waterbury/e-ink-driver/prior-art/e-ink/Datasheet/FH26-39S-0.3SHW(05).jpg

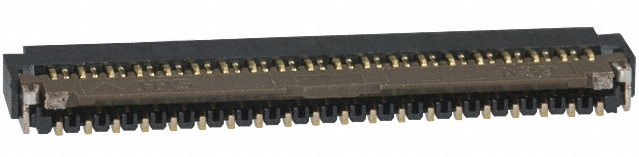
prior-art/e-ink/Datasheet/FH26-39S-0.3SHW(05).jpg
