waterbury/e-ink-driver/prior-art/e-ink/Datasheet/stm32f1xx-TQFP64.png

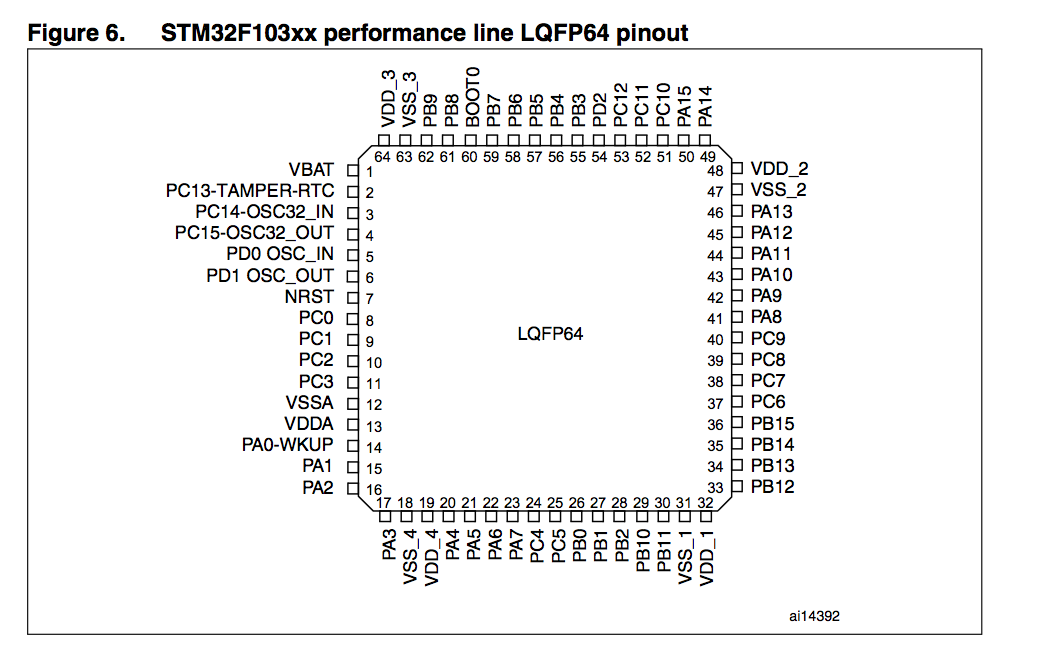
prior-art/e-ink/Datasheet/stm32f1xx-TQFP64.png
