waterbury/e-ink-driver/prior-art/e-ink/Firmware/e-ink-tests-v002/Resources/ED060SC4_driver-master/example_schematics.png

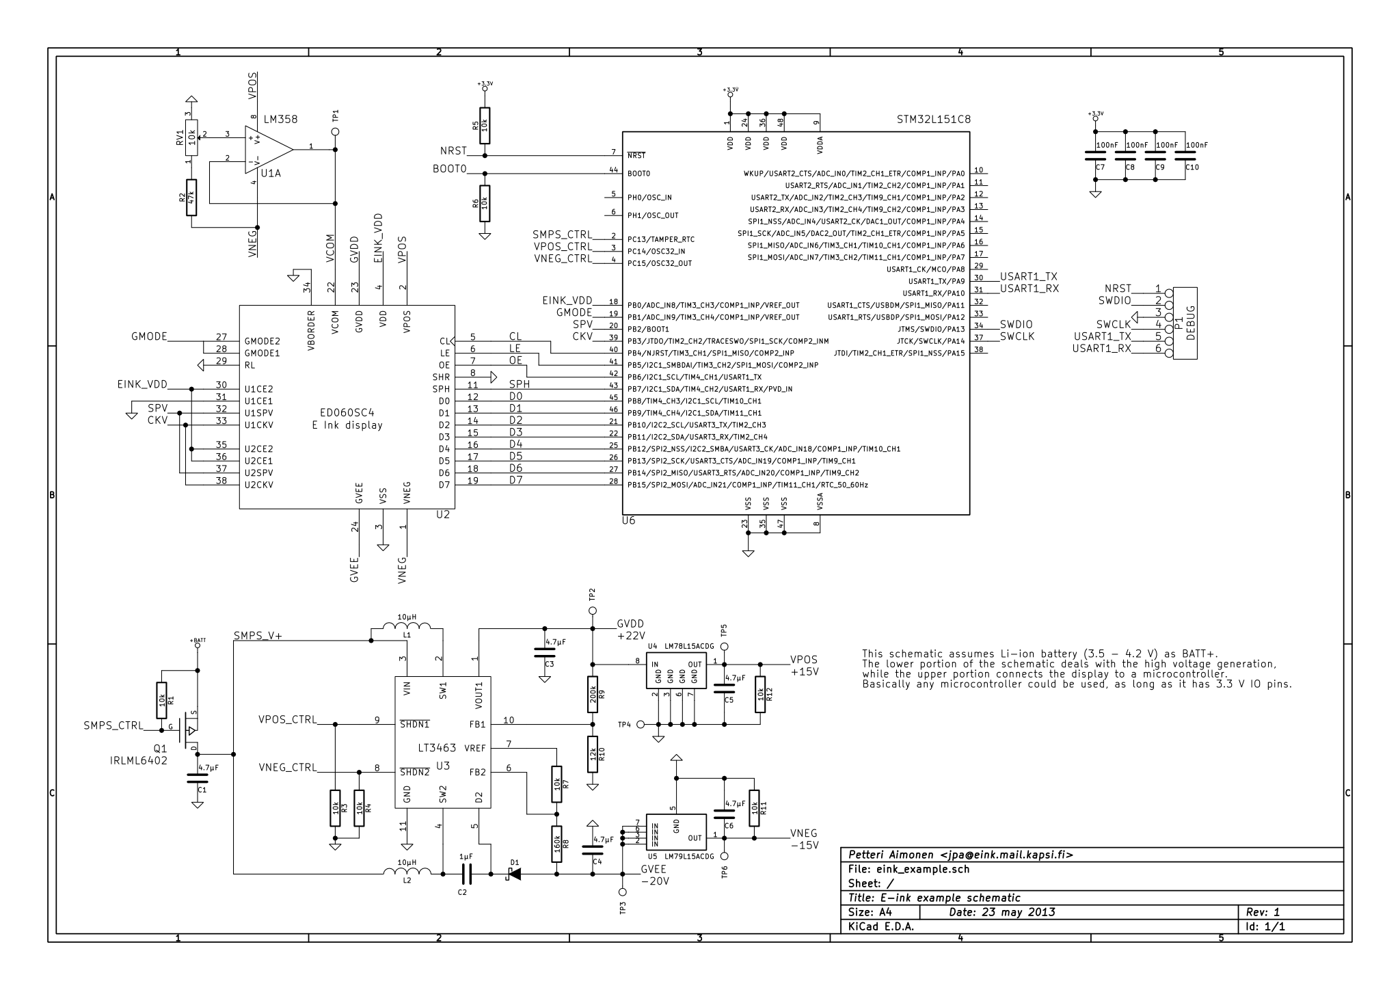
prior-art/e-ink/Firmware/e-ink-tests-v002/Resources/ED060SC4_driver-master/example_schematics.png
