waterbury/e-ink-driver/prior-art/e-ink/Images/v002/2-boards.JPG

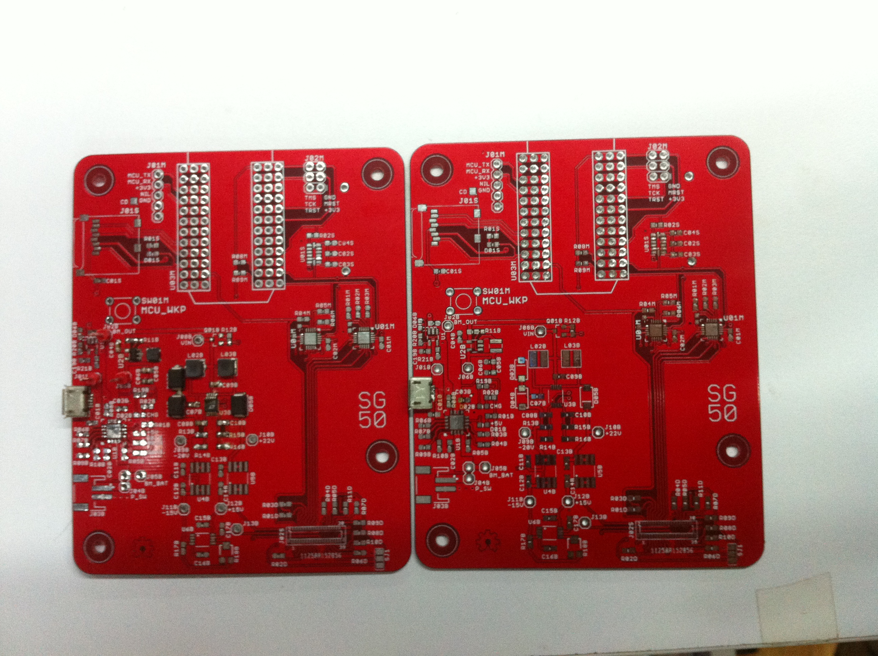
prior-art/e-ink/Images/v002/2-boards.JPG
