waterbury/e-ink-driver/prior-art/e-ink/Images/v002/display-closeup.JPG

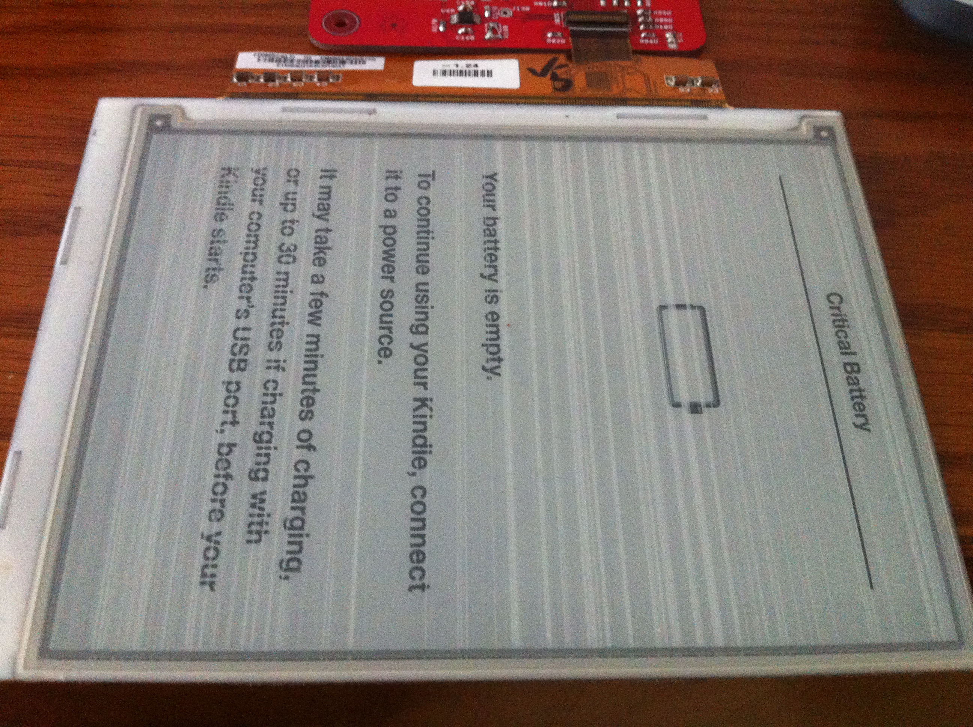
prior-art/e-ink/Images/v002/display-closeup.JPG
