waterbury/e-ink-driver/prior-art/e-ink/Research/example_schematics/schema_esp.png

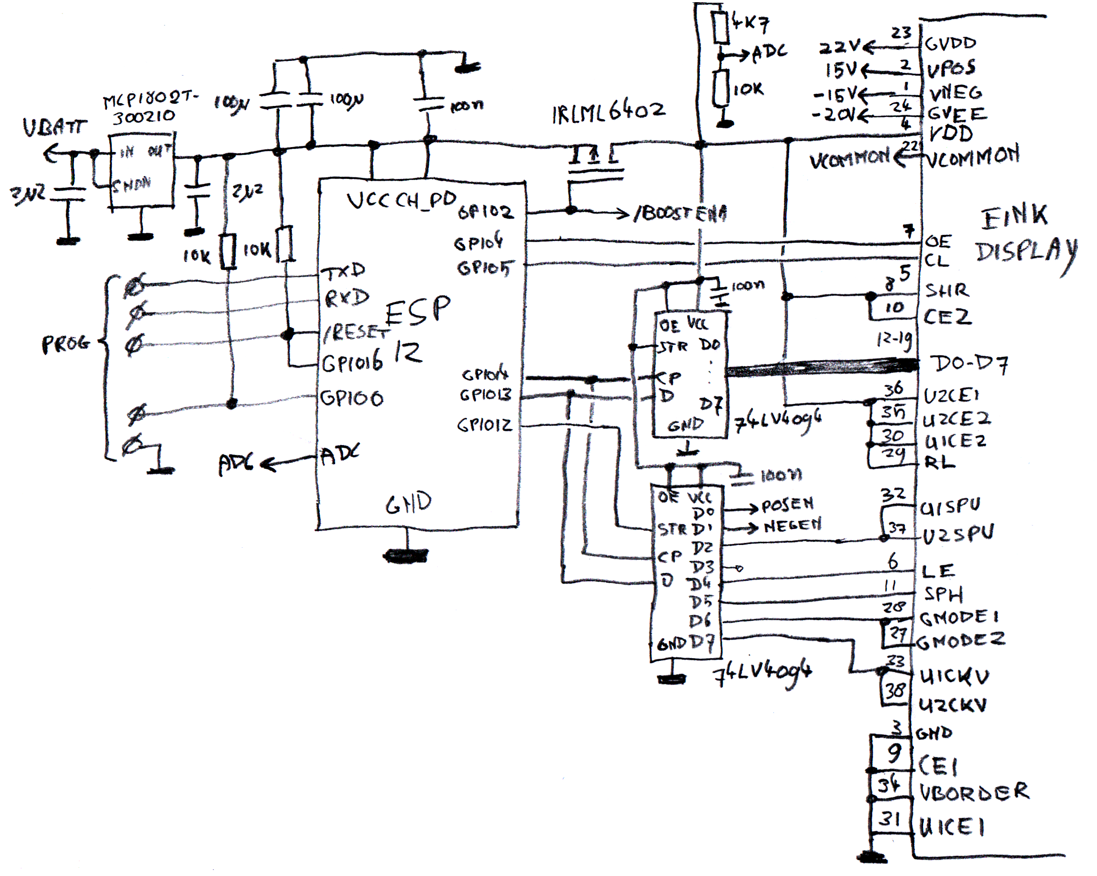
prior-art/e-ink/Research/example_schematics/schema_esp.png
