waterbury/e-ink-driver/prior-art/e-ink/Research/example_schematics/schema_power.png

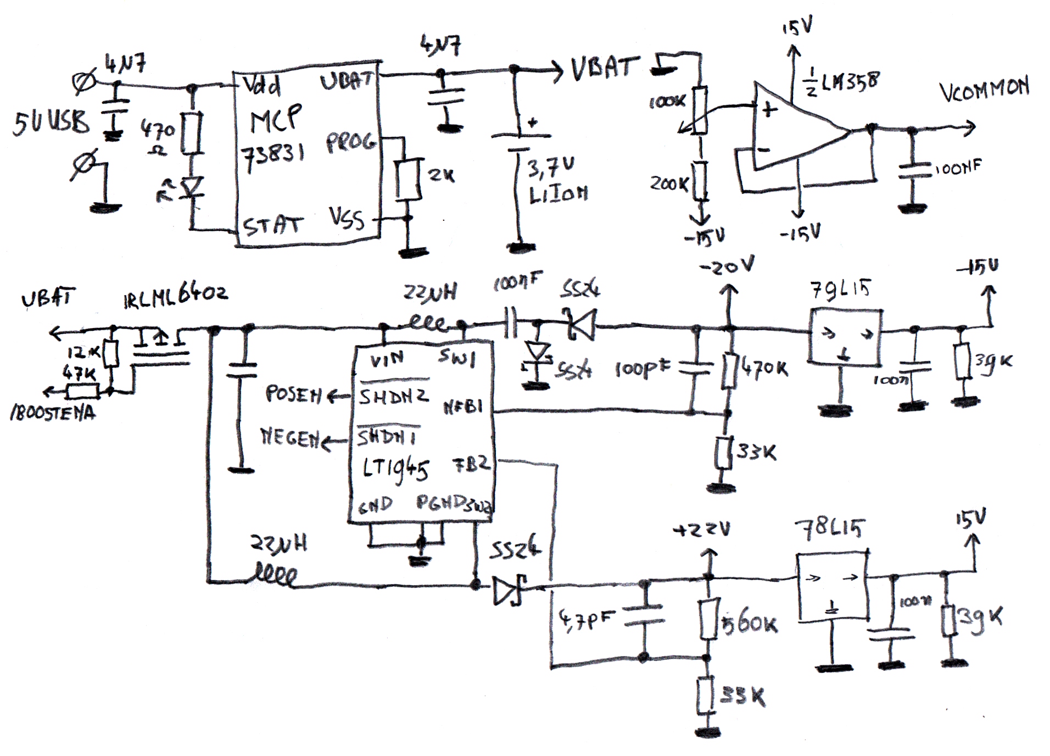
prior-art/e-ink/Research/example_schematics/schema_power.png
