waterbury/e-ink-driver/prior-art/e-ink/Research/example_schematics/Screen Shot 2015-03-17 at 8.35.07.png

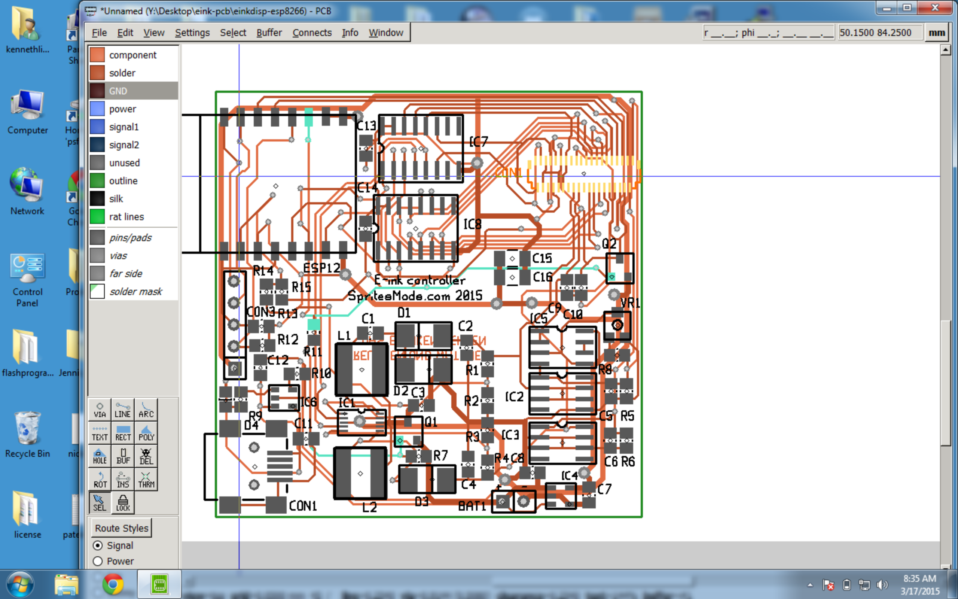
prior-art/e-ink/Research/example_schematics/Screen Shot 2015-03-17 at 8.35.07.png
