waterbury/e-ink-driver/prior-art/e-ink/Research/G6_eink_schematic.png

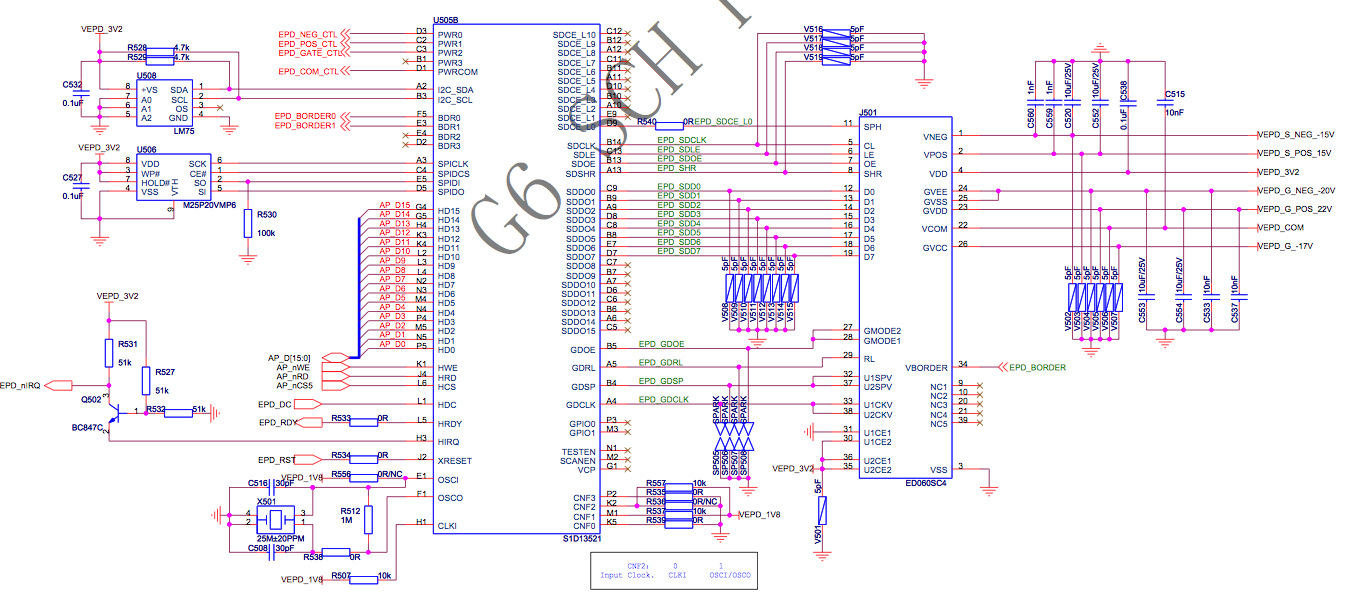
prior-art/e-ink/Research/G6_eink_schematic.png
