waterbury/e-ink-driver/prior-art/e-ink/Research/USB_DISC.png

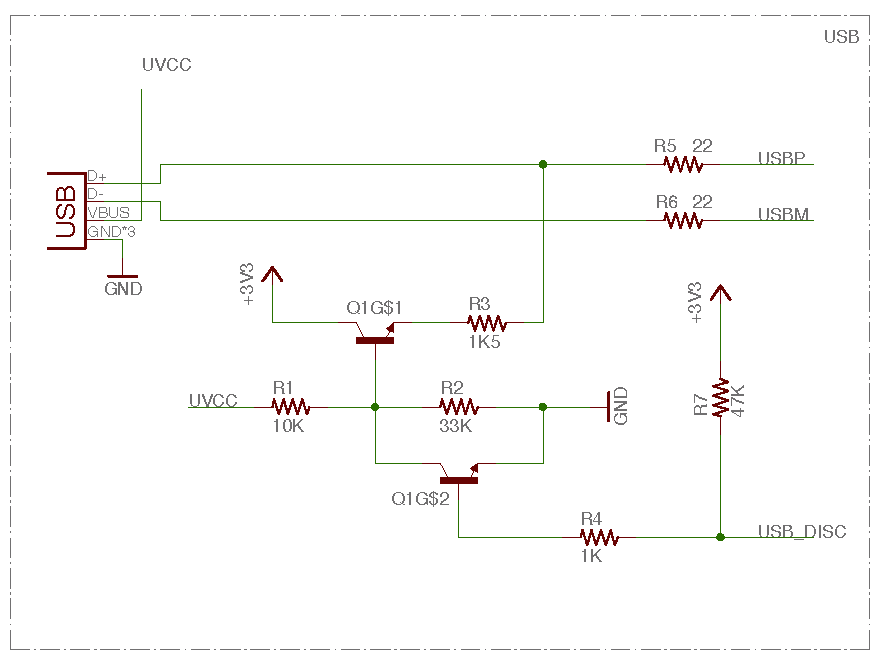
prior-art/e-ink/Research/USB_DISC.png
