waterbury/e-ink-driver/prior-art/e-ink/Bring-up/V020/V020-notes-print.pages/preview-web.jpg

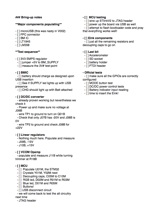
prior-art/e-ink/Bring-up/V020/V020-notes-print.pages/preview-web.jpg
