waterbury/e-ink-driver/prior-art/e-ink/Bring-up/V020/Screenshots/ground-plane.png

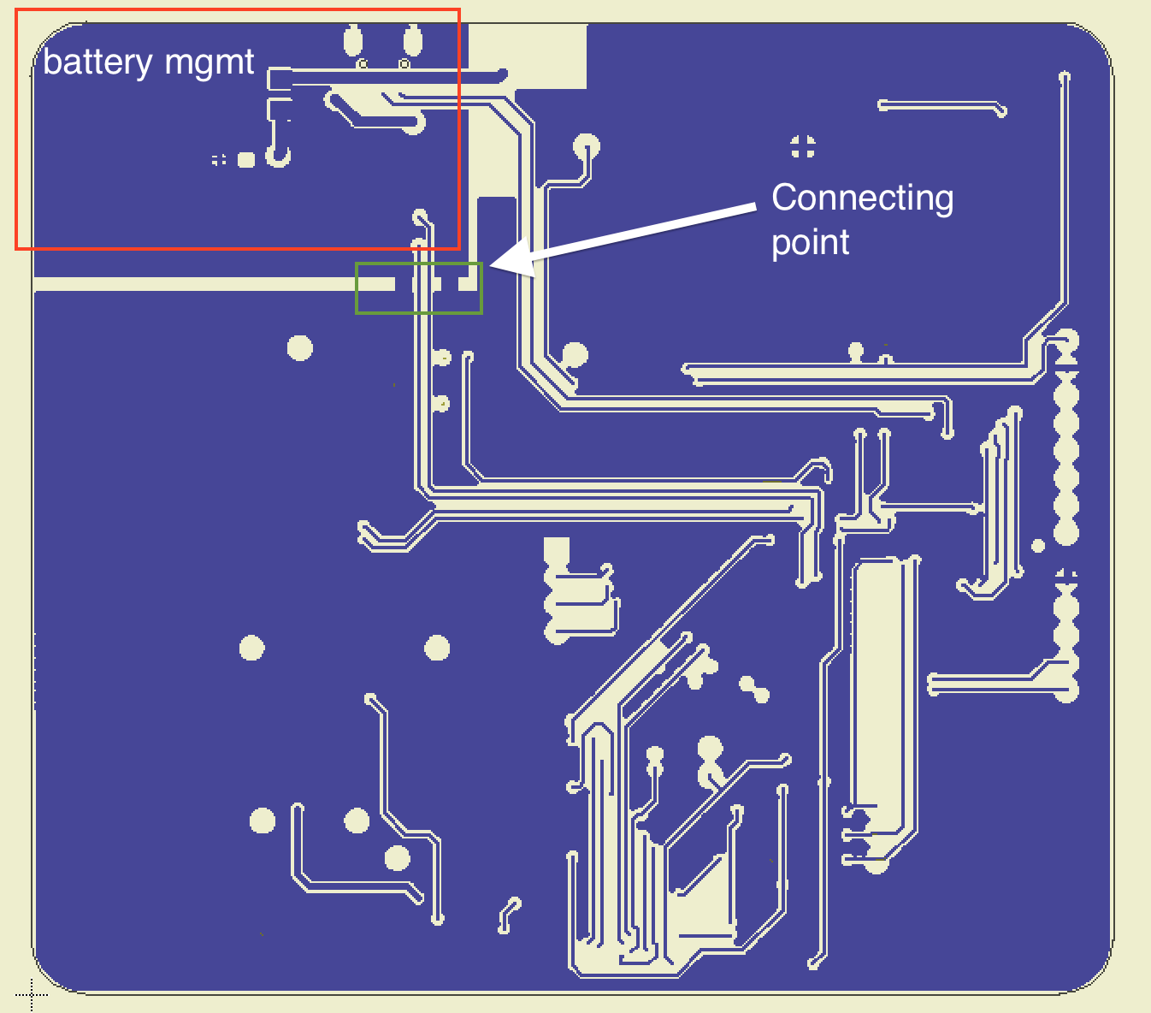
prior-art/e-ink/Bring-up/V020/Screenshots/ground-plane.png
