waterbury/e-ink-driver/prior-art/e-ink/EAGLE/e-ink-display-v120/e-ink-display-v120/e-ink-display-v120/e-ink-display-v120.pdf

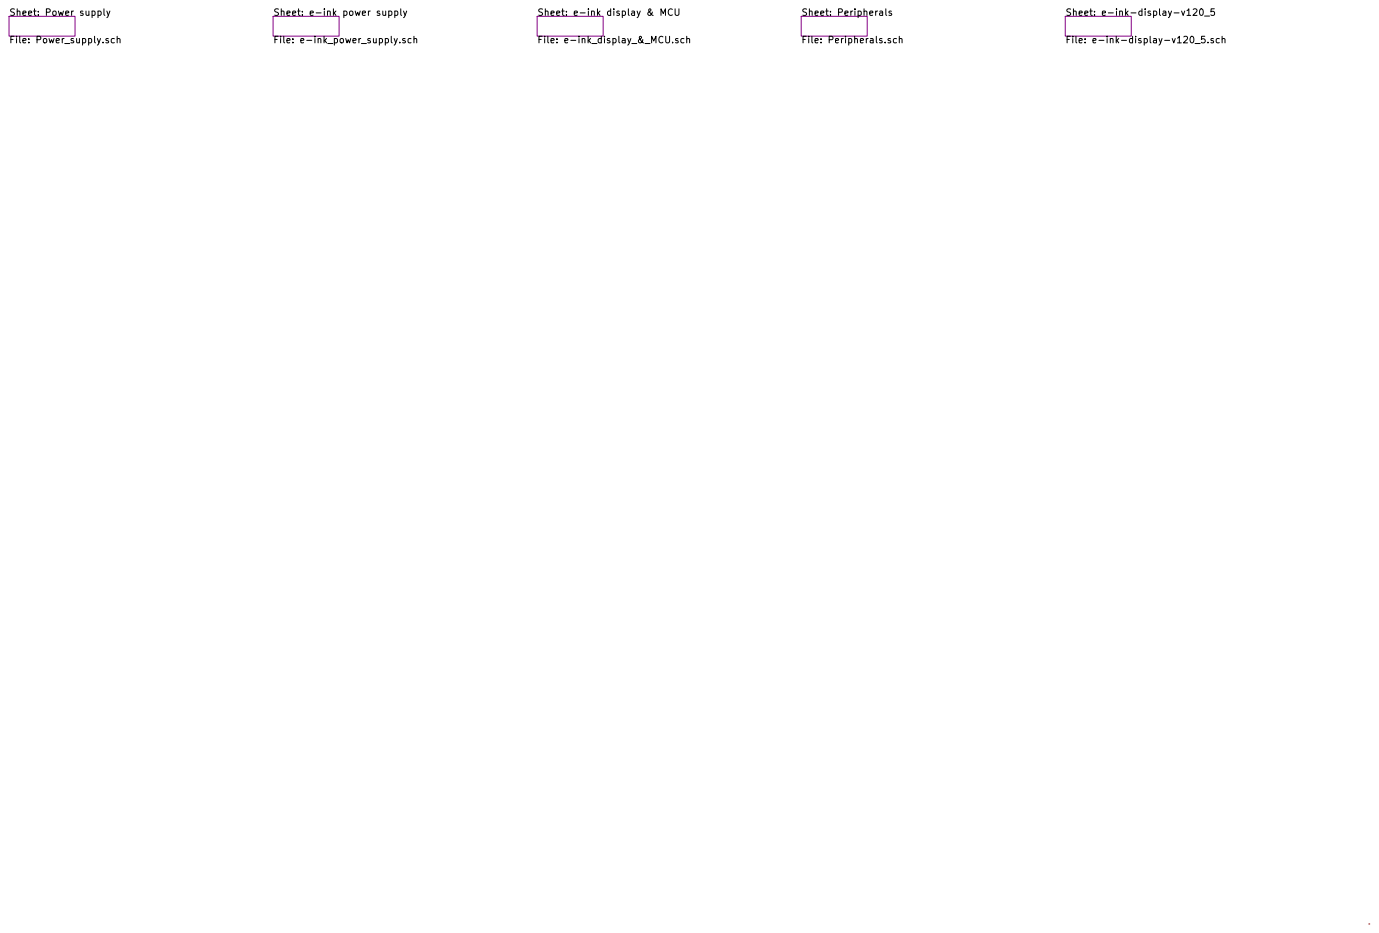
[picture p19: page 1]

Sheet: e-ink power supply

Sheet: e-ink display & MCU

File: e-ink-display-v120_5.sch

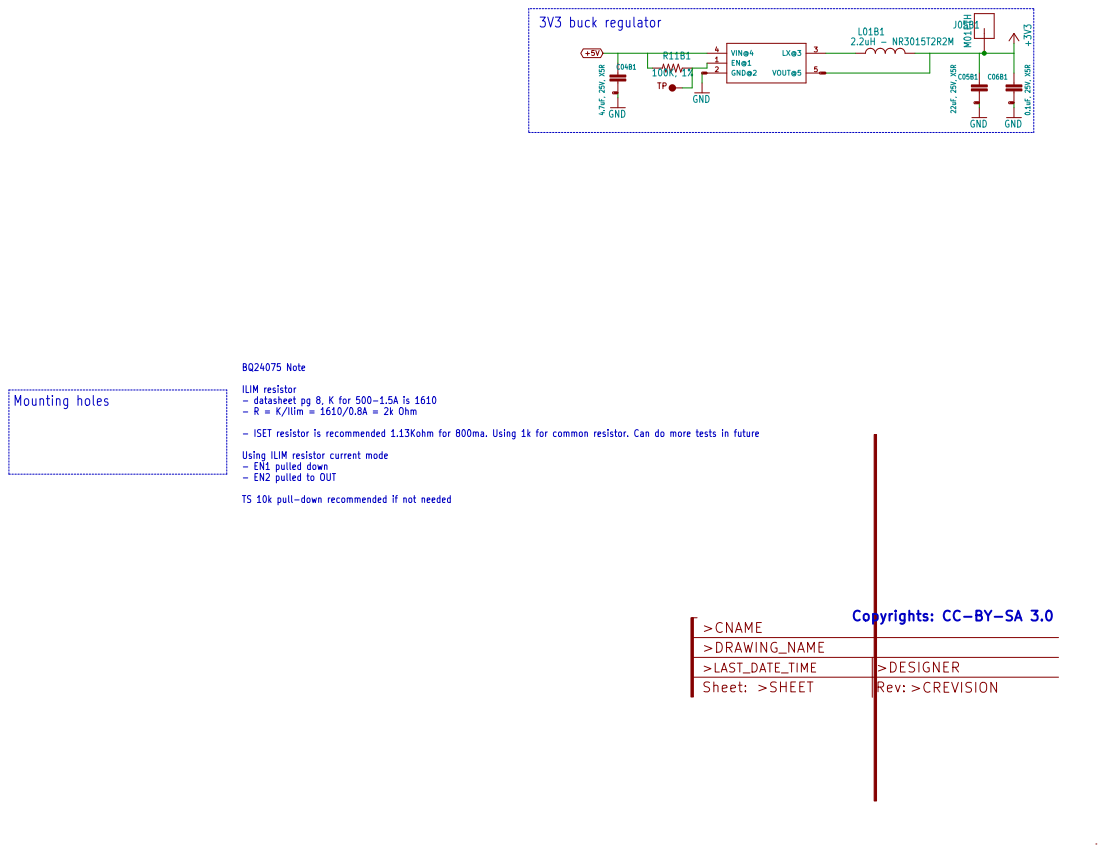
[picture p20: page 2]

ILIM resistor
- datasheet pg 8, K for 500-1.5A is 1610
- R = K/Ilim = 1610/0.8A = 2k Ohm

- ISET resistor is recommended 1.13Kohm for 800ma. Using 1k for common resistor. Can do more tests in future

Using ILIM resistor current mode
- EN1 pulled down
- EN2 pulled to OUT

TS 10k pull-down recommended if not needed

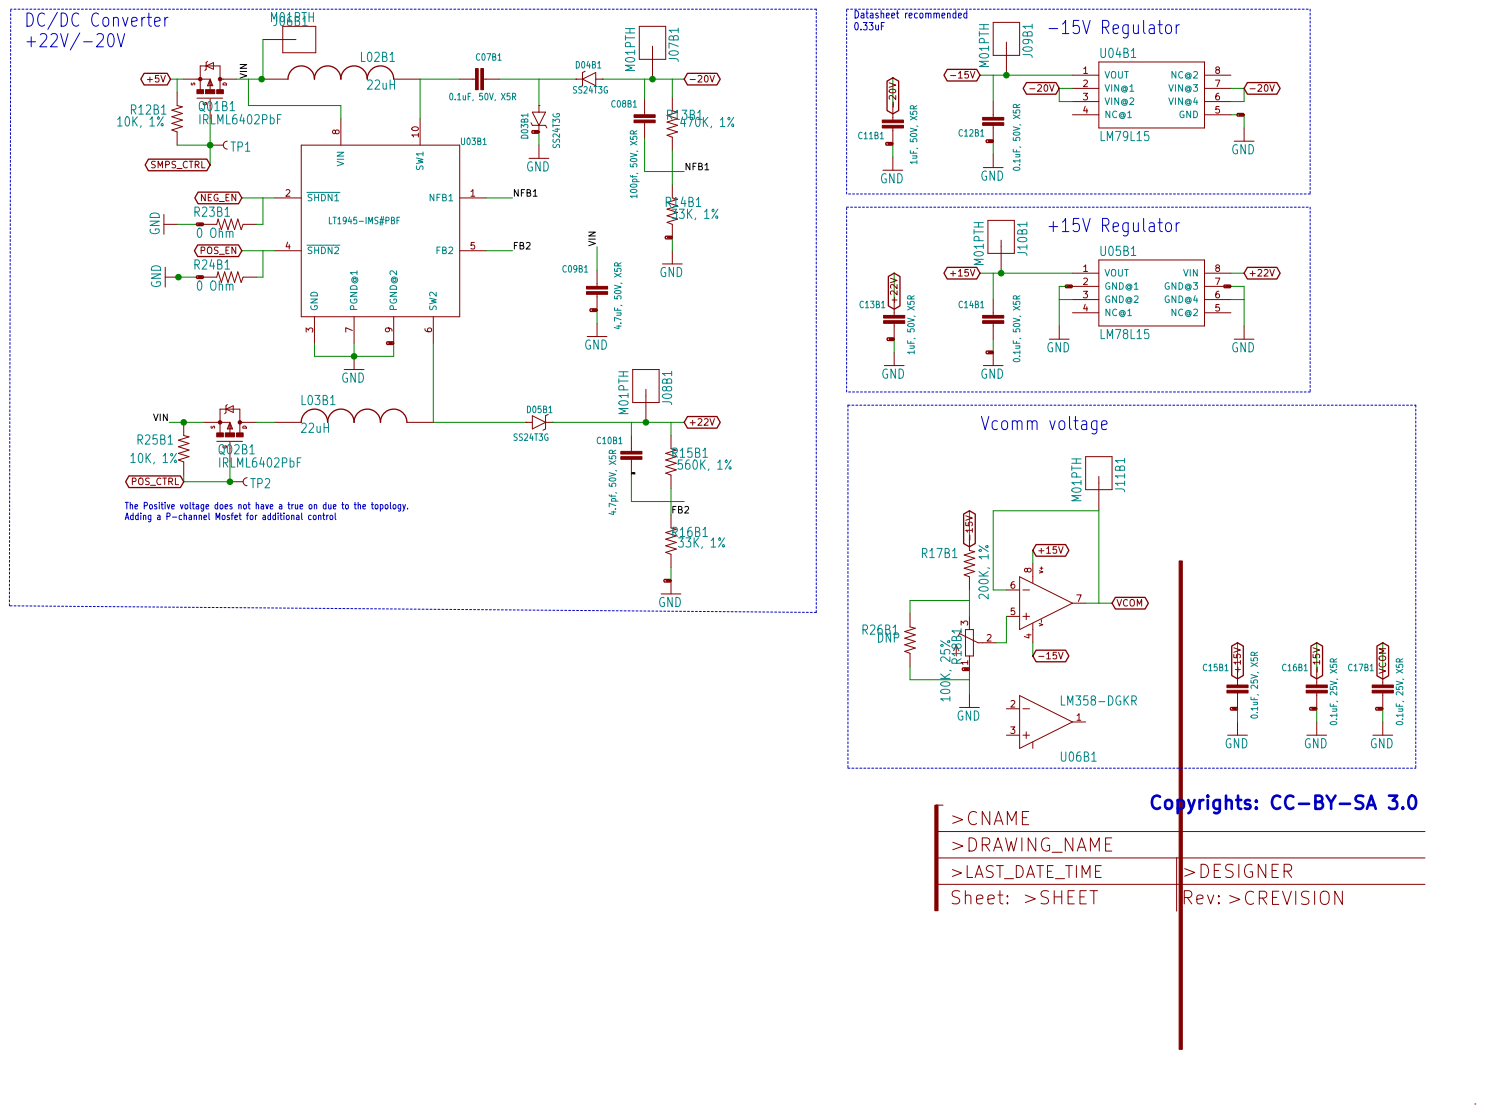
[picture p21: page 3]

FB2 FB2 The Positive voltage does not have a true on due to the topology.

Adding a P-channel Mosfet for additional control

Copyrights: CC-BY-SA 3.0

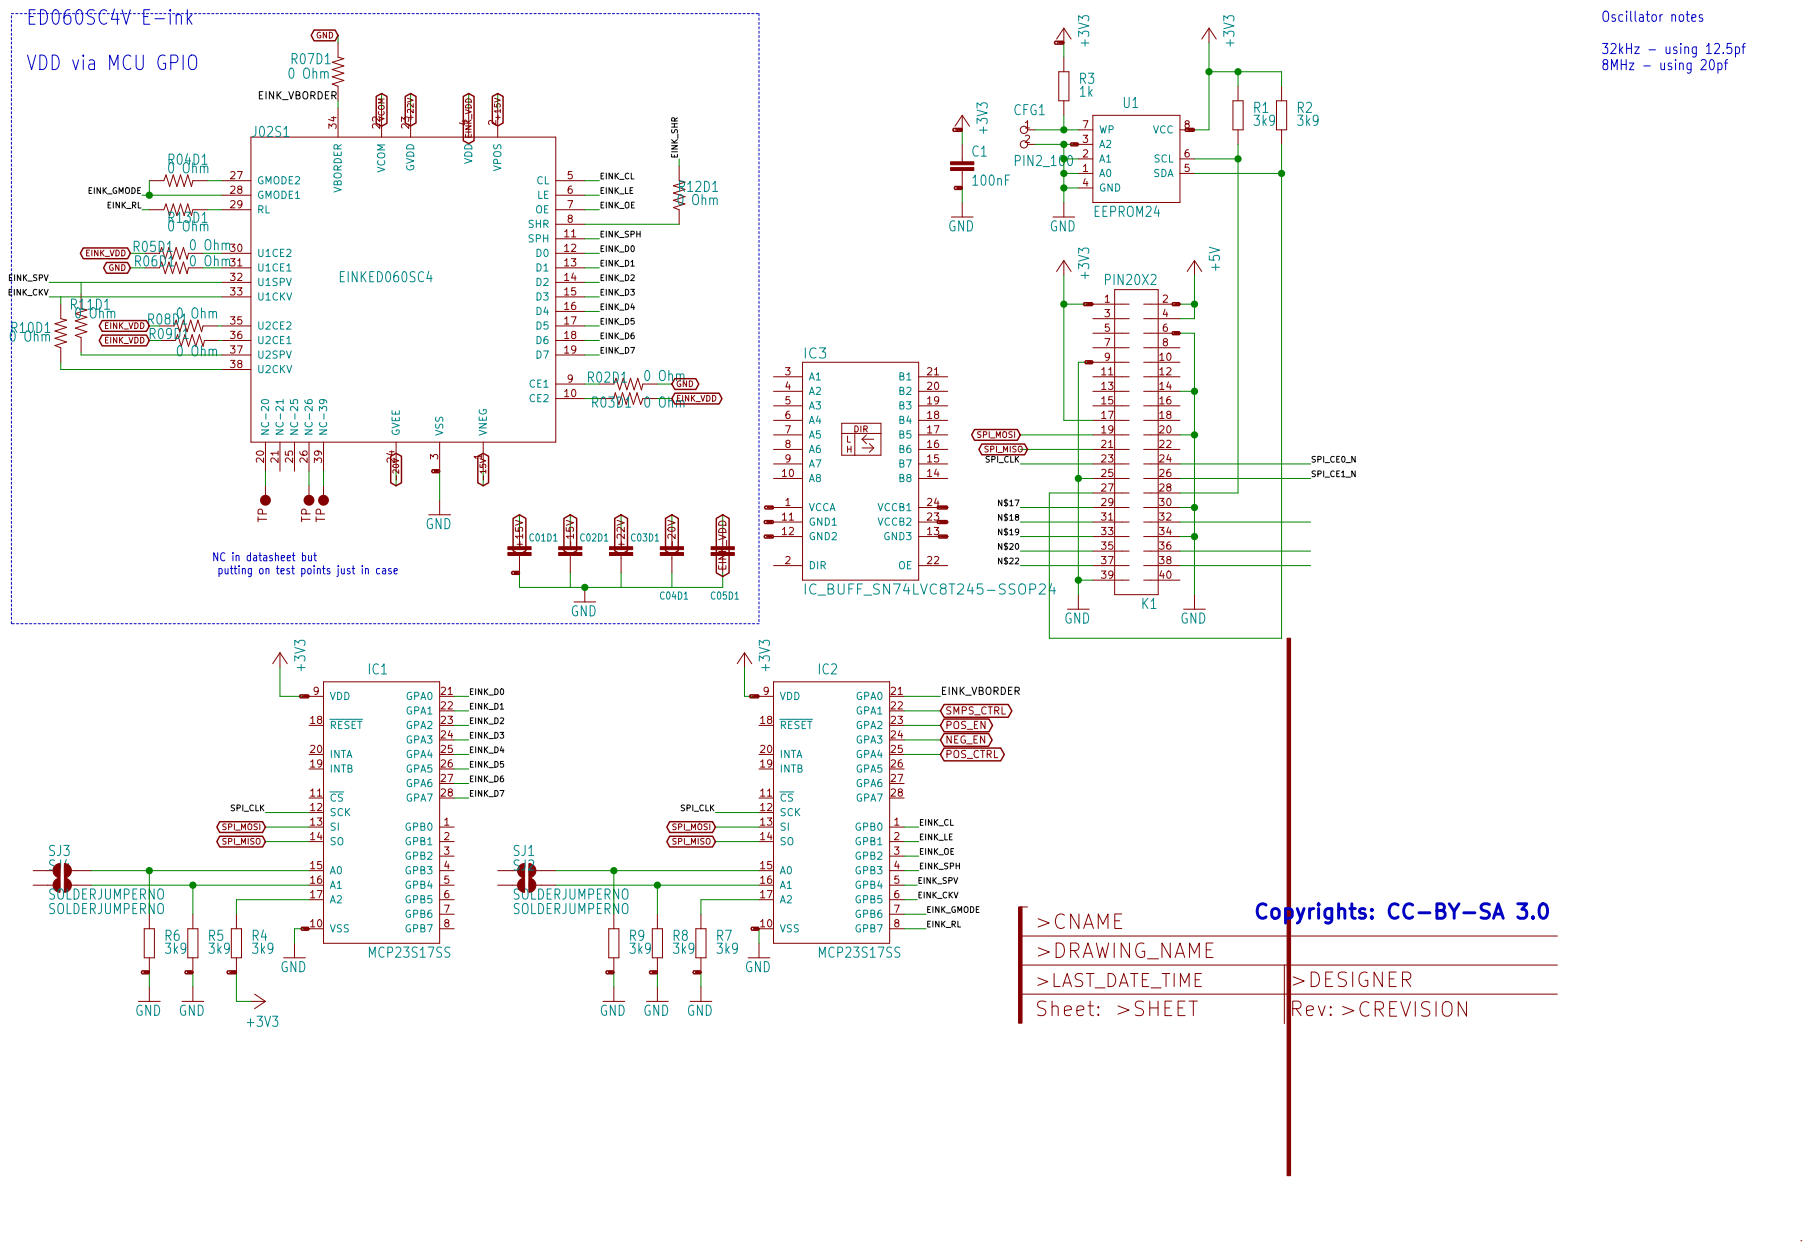
[picture p22: page 4]

VDD via MCU GPIO

2 NC-20 20 NC-21 21 VCOM 22 GVDD 23 GVEE 24 NC-25 25 NC-26 26 GMODE2 27 GMODE1 28 RL 29 VSS
3k9 VNEG

23 | | 24
25 | | 26
27 | | 28
29 | | 30
31 | | 32
33 | | 34
35 | | 36
37 | | 38
39 | | 40

NC in datasheet but
putting on test points just in case

Copyrights: CC-BY-SA 3.0

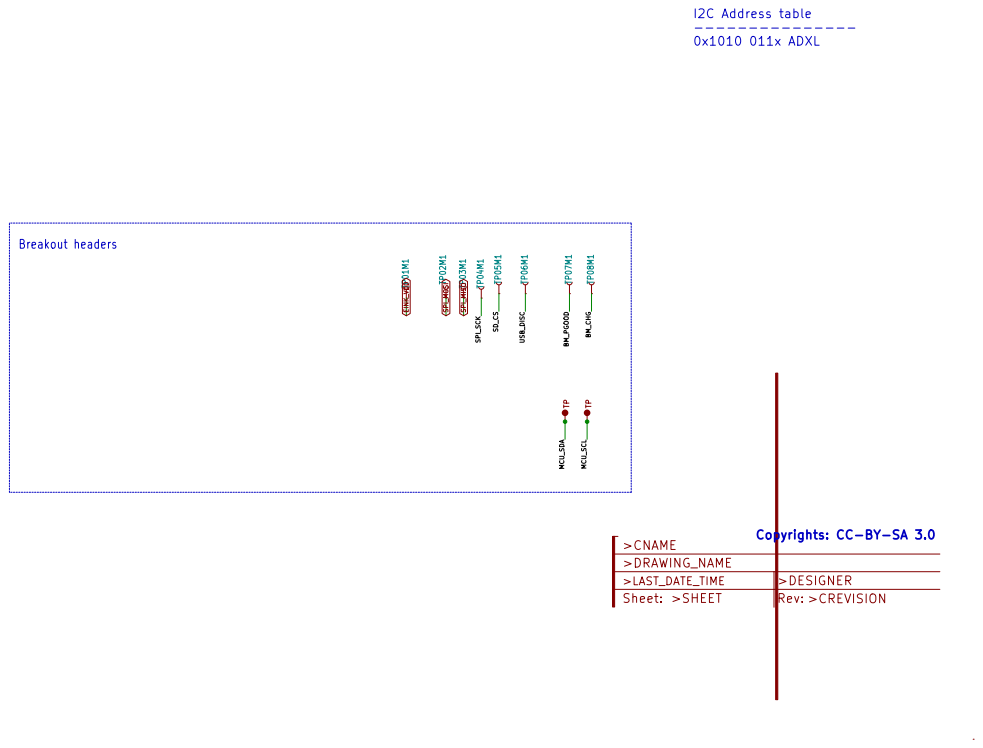
[picture p23: page 5]

Copyrights: CC-BY-SA 3.0

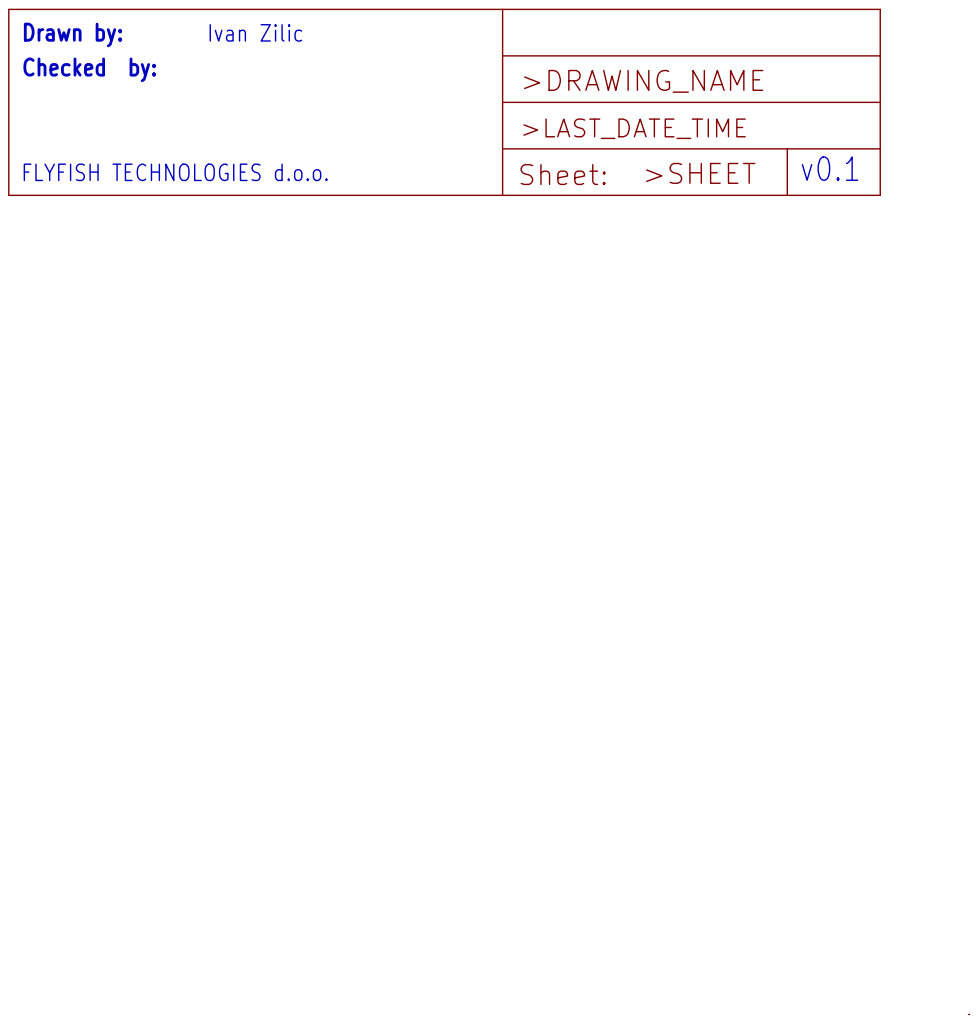
[picture p24: page 6]
