waterbury/e-ink-driver/prior-art/e-ink/Research/example_schematics/eink-pcb/einkdisp-esp8266.pdf

# einkdisp-esp8266

# 1. Table of Contents (This Page) Created on Sun Feb 15 16:48:41 2015

# 2. component 3. solder 4. outline 5. plated-drill 6. componentmask 7. soldermask 8. topsilk 9. bottomsilk 10. toppaste 11. topassembly 12. bottomassembly 13. fab

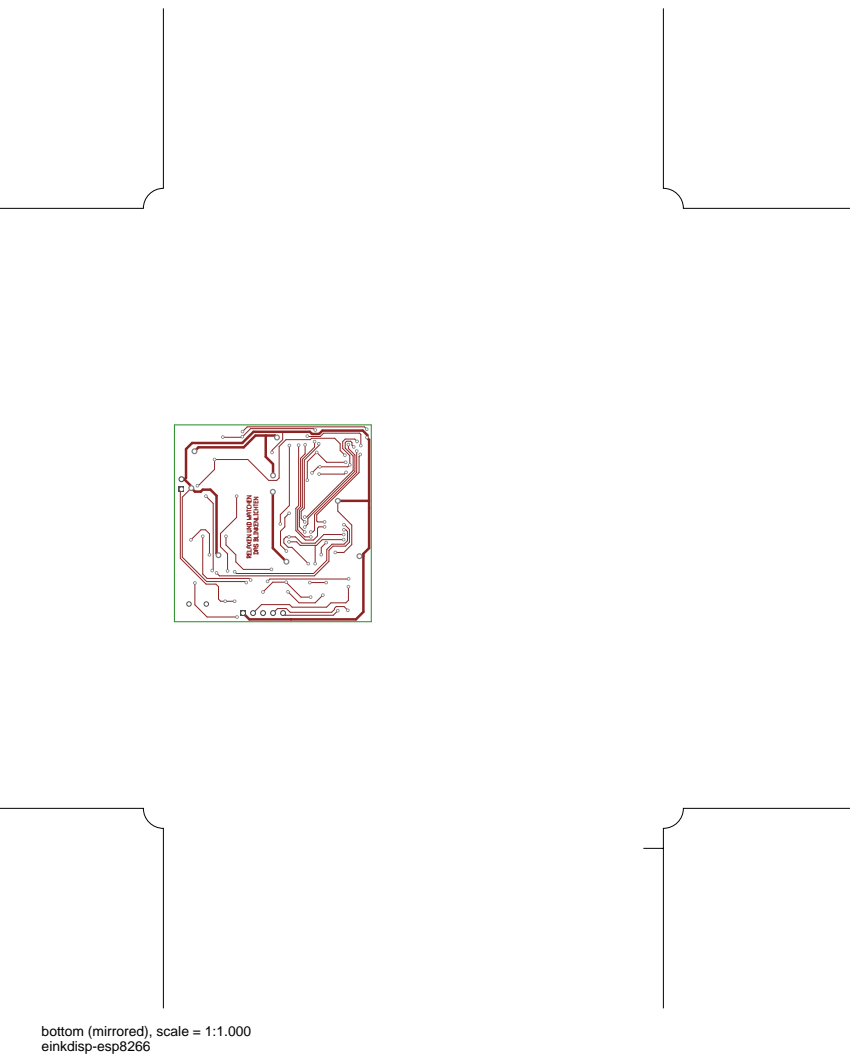
[picture p25: page 2]

bottom (mirrored), scale = 1:1.000

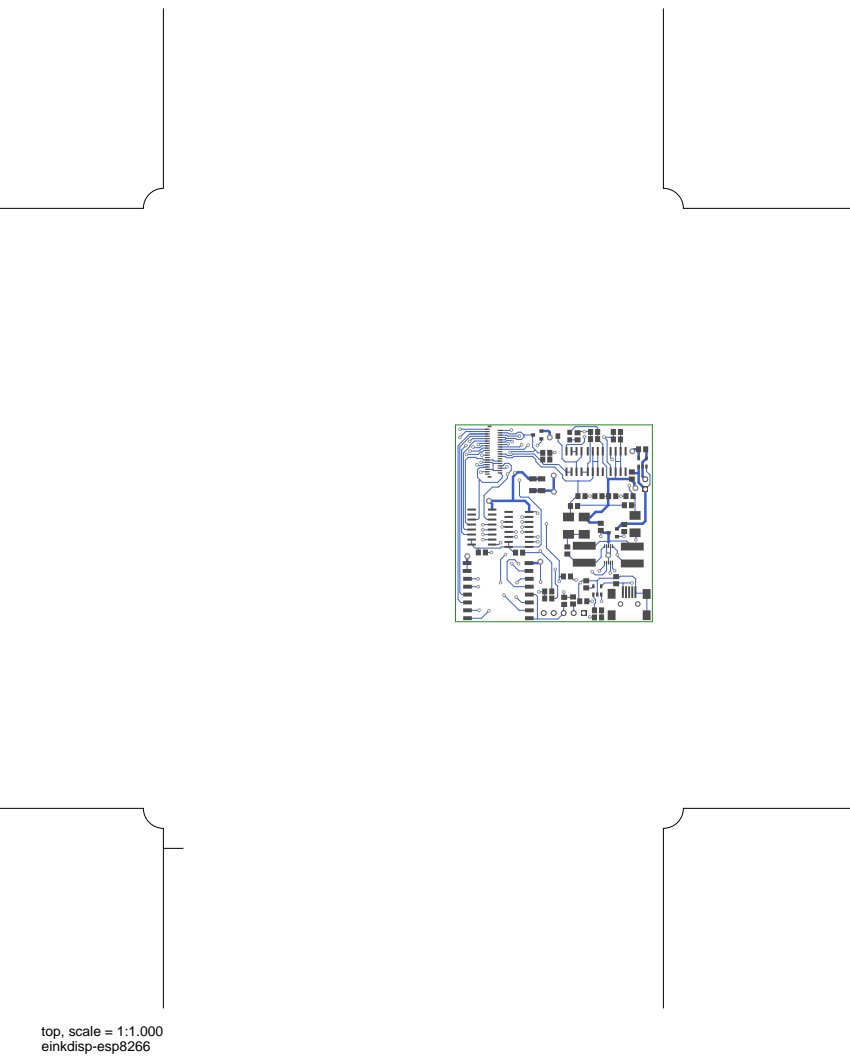
[picture p26: page 3]
top, scale = 1:1.000

outline, scale = 1:1.000

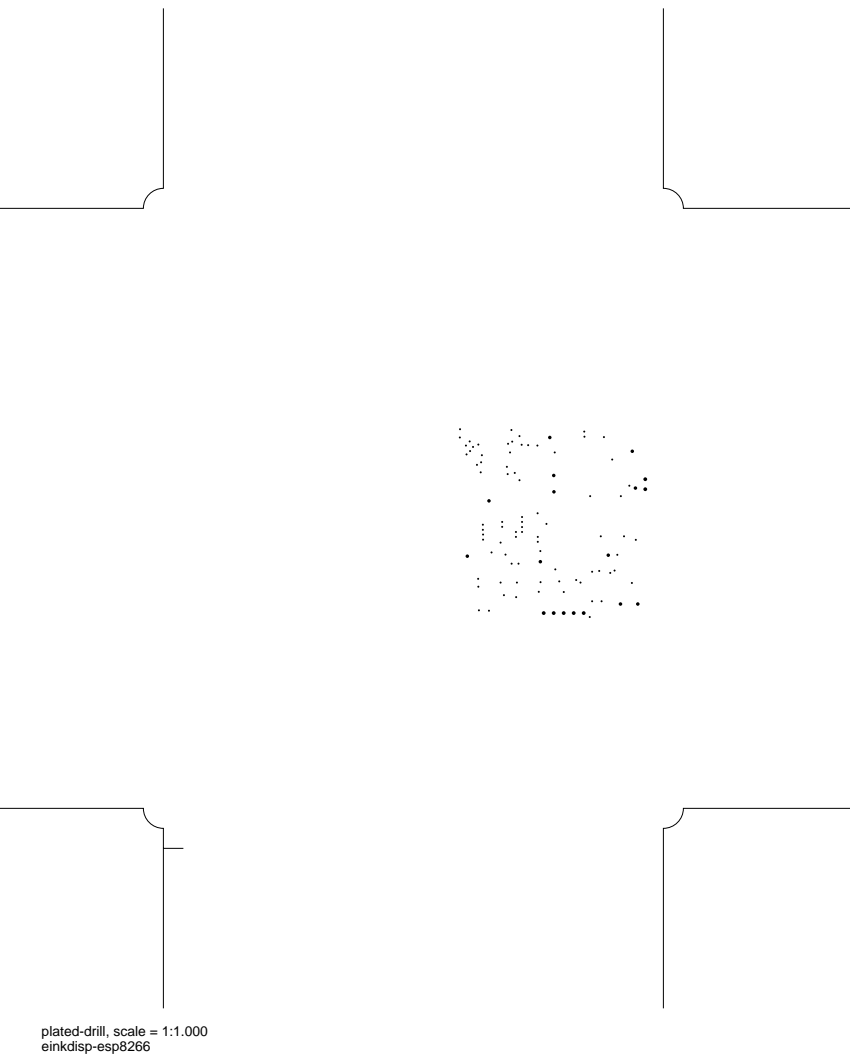
[picture p27: page 5]

plated-drill, scale = 1:1.000

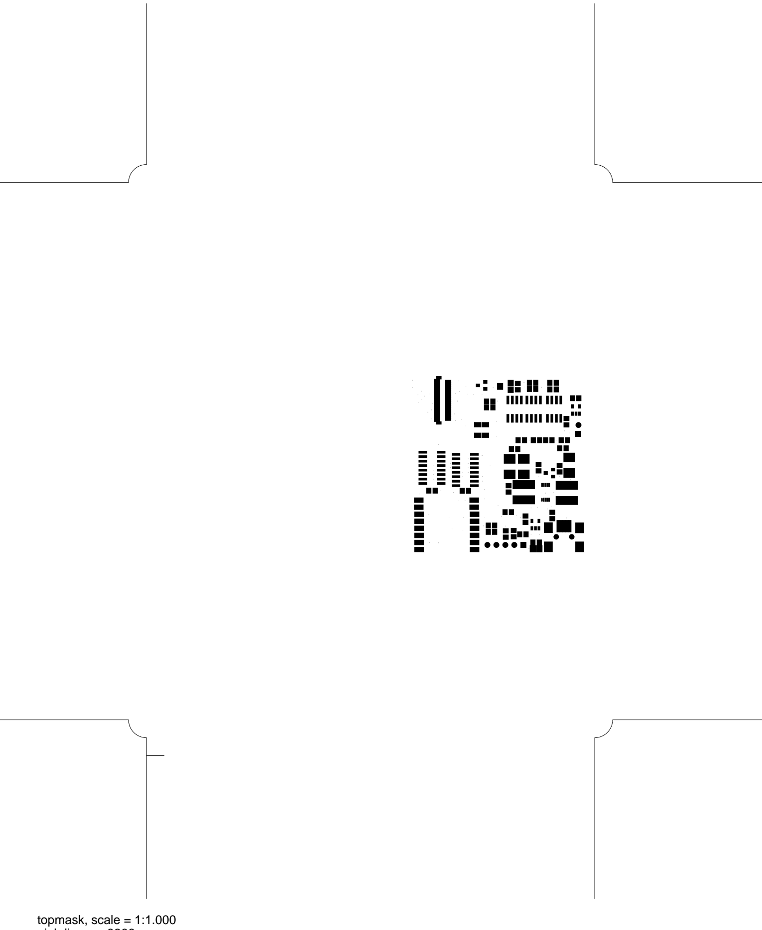
[picture p28: figure]
topmask, scale = 1:1.000

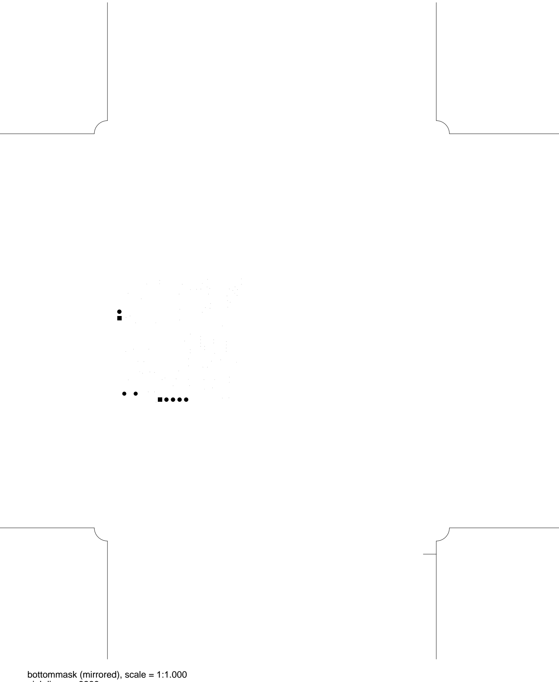
[picture p29: figure]
bottommask (mirrored), scale = 1:1.000
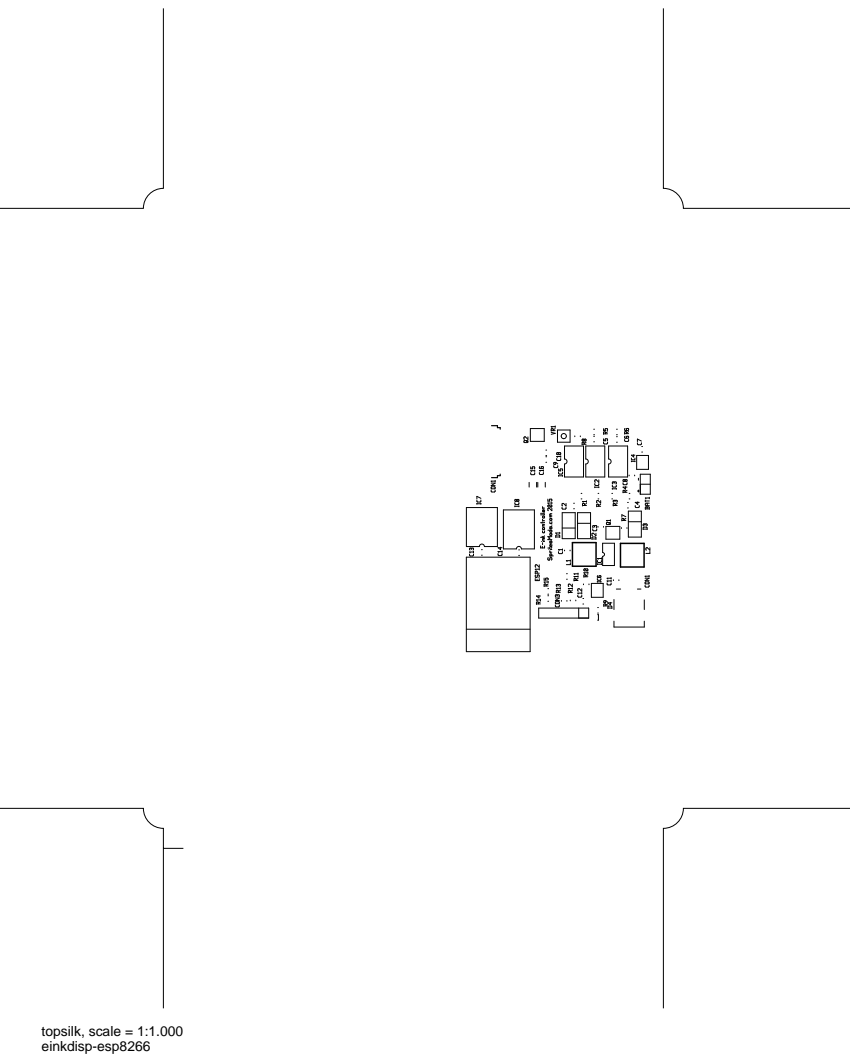
[picture p30: page 8]
topsilk, scale = 1:1.000

bottomsilk (mirrored), scale = 1:1.000

toppaste, scale = 1:1.000

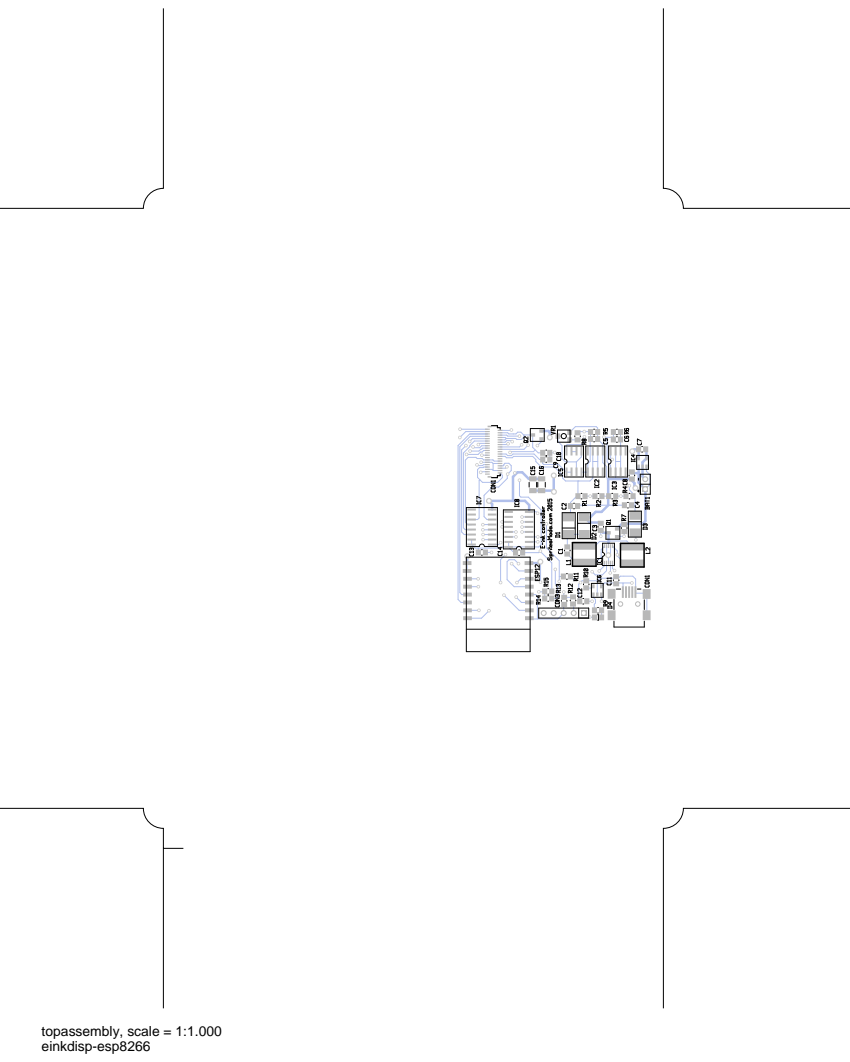
[picture p31: page 11]
topassembly, scale = 1:1.000

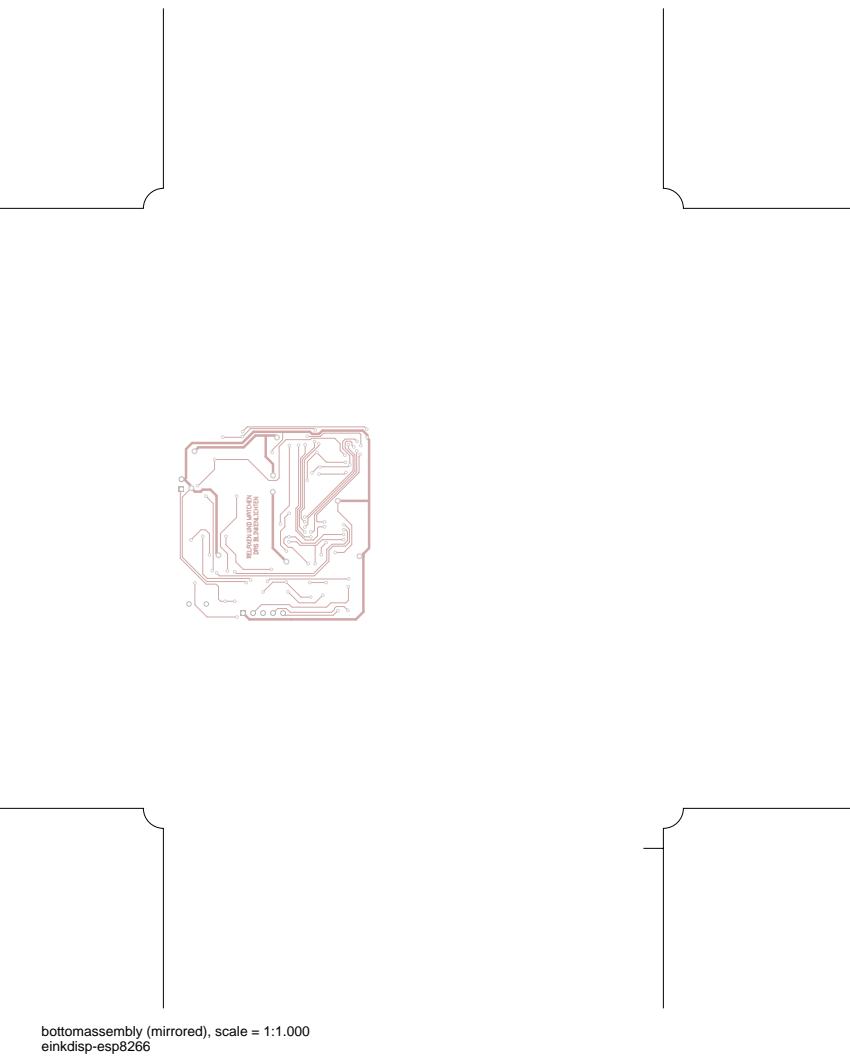
[picture p32: page 12]

bottomassembly (mirrored), scale = 1:1.000

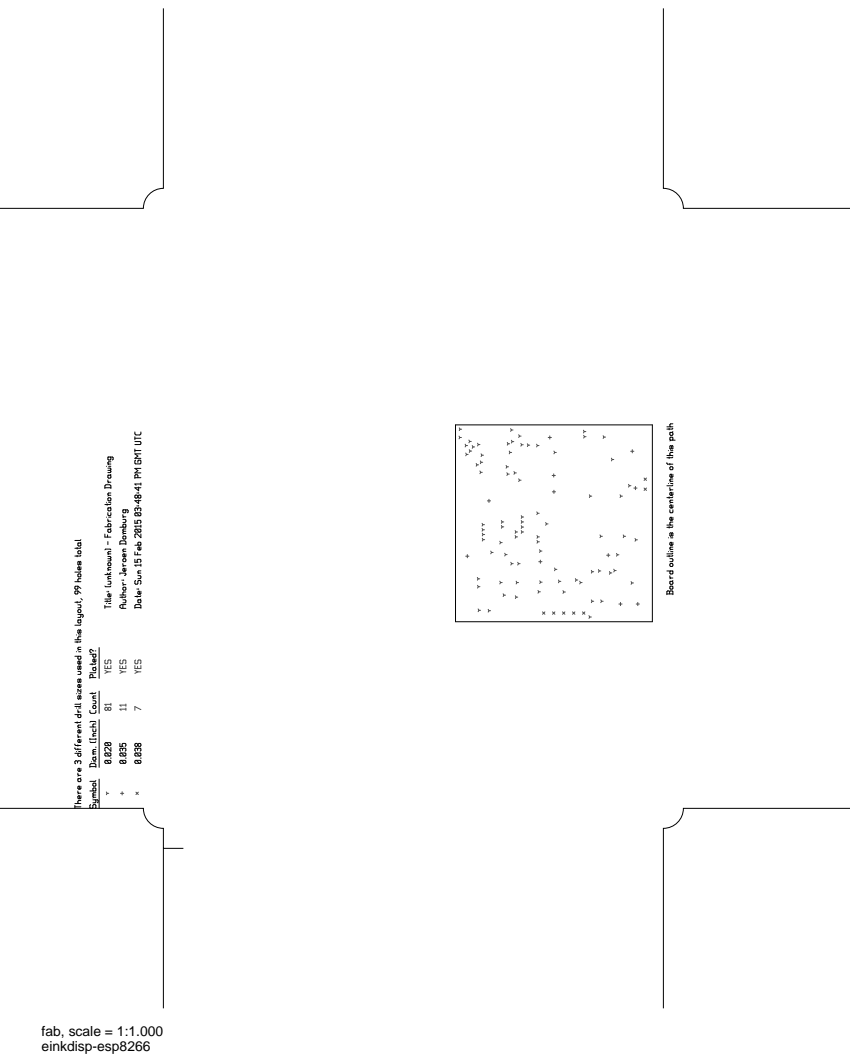
[picture p33: page 13]
fab, scale = 1:1.000
