waterbury/e-ink-driver/prior-art/e-ink/Research/G6_ebook_reader_schematics.pdf

D

D

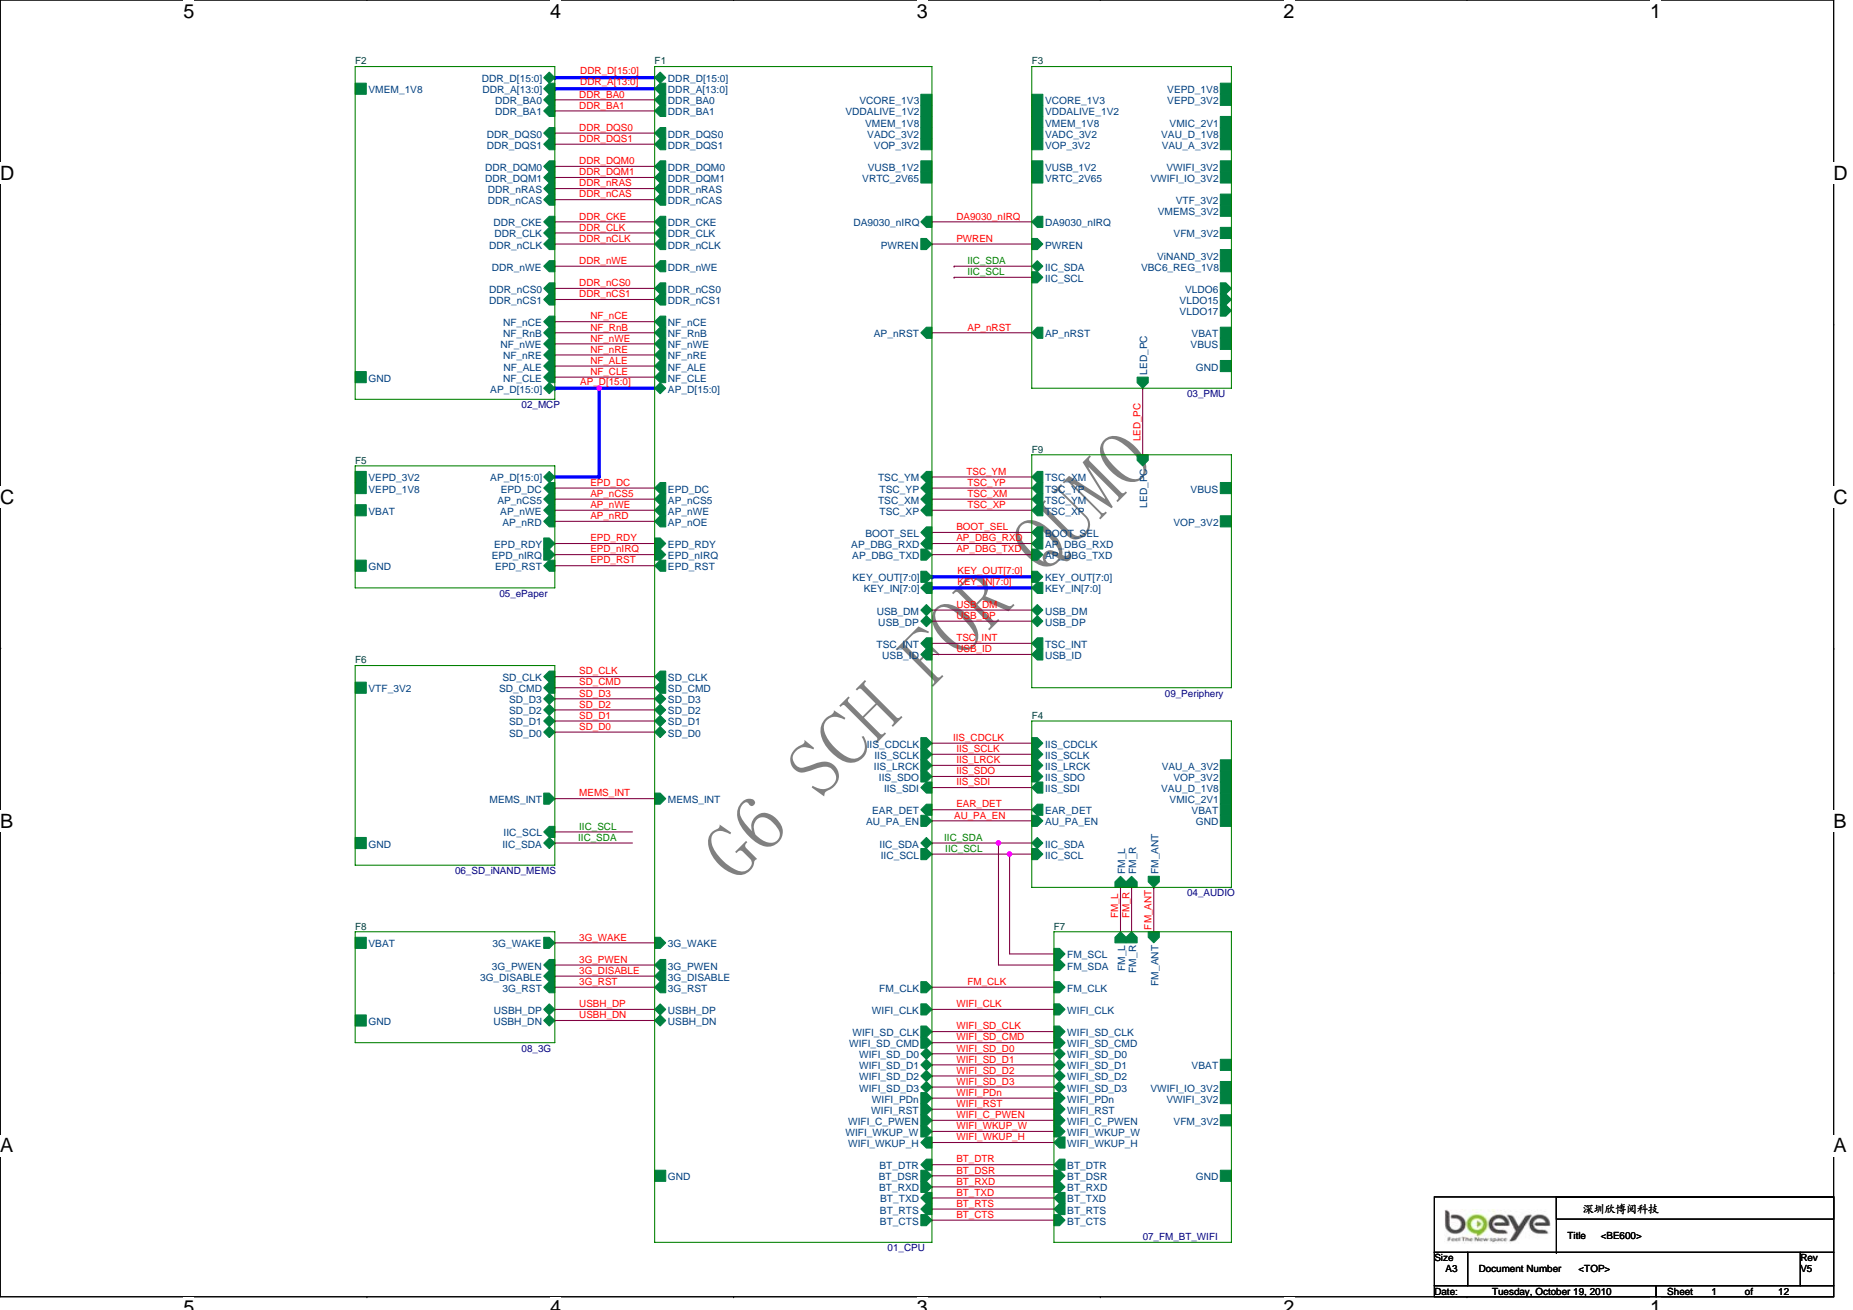
[picture p34: page 1]
DDR_BA0; DDR_D[15:0] DDR_A[13:0]; DDR_BA1; DDR_DQS0 DDR_DQS1; DDR_DQM0 DDR_DQM1 DDR_nRAS DDR_nCAS; DDR_CKE DDR_CLK DDR_nCLK; DDR_nWE; DDR_nCS0 DDR_nCS1; NF_nCE NF_RnB NF_nWE NF_nRE NF_ALE NF_CLE; AP_nRST; DA9030_nIRQ; PWREN; EPD_DC; EPD_RDY; IIS_CDCLK IIS_SCLK IIS_LRCK IIS_SDO IIS_SDI; IIC_SDA IIC_SCL; SD_CLK SD_CMD SD_D3 SD_D2 SD_D1 SD_D0; IIC_SCL; IIC_SDA; IIC_SCL IIC_SDA; EAR_DET; TSC_YM TSC_YP; KEY_IN[7:0]; USB_DM USB_DP; USB_ID; FM_ANT; AP_DBG_RXD; TSC_INT; LED_PC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

G6 SCH FOR QUMO

AP_nCS5 | TSC_XM
AP_nWE | TSC_XP
AP_nRD | BOOT_SEL

EPD_nIRQ | AP_DBG_TXD
EPD_RST | KEY_OUT[7:0]

USBH_DP | WIFI_CLK
USBH_DN | WIFI_SD_CLK

Size A3 | Document Number <TOP> <TOP> <TOP> | Rev V5 V5 V5

Date: Tuesday, October 19, 2010 Tuesday, October 19, 2010 Tuesday, October 19, 2010 | Sheet 1 1 1 of 12 12 12

5 | 4 | 3 | 2 | 1

D

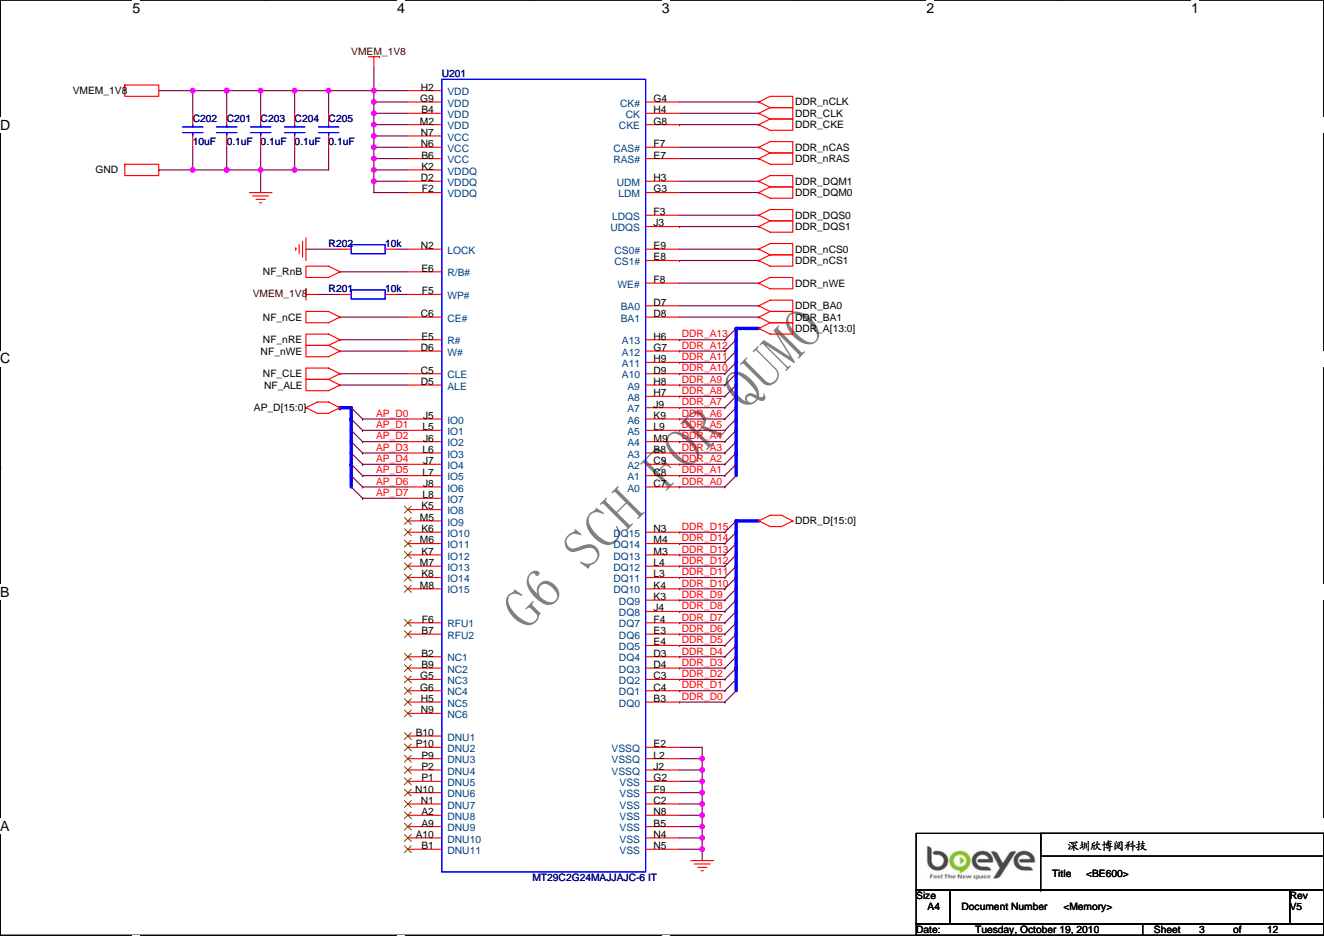
[picture p35: page 2]

<Memory> <Memory> <Memory> | V5 V5 V5

Tuesday, October 19, 2010 Tuesday, October 19, 2010 Tuesday, October 19, 2010 | 3 3 3 12 12 12

D | D

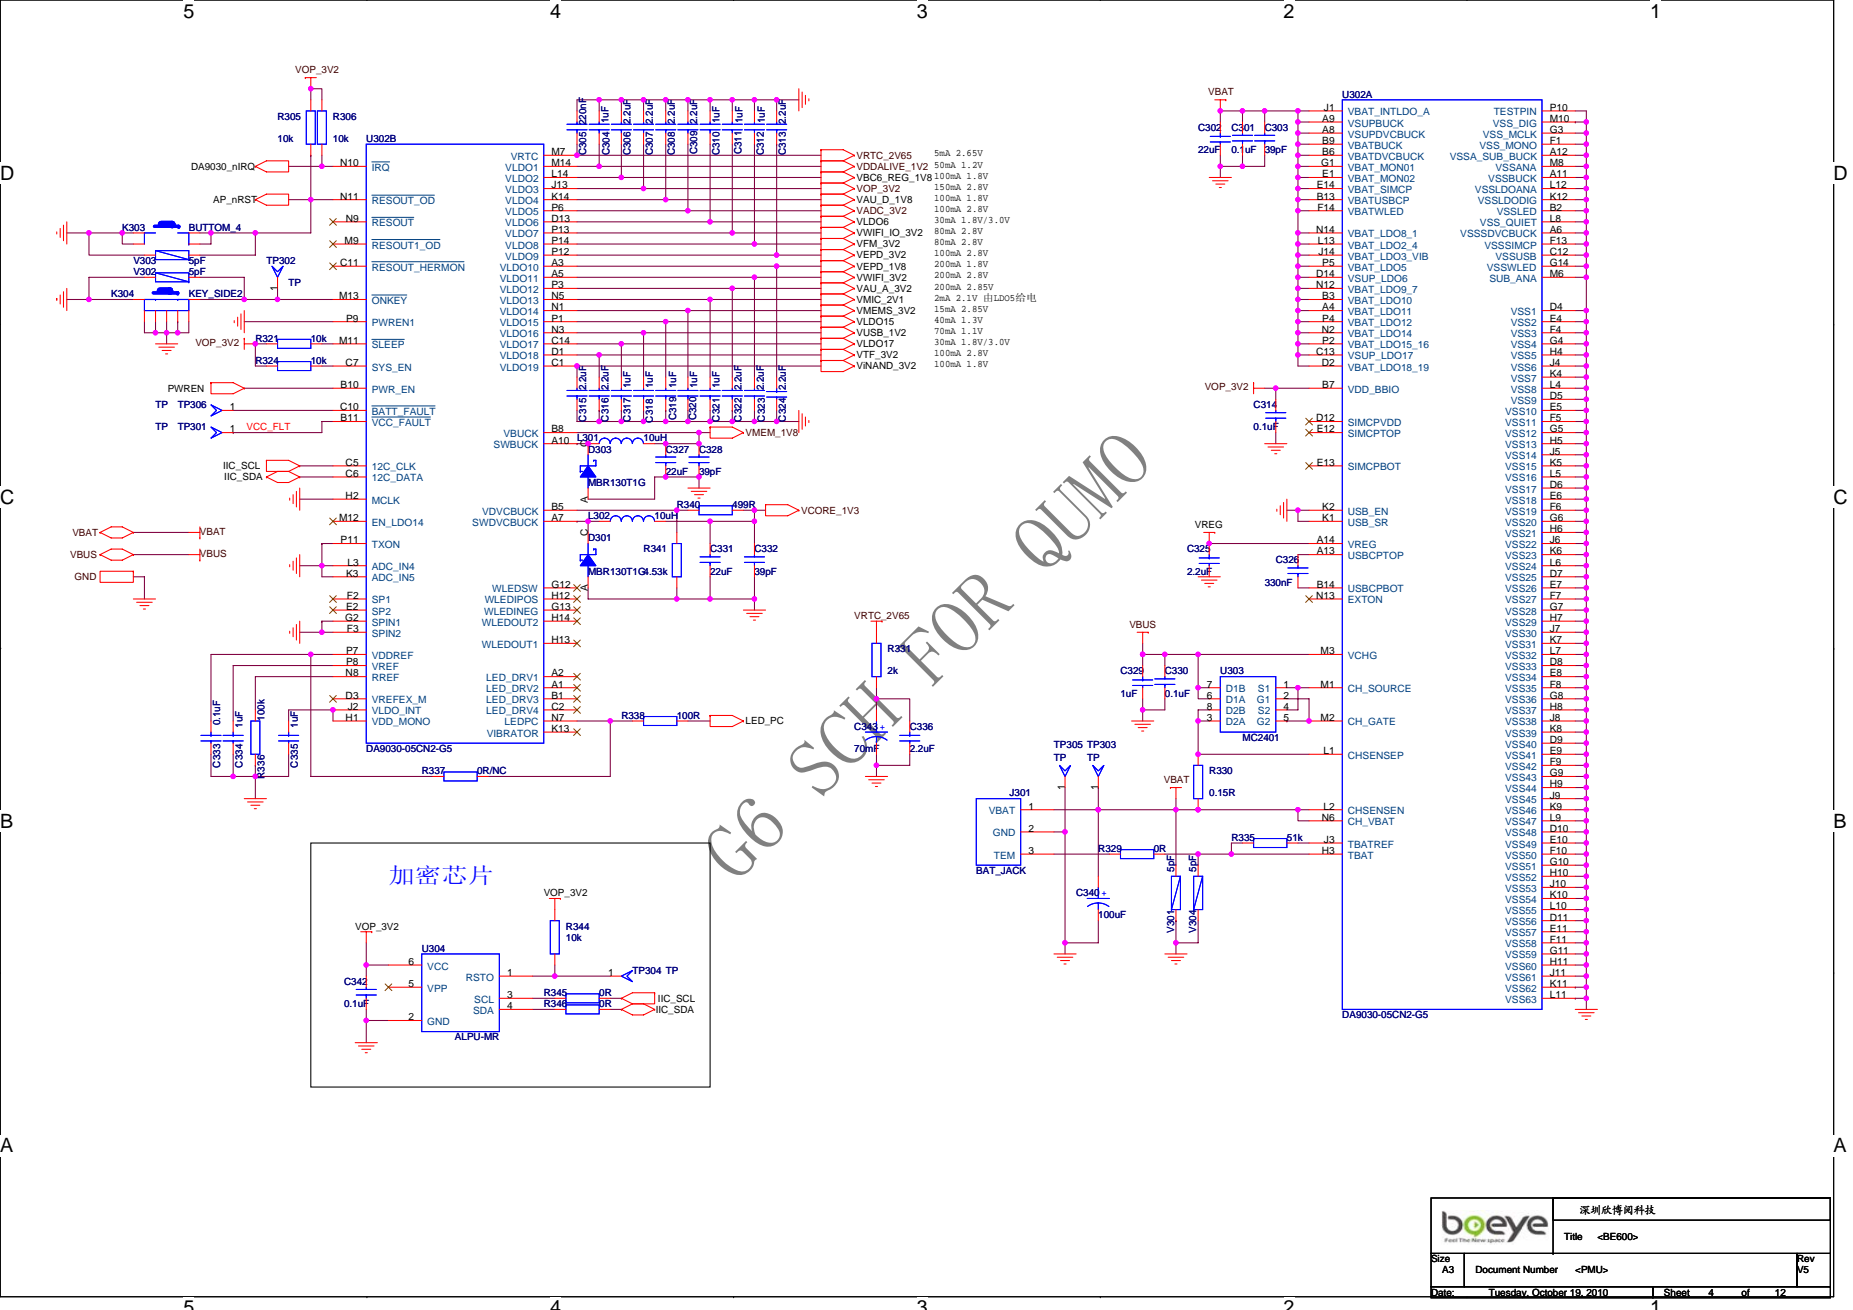
[picture p36: page 3]

<PMU> <PMU> <PMU> | V5 V5 V5

Tuesday, October 19, 2010 Tuesday, October 19, 2010 Tuesday, October 19, 2010 | 4 4 4 12 12 12

D | D

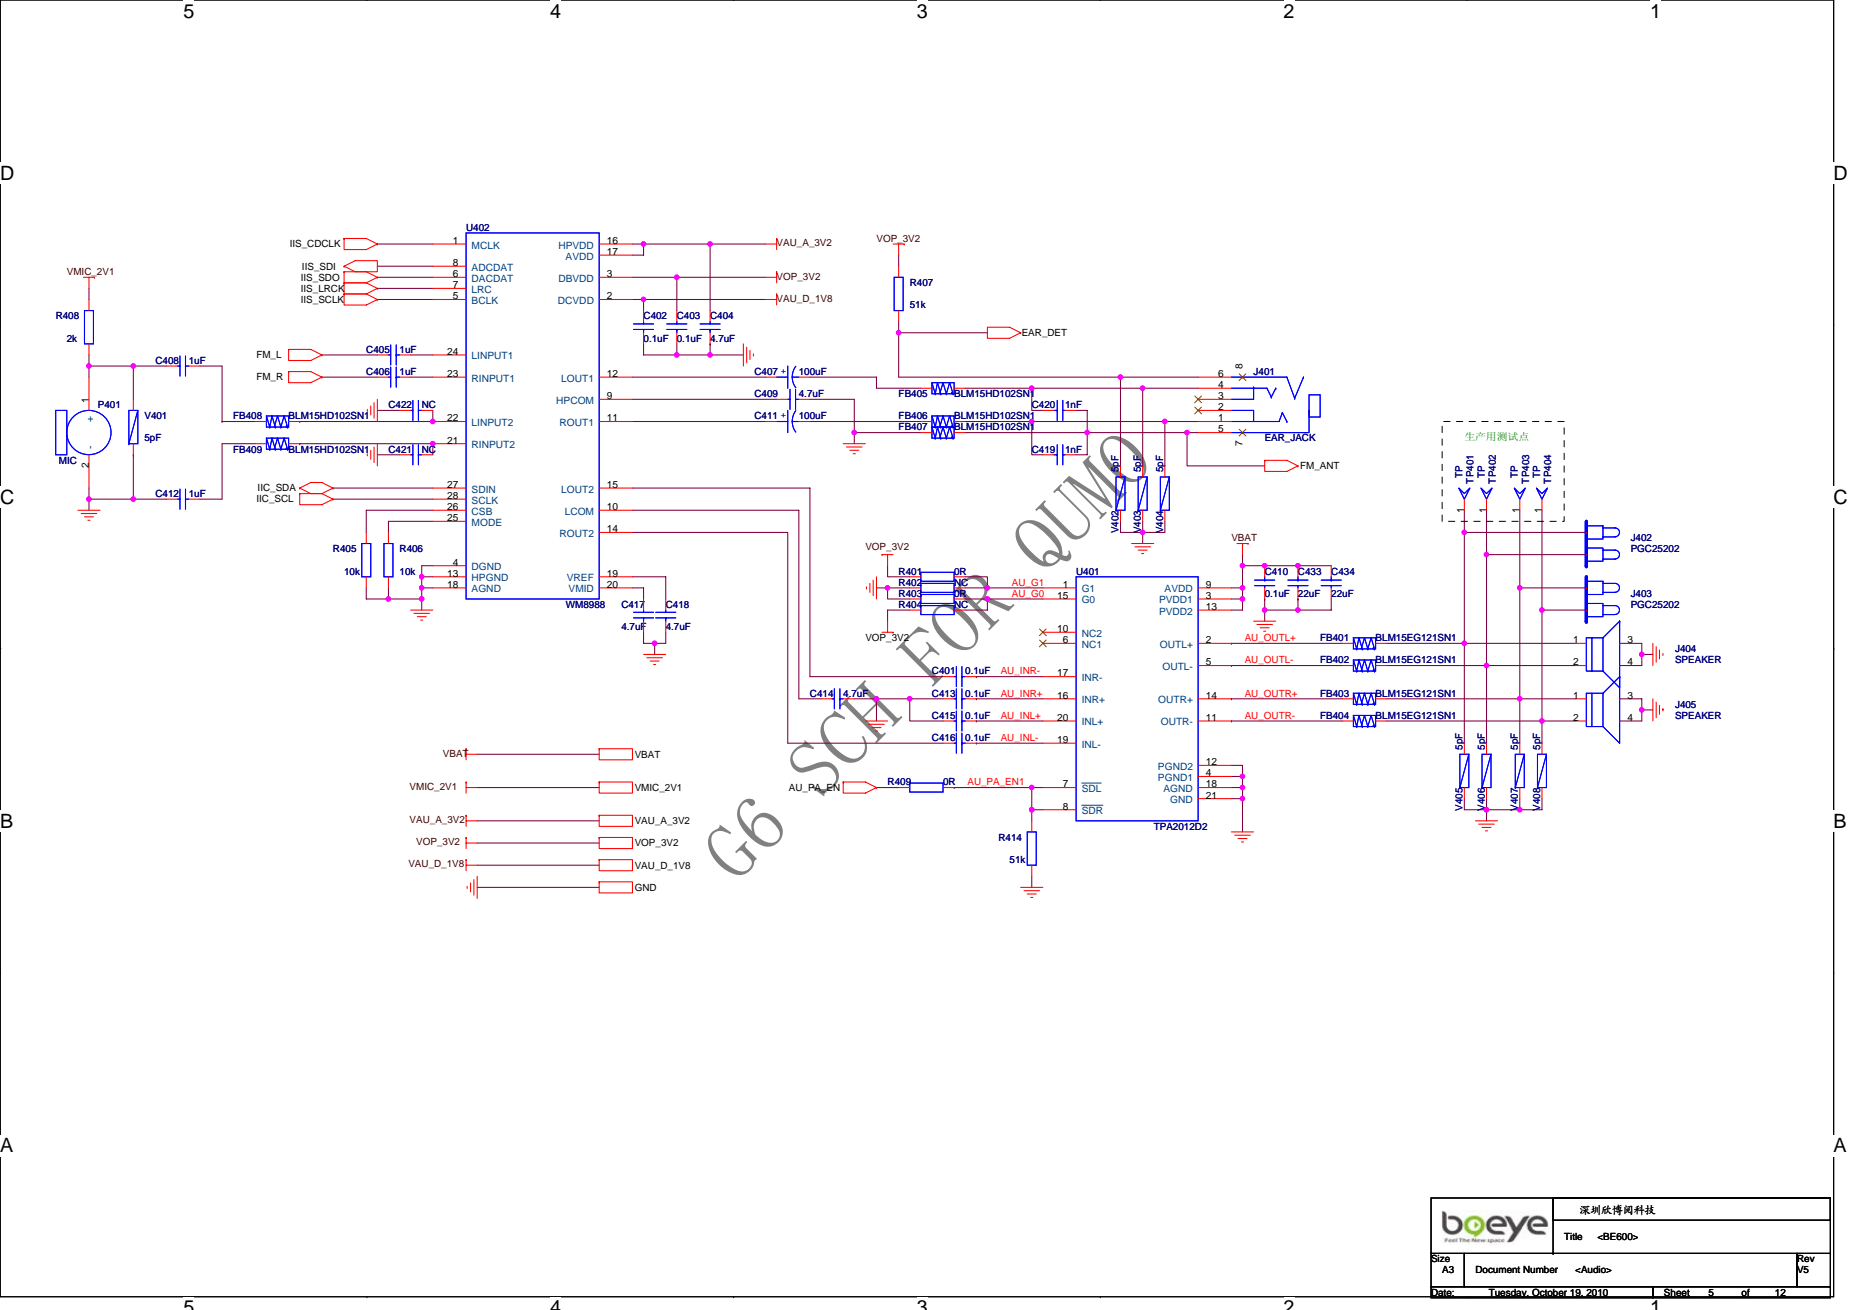
[picture p37: page 4]

INR- 17 | | | | 2

C415 | AU_INL- AU_INR+ AU_INL+ 0.1uF | INL+ 20 | | 2

INR+ 16

<Audio> <Audio> <Audio> | V5 V5 V5

Tuesday, October 19, 2010 Tuesday, October 19, 2010 Tuesday, October 19, 2010 | 5 5 5 12 12 12

D | D

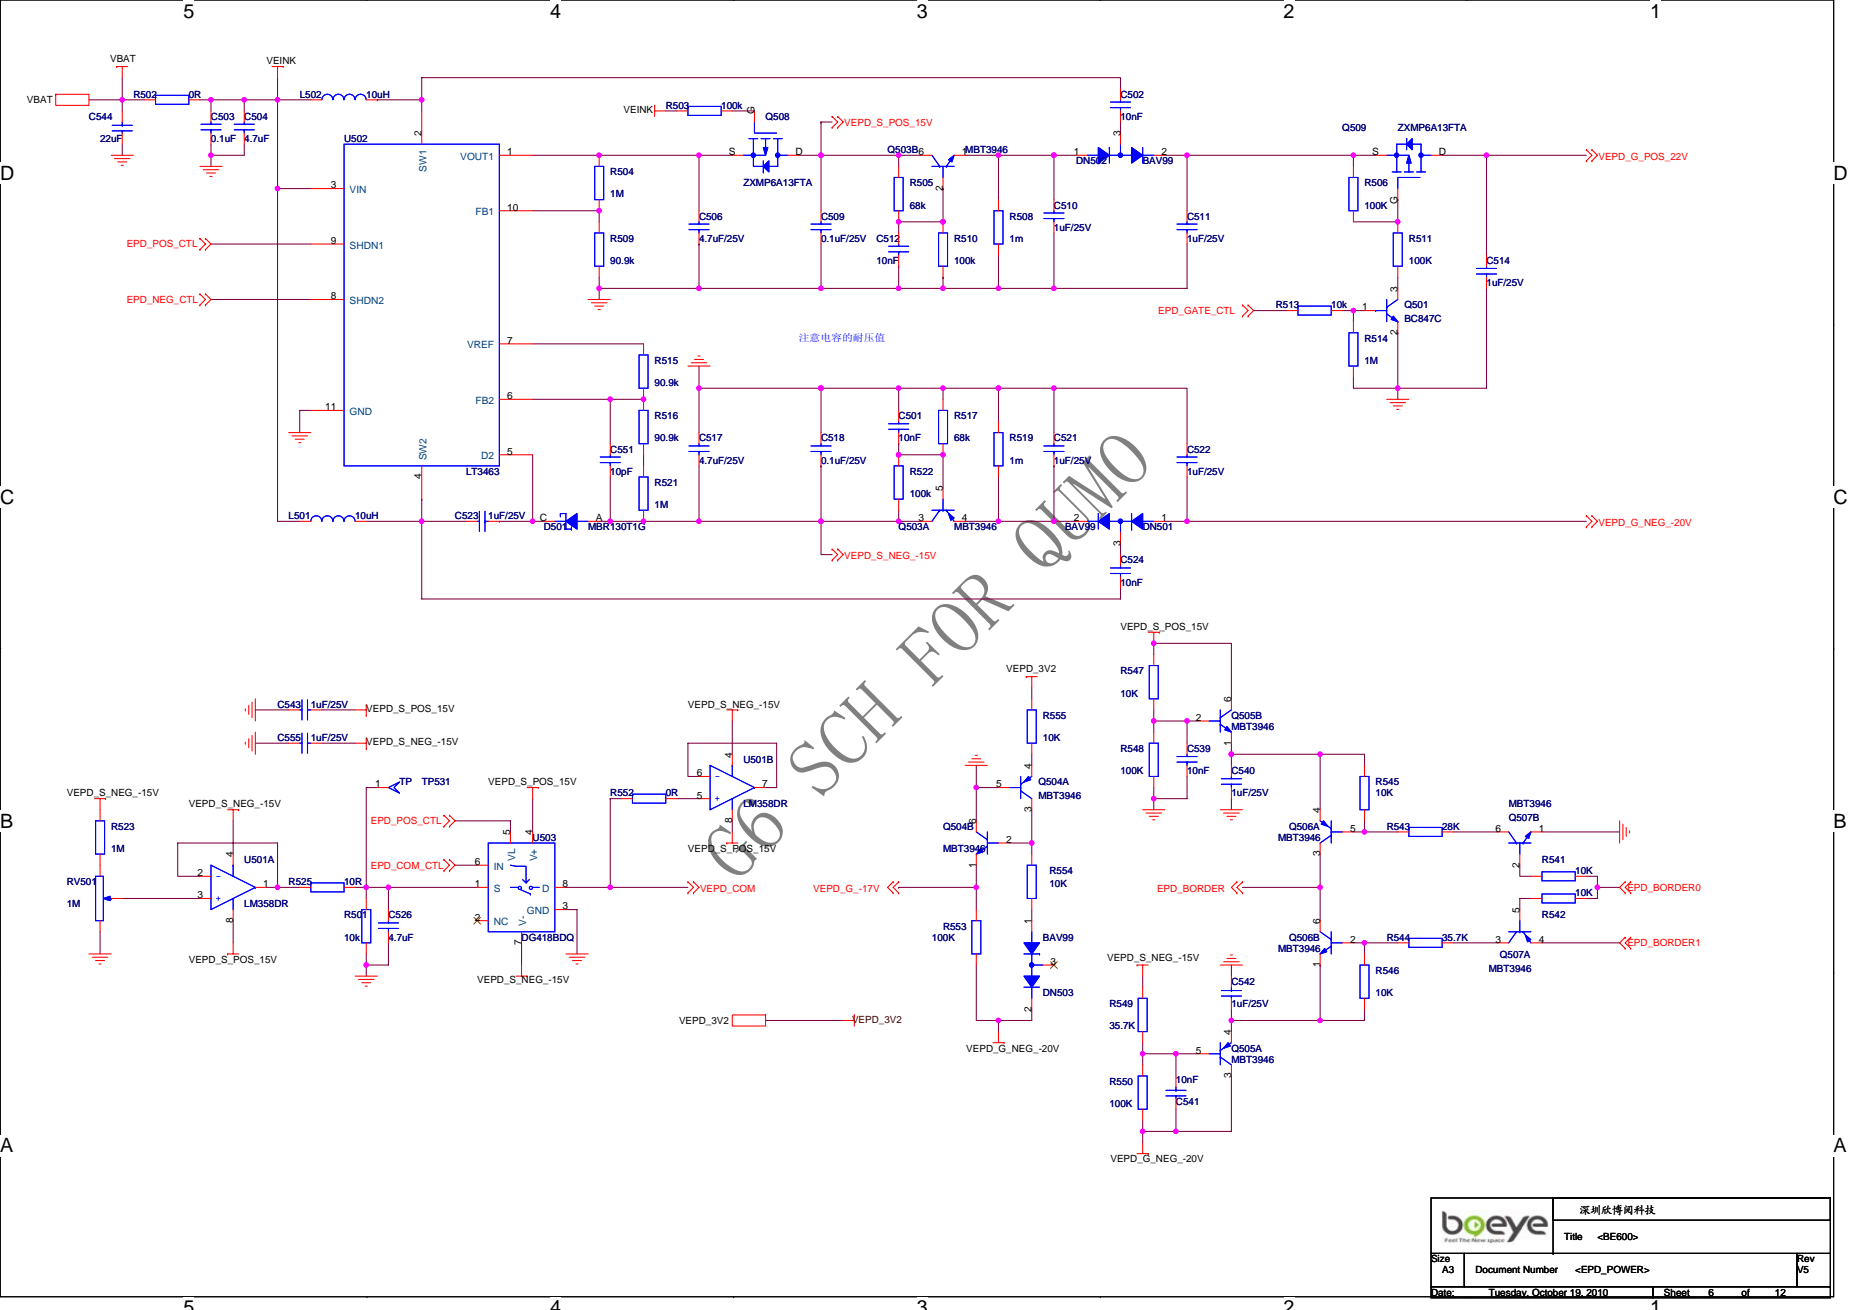
[picture p38: page 5]

<EPD_POWER> <EPD_POWER> <EPD_POWER> | V5 V5 V5

Tuesday, October 19, 2010 Tuesday, October 19, 2010 Tuesday, October 19, 2010 | 6 6 6 12 12 12

D

D

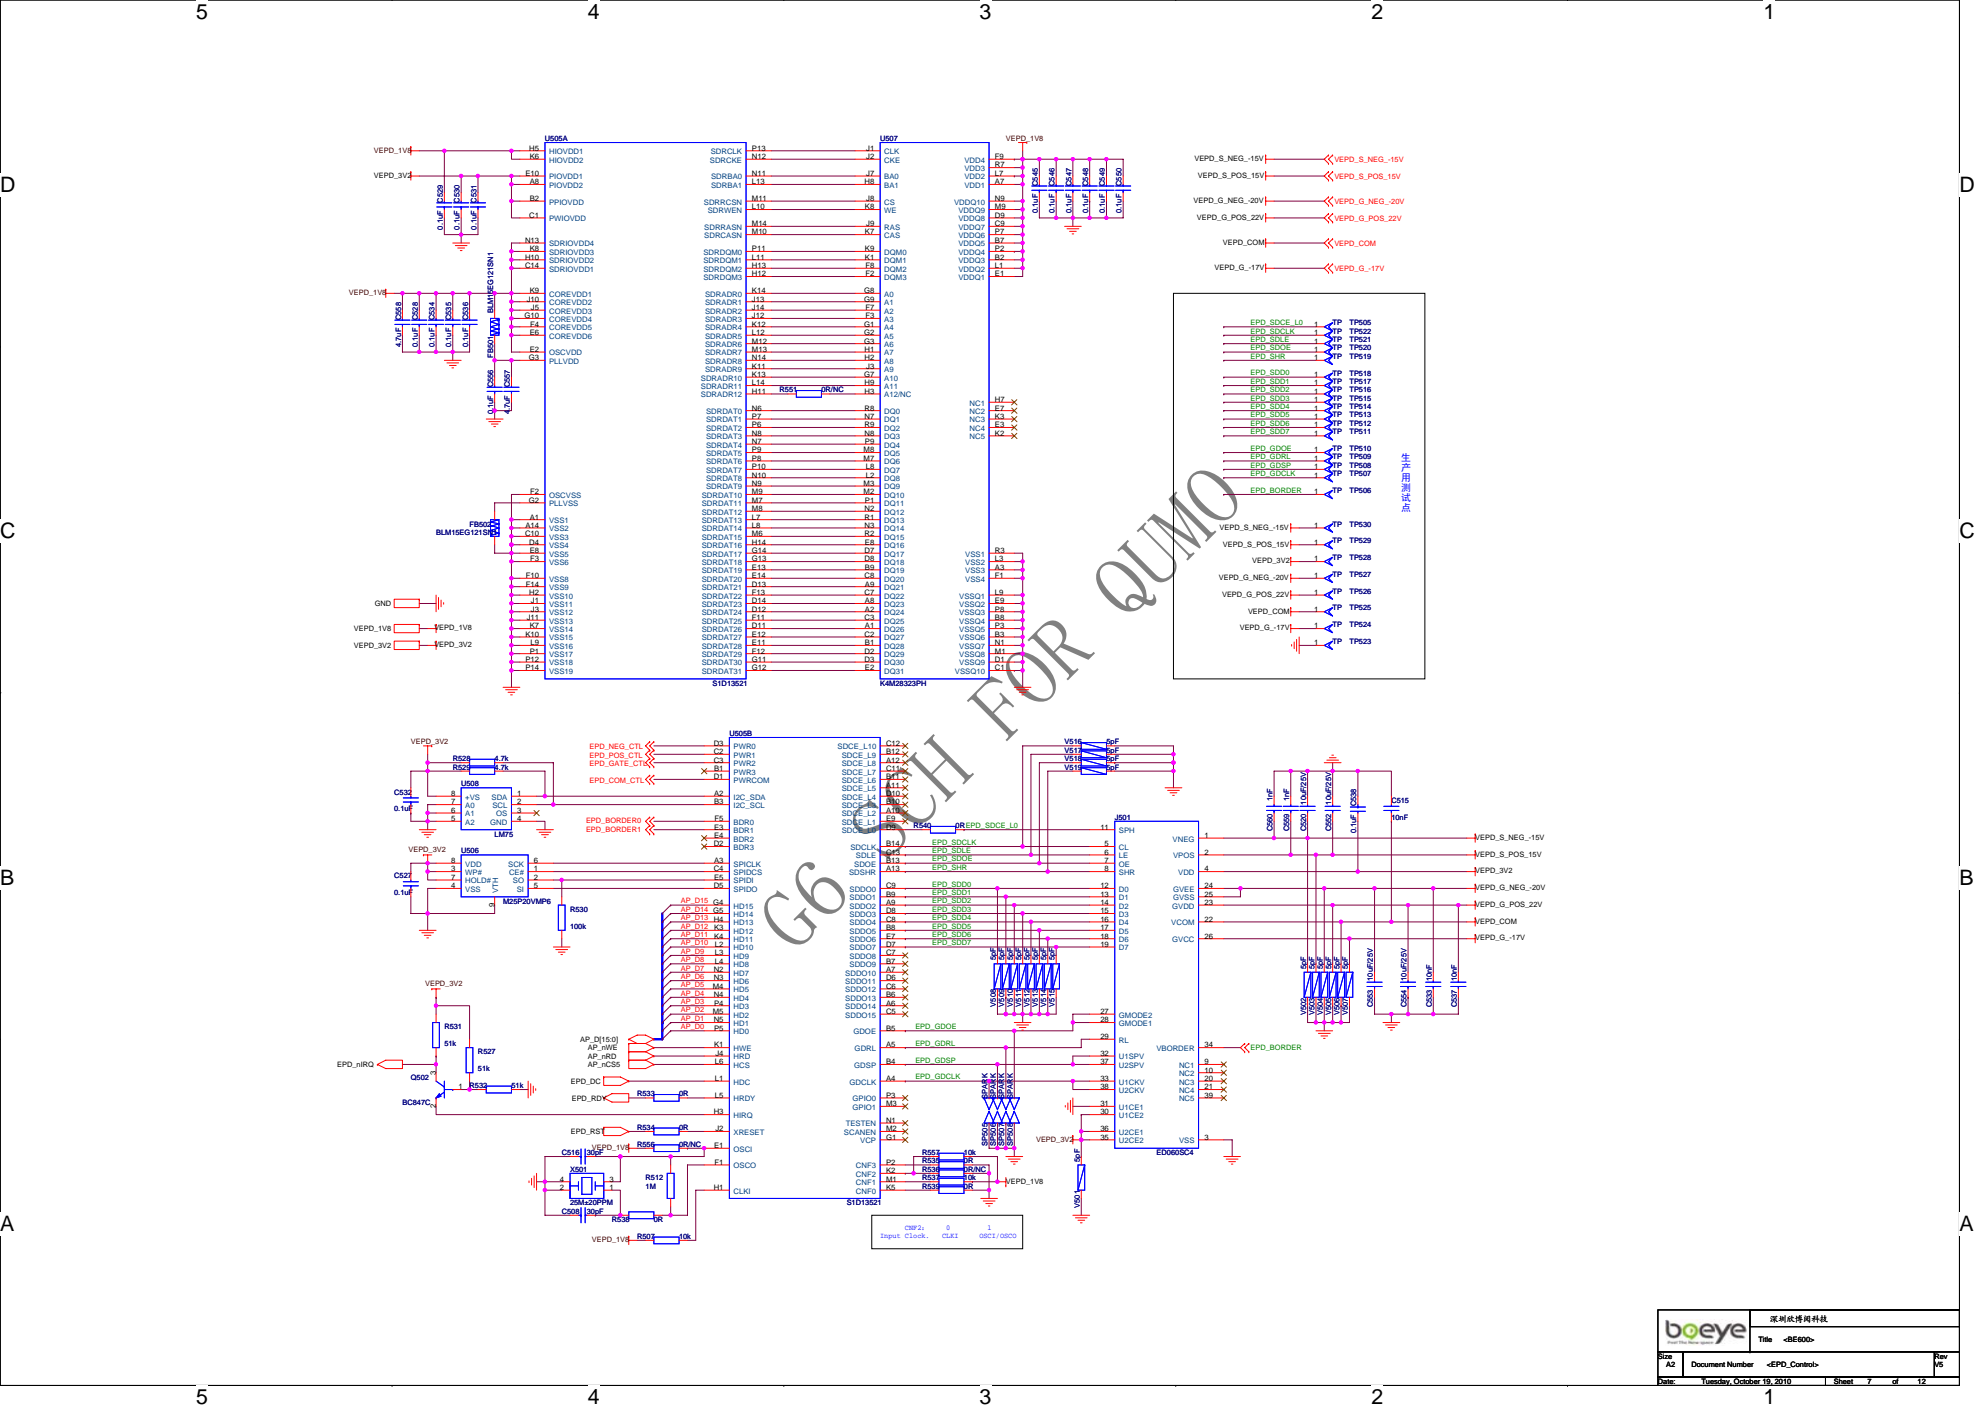
[picture p39: page 6]

HOLD# 7 | | SPIDI E5 | EPD_SDD0 | D0 12

AP_D15 | EPD_SDD1 | | D1 13

EPD_SDD2 | | D2 14

EPD_GDCLK | U1CKV 33

U2CKV 38

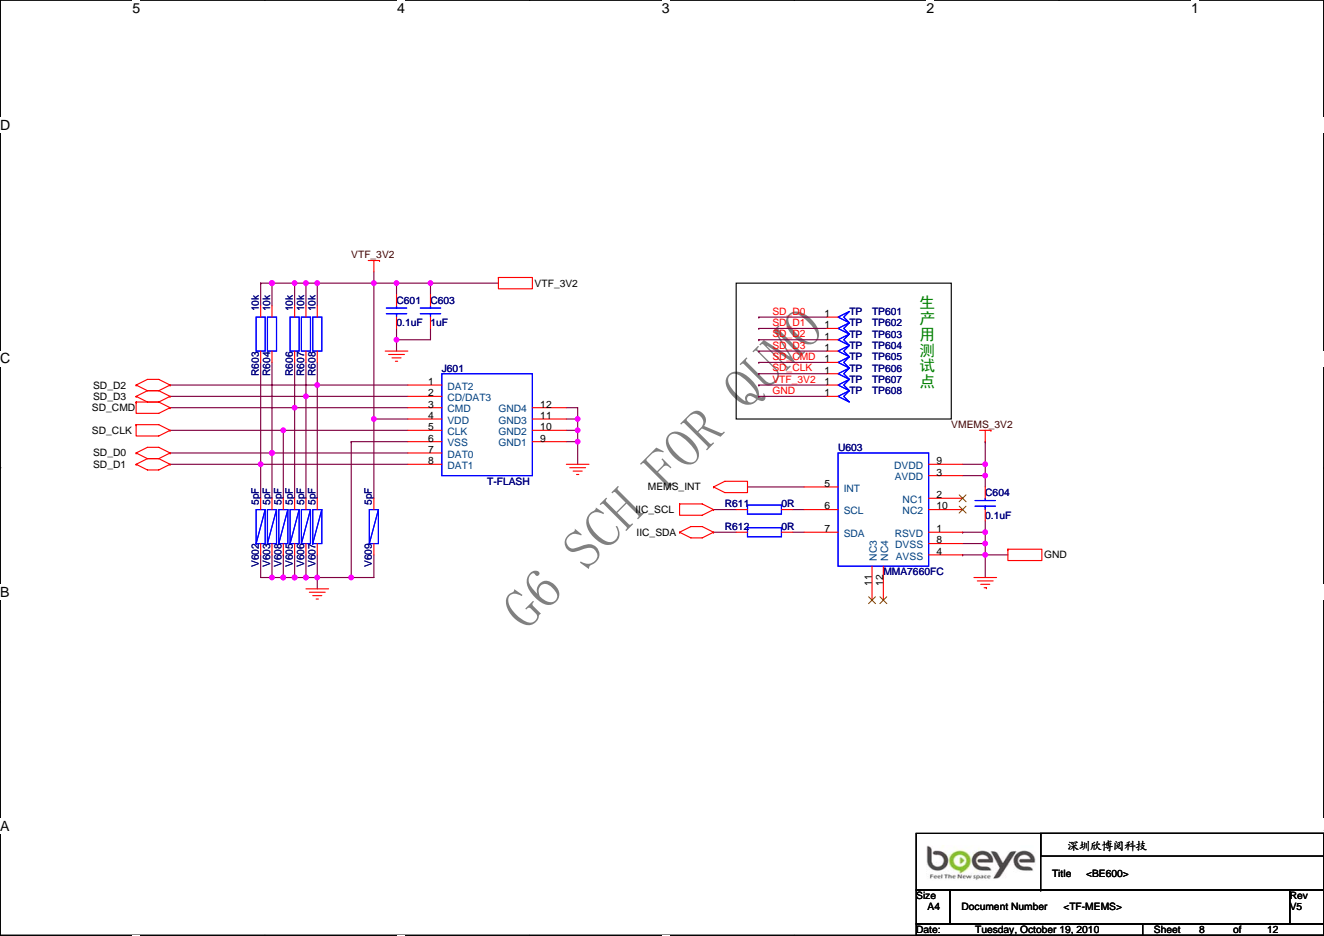
[picture p40: page 7]

G6 SCH FOR QUMO 5 4 3 2 1 DC

<TF-MEMS> <TF-MEMS> <TF-MEMS> | V5 V5 V5

Tuesday, October 19, 2010 Tuesday, October 19, 2010 Tuesday, October 19, 2010 | 8 8 8 12 12 12

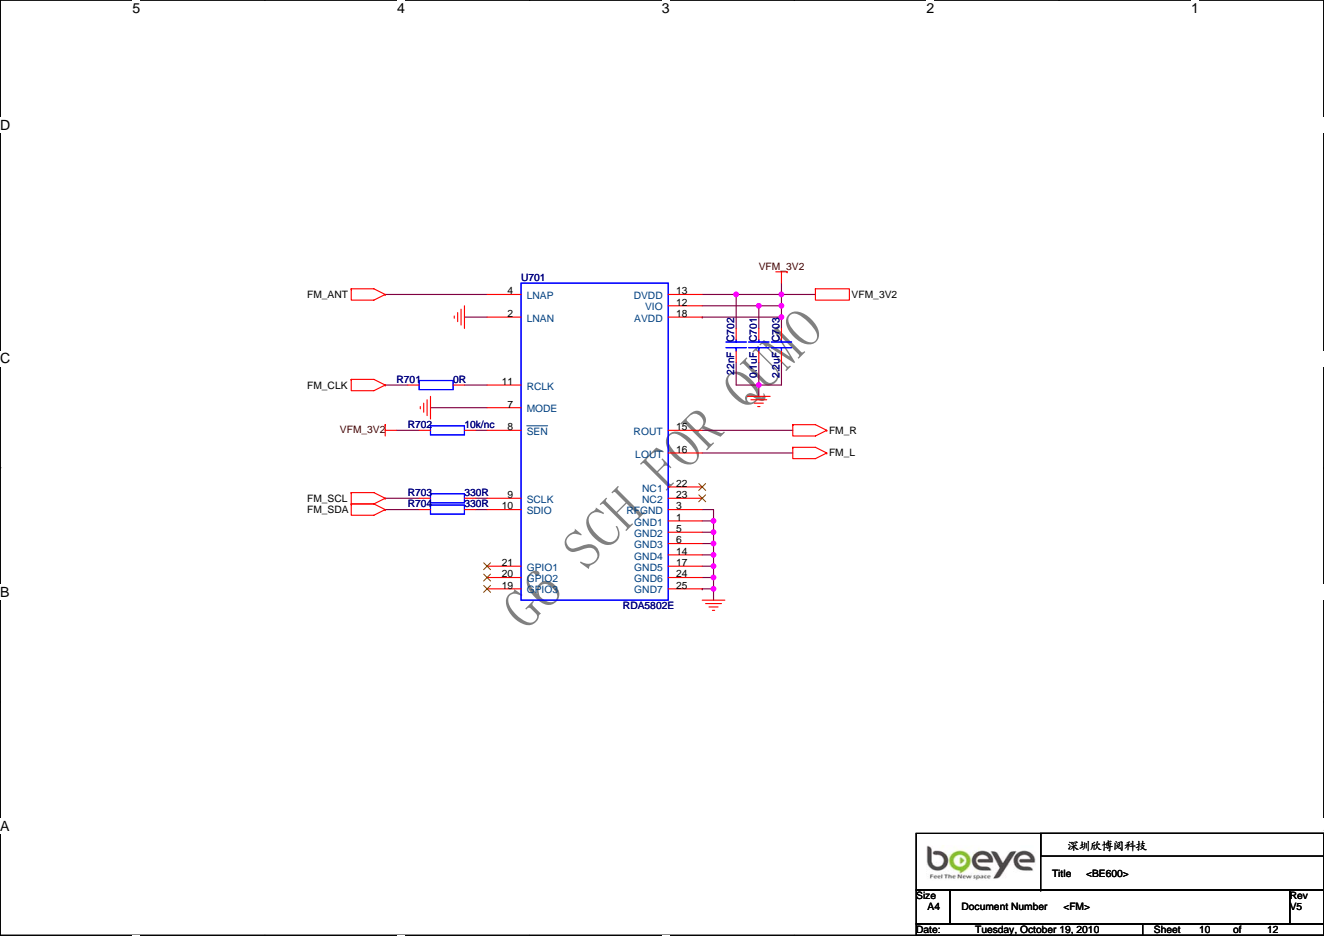
[picture p41: page 8]

G6 SCH FOR QUMO 5 4 3 2 1 DC

Tuesday, October 19, 2010 Tuesday, October 19, 2010 Tuesday, October 19, 2010 | 10 10 10 12 12 12

D | D

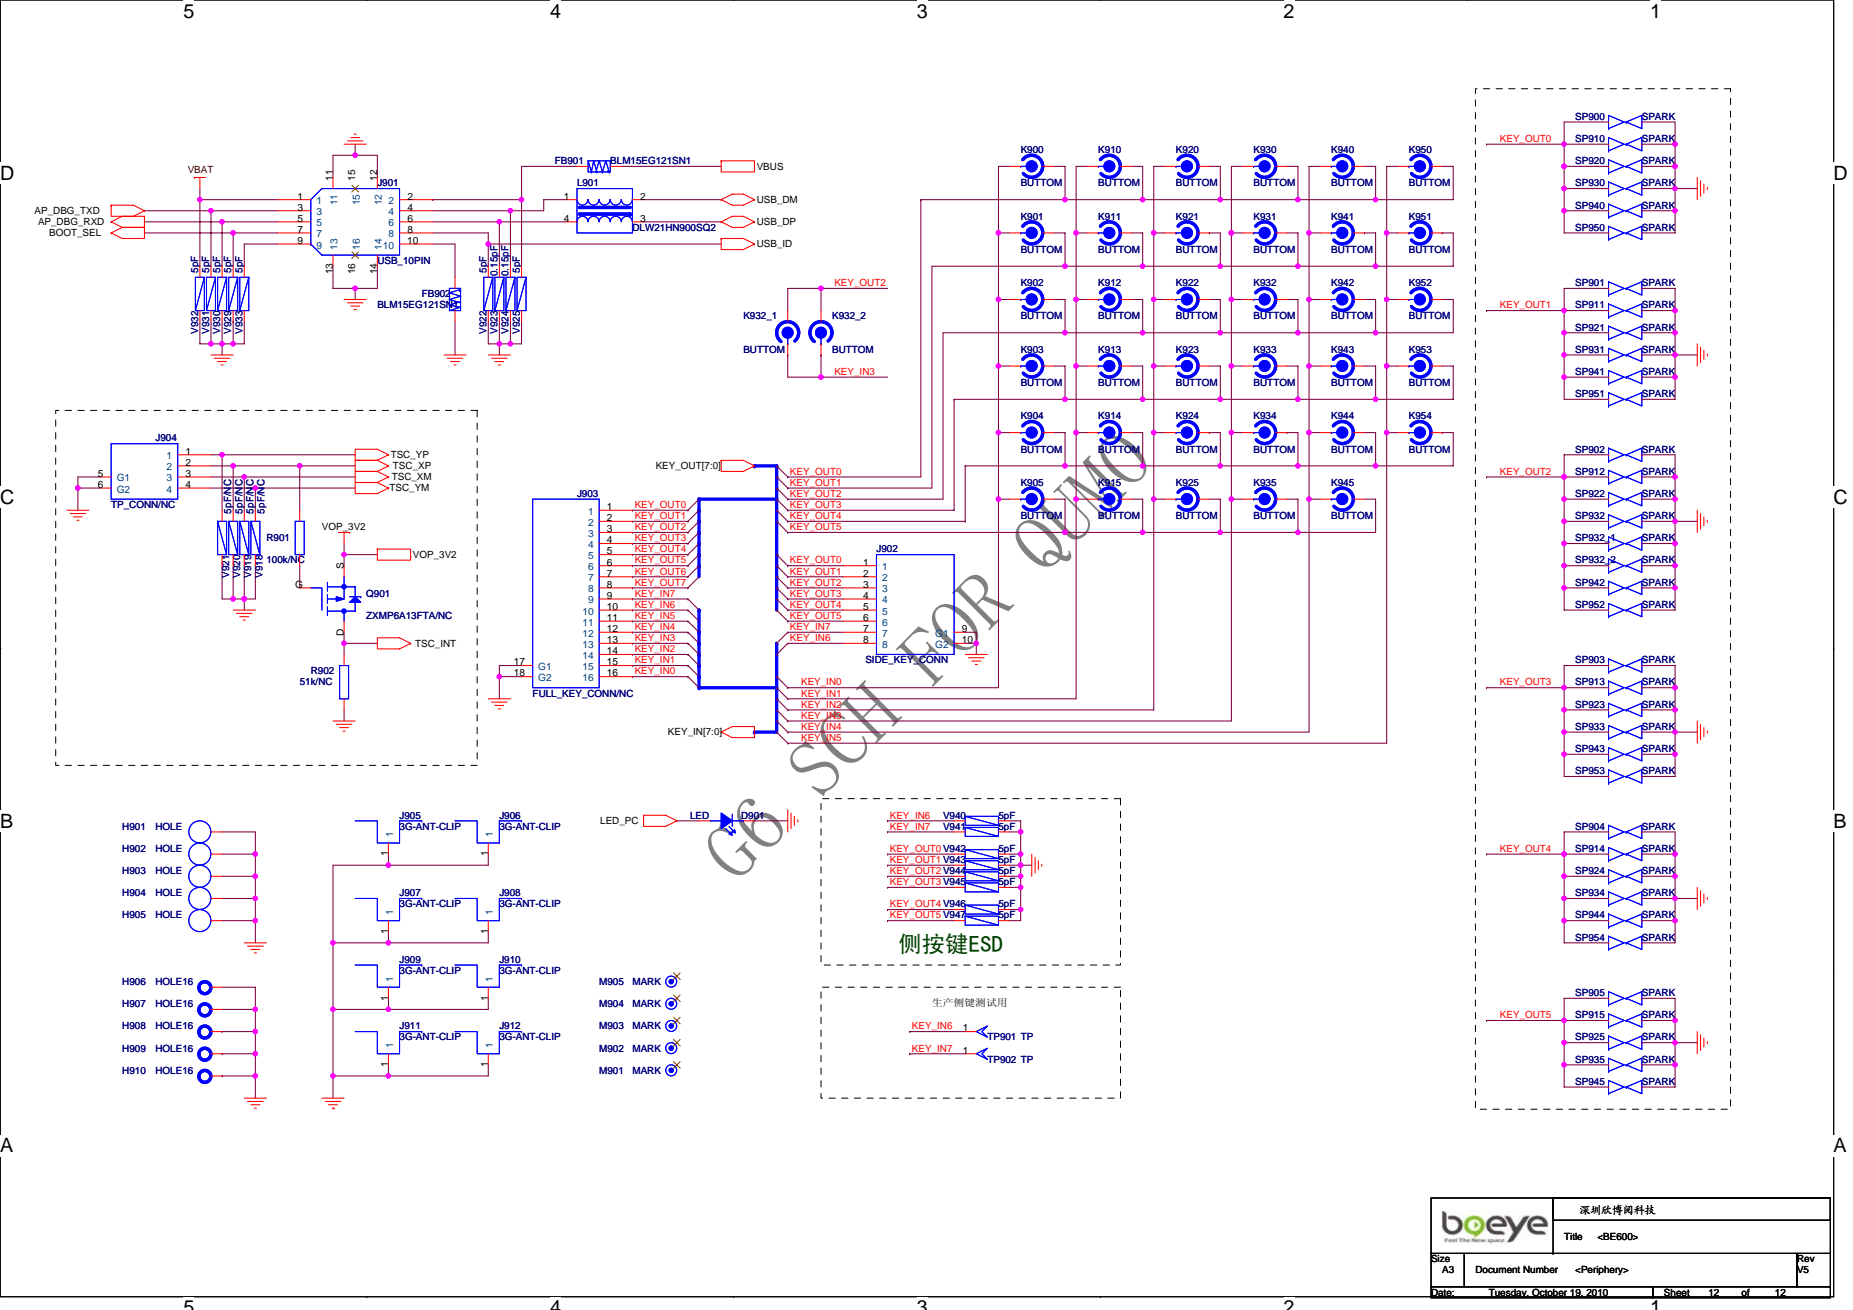
[picture p42: page 9]

<Periphery> <Periphery> <Periphery> | V5 V5 V5

Tuesday, October 19, 2010 Tuesday, October 19, 2010 Tuesday, October 19, 2010 | 12 12 12

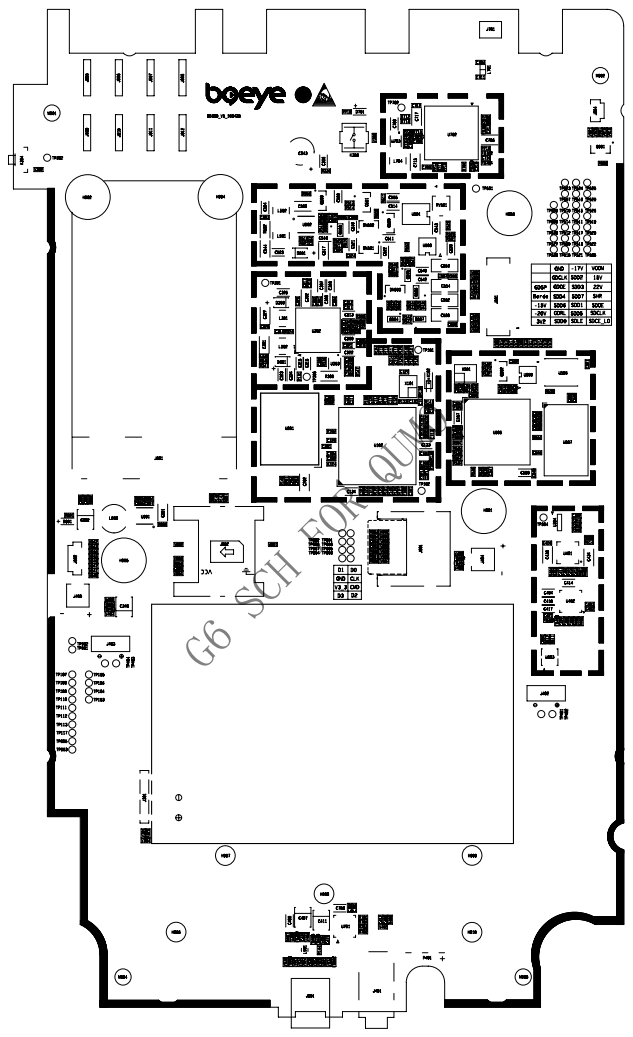
[picture p43: page 10]

G6 SCH FOR QUMO

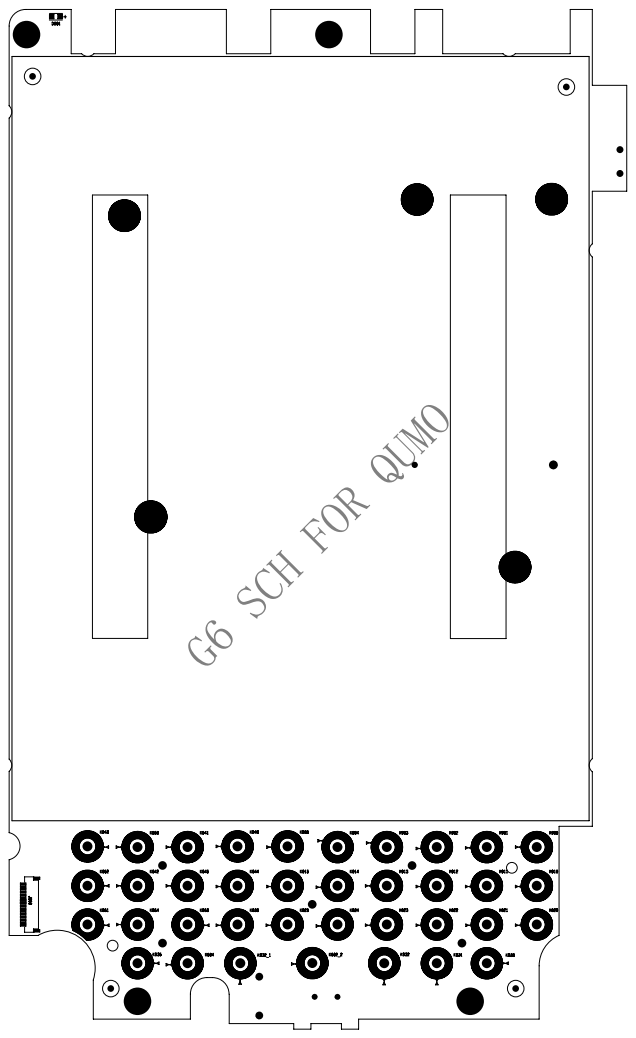
[picture p44: page 11]

G6 SCH FOR QUMO
