waterbury/e-ink-driver/prior-art/e-ink/EAGLE/e-ink-display-v020/e-ink-display-v020-sch.pdf

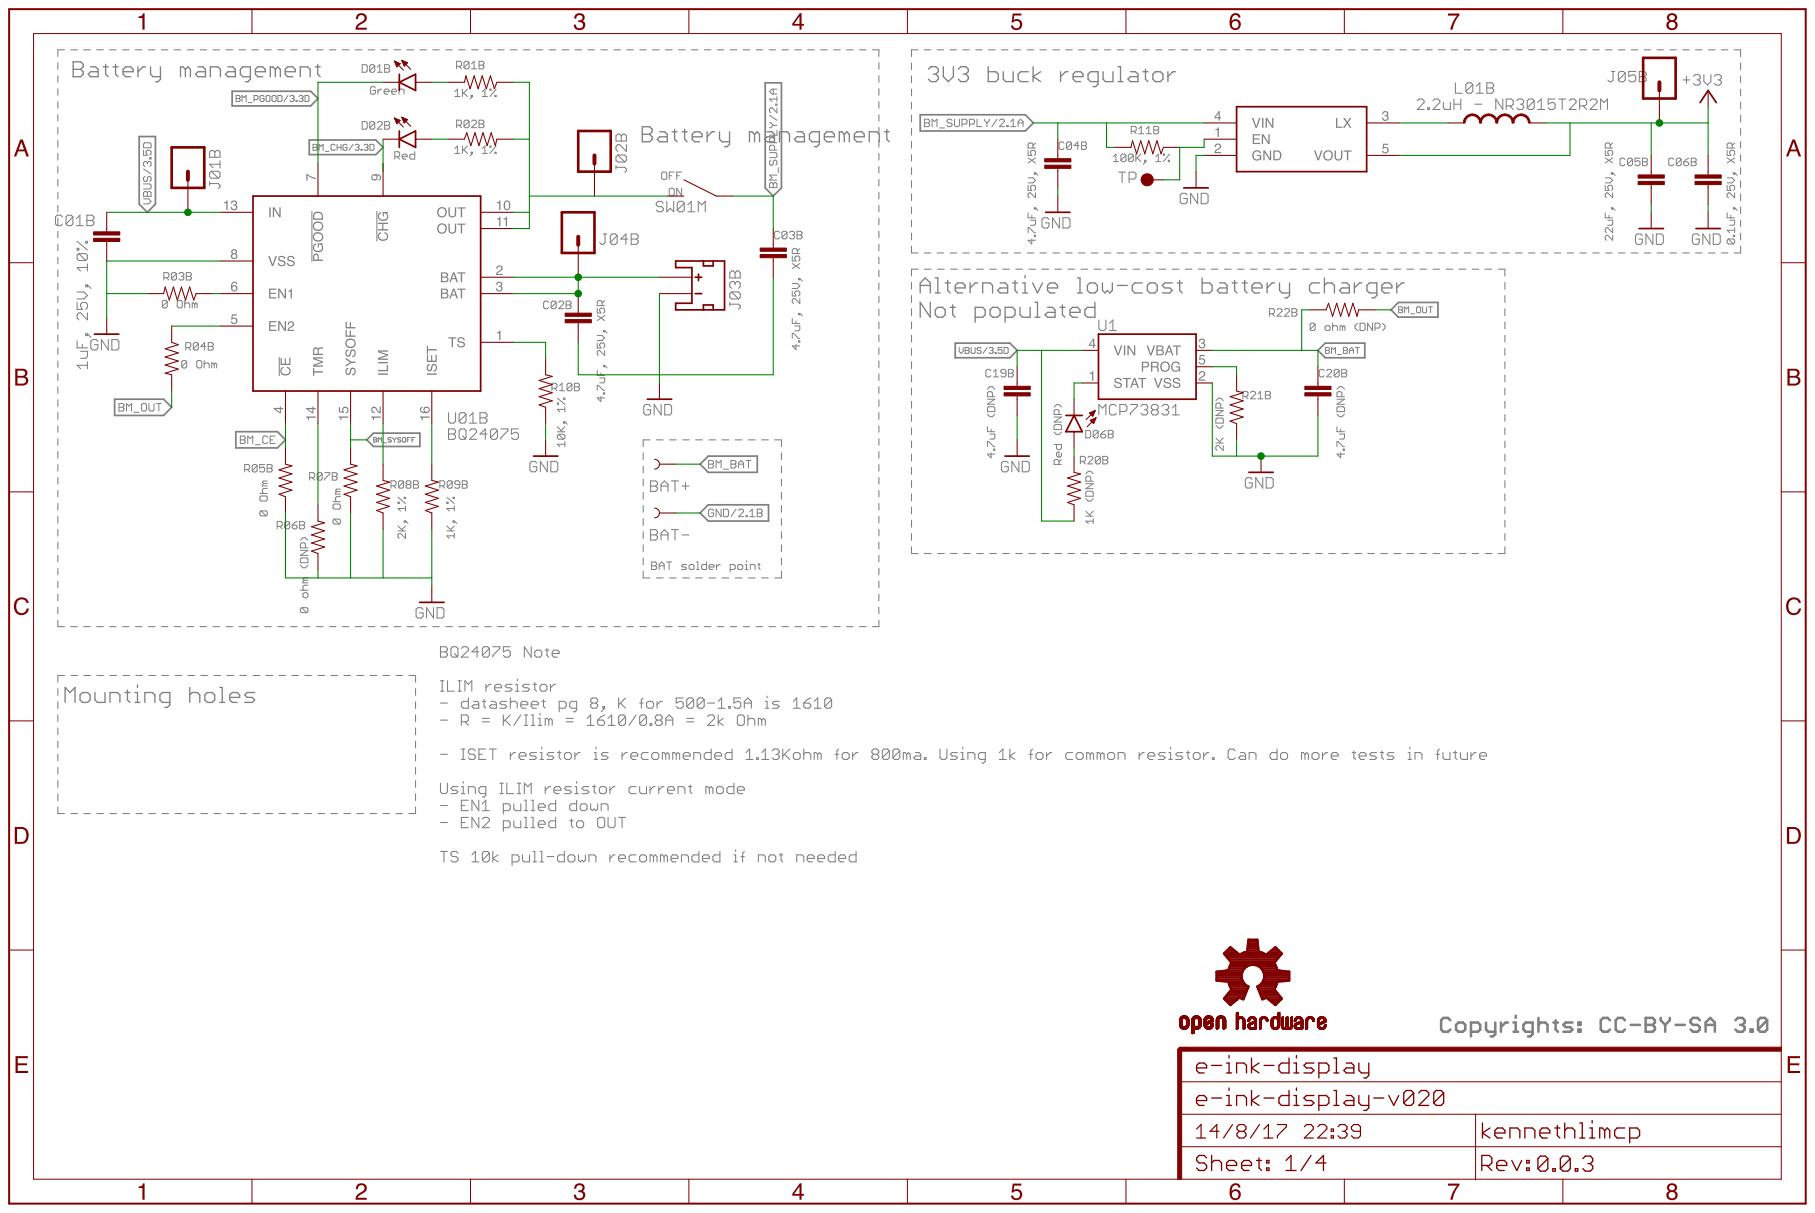
[picture p45: page 1]

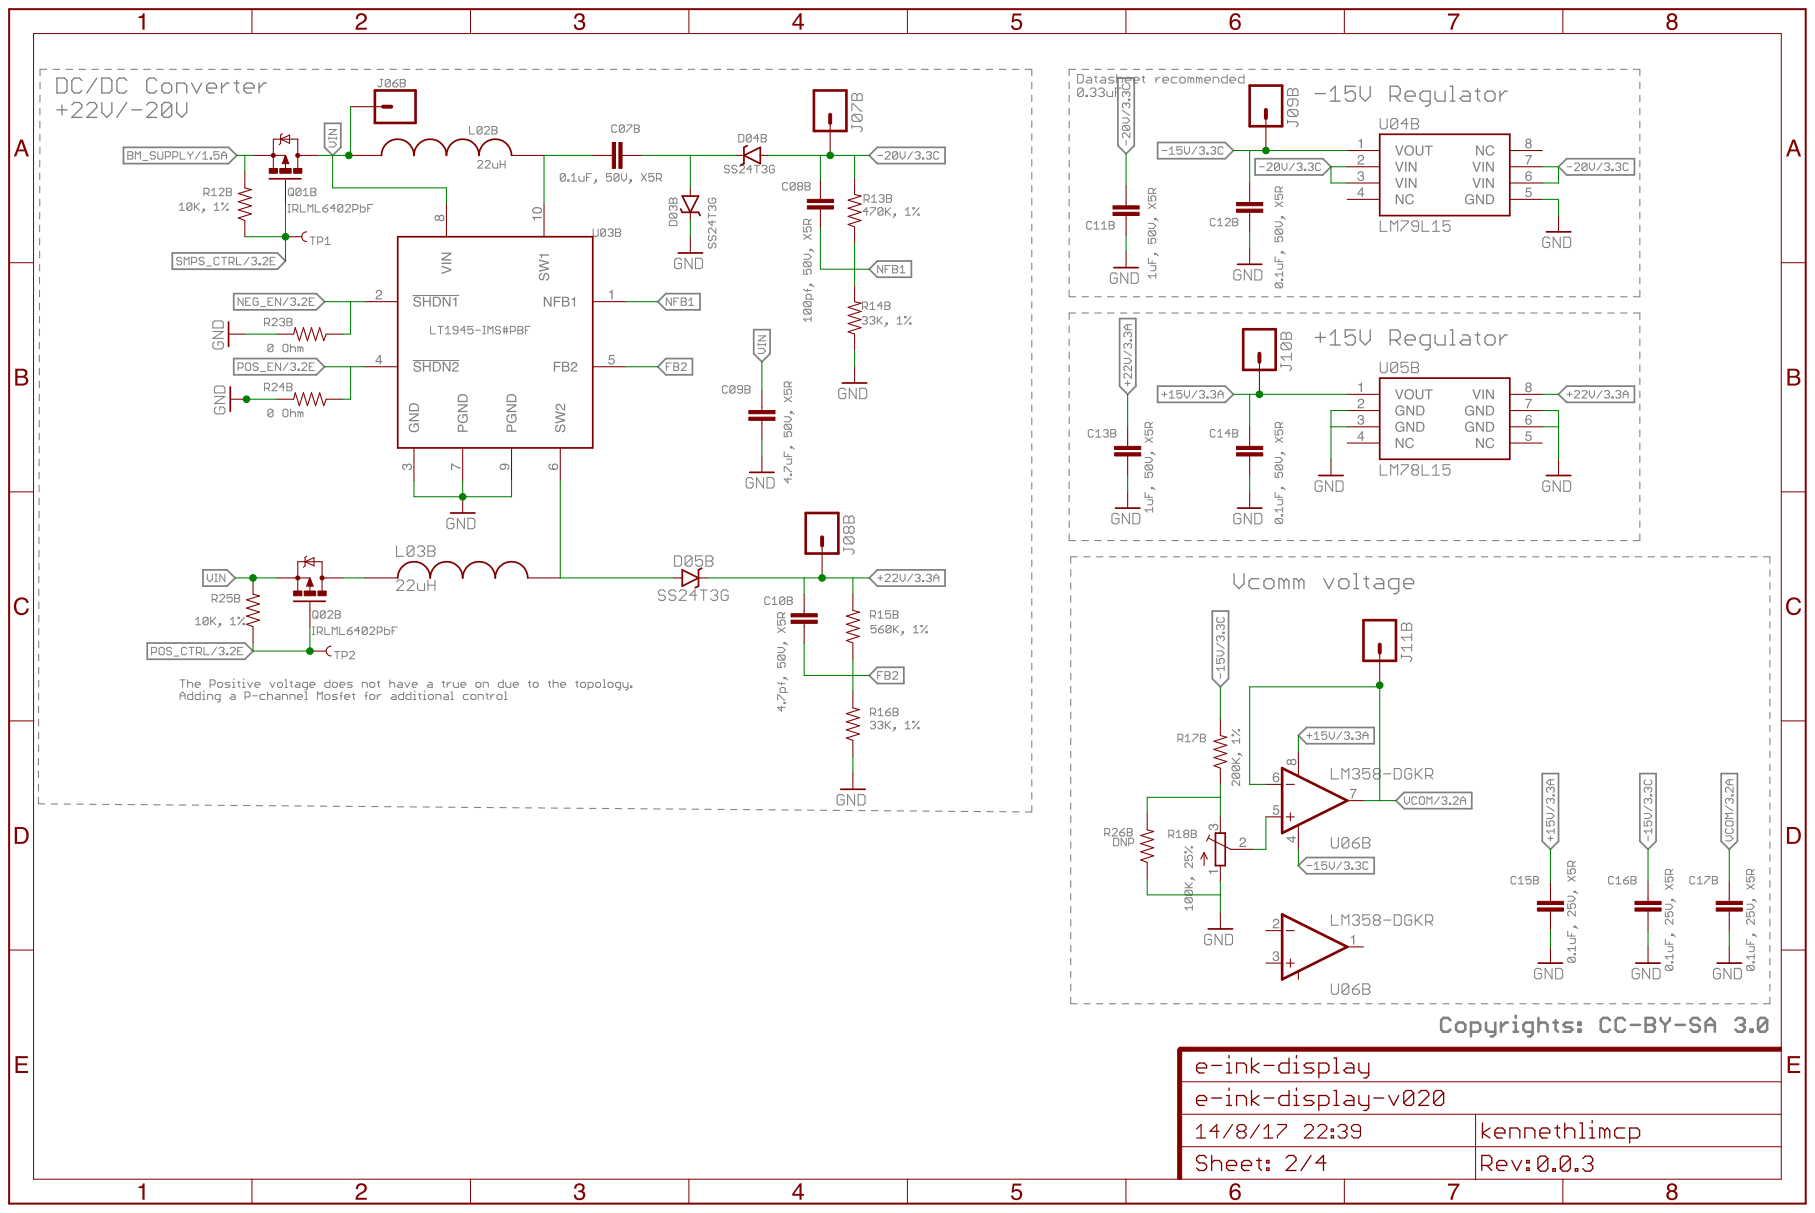
[picture p46: page 2]

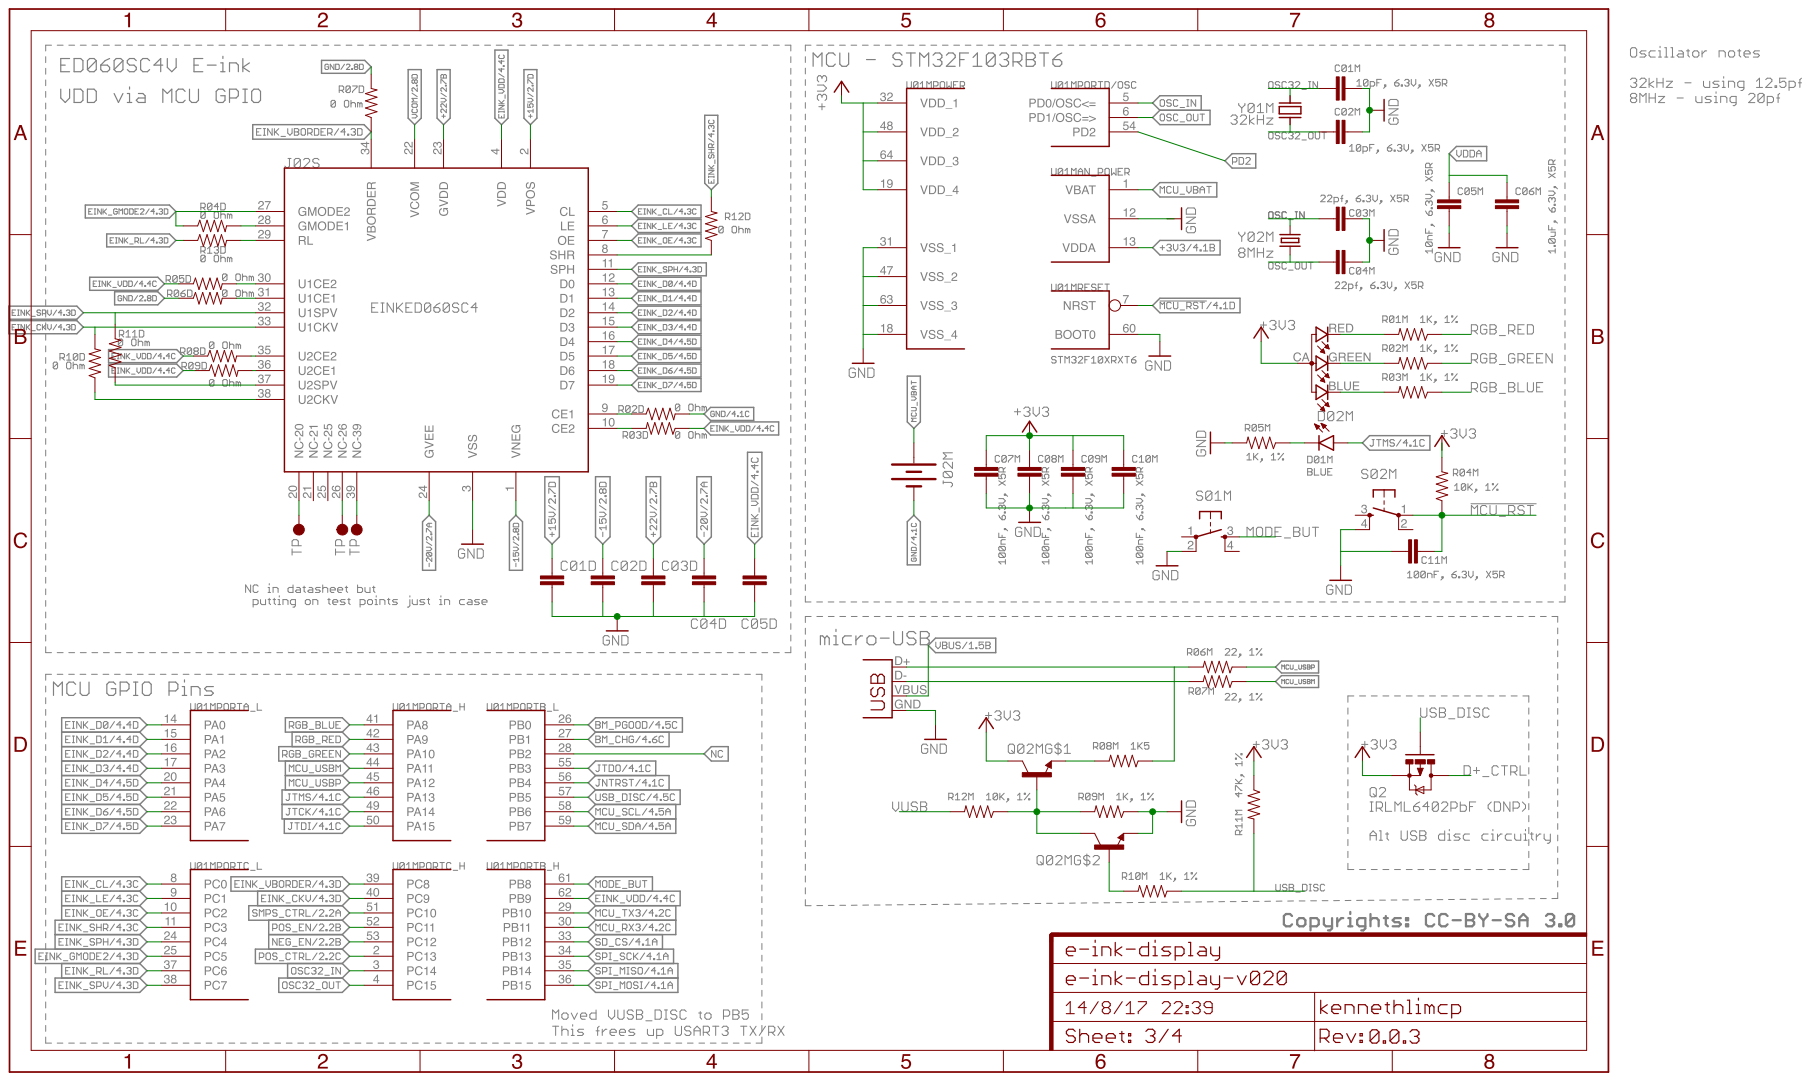
[picture p47: page 3]

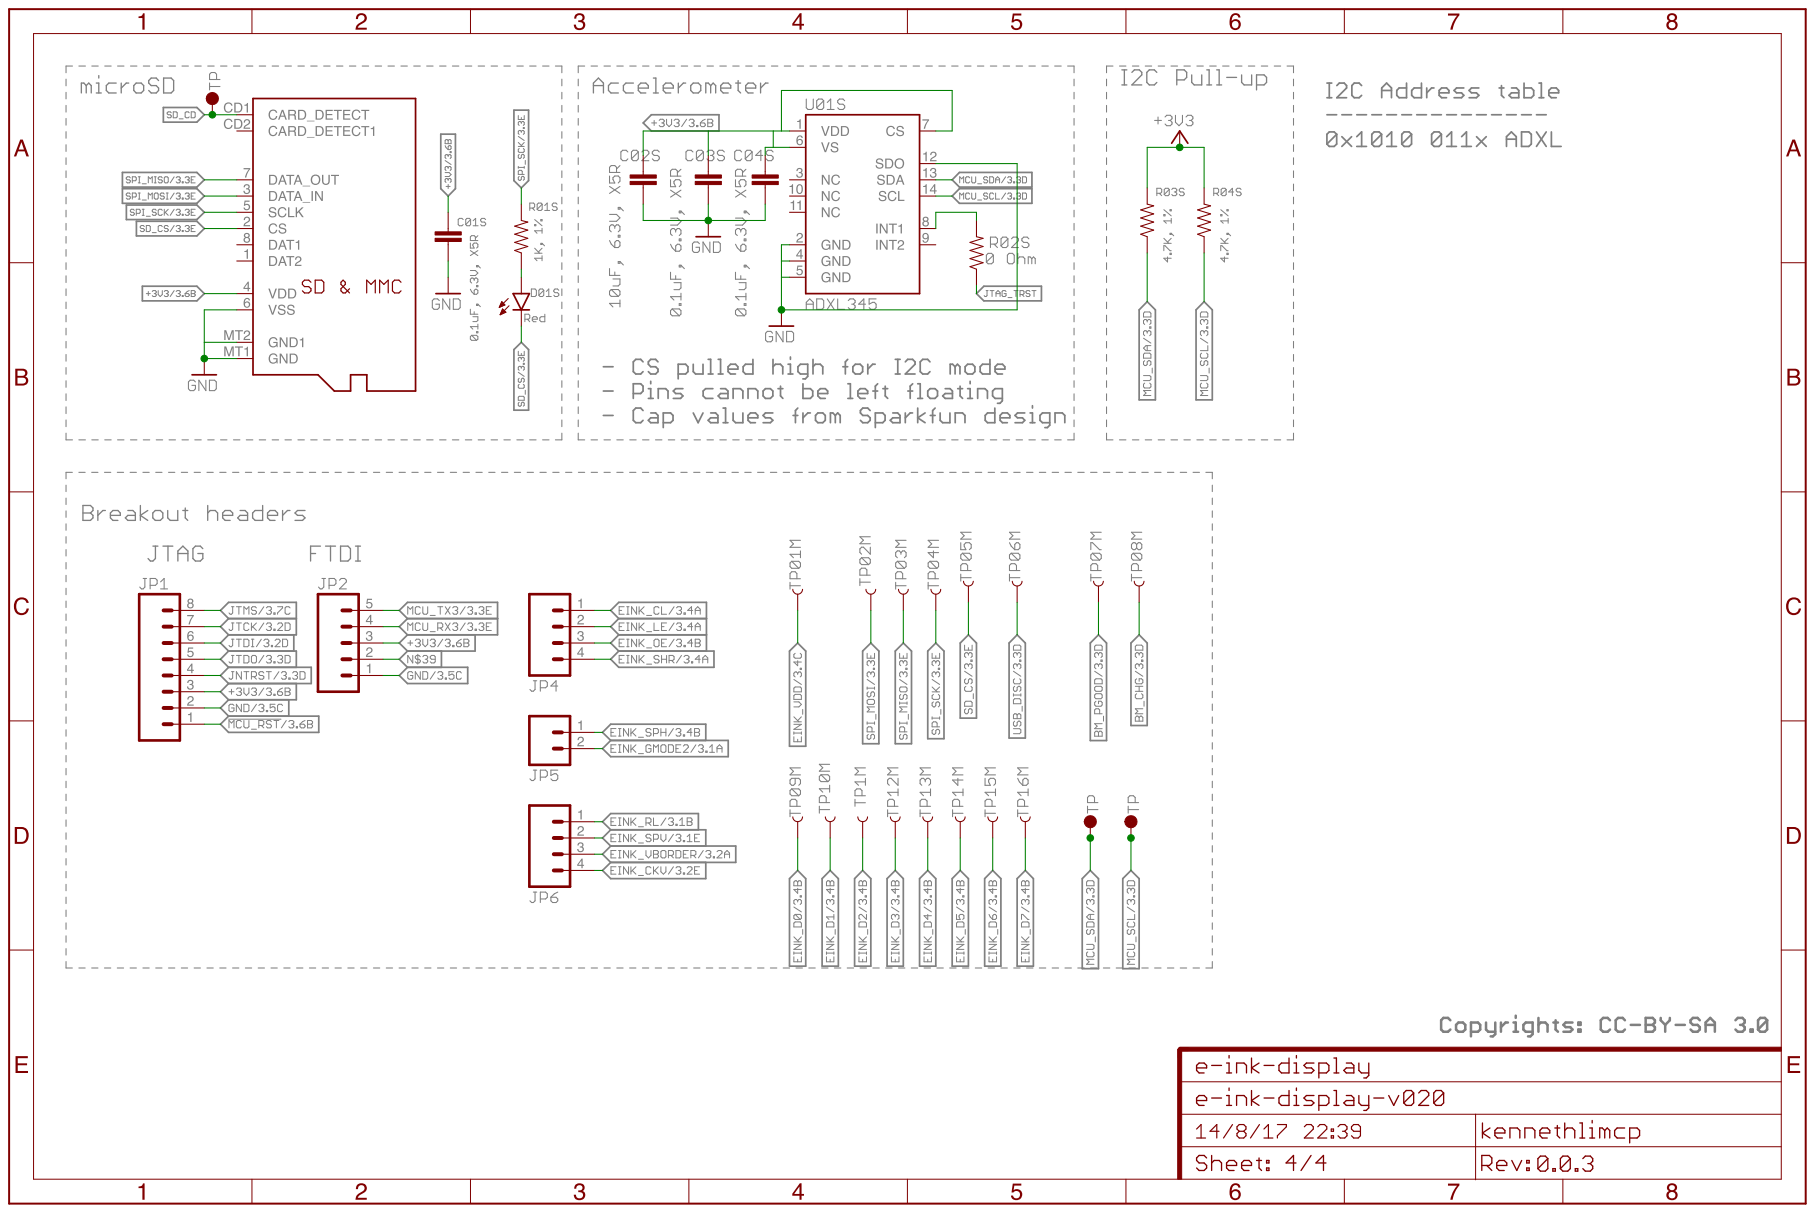
[picture p48: page 4]
