waterbury/e-ink-driver/prior-art/e-ink/LTSpice/LT1945.asc

C1: cap; 1µ
C2: cap; 1µ
C3: cap; .1µ
D1: schottky; 1N5819
D2: schottky; MBRS360
D3: schottky; 1N5819
L1: ind; 10µ; Rpar=10K
L2: ind; 10µ; Rpar=2K
R1: RES; 365K
R2: res; 24.9K
R3: res; 1Meg
R4: res; 115K
Rload1: res; 2K
Rload2: res; 1K
U1: LT1945
V1: VOLTAGE; 10
Named nets: 0, OUT1, OUT2, IN
.tran 1m startup
