waterbury/e-ink-driver/prior-art/e-ink/firmware/e-ink-tests-v002/tests/unit-test.h

#include "application.h"


#pragma once
/**
 * Copyright 2014  Matthew McGowan
 *
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
 * You should have received a copy of the GNU General Public License
 * along with this program. If not, see <http://www.gnu.org/licenses/>.
 */

/*
 This is modification of ArduinoUnit to compile on the spark. The required headers and cpp files have been combined into a single
 header.
*/


#define strcpy_P strcpy
#define strlcpy_P strncpy
#define sprintf_P sprintf
#define strcmp_P strcmp
#define memcpy_P memcpy
#define vsnprintf_P vsnprintf
#define PROGMEM
#define PSTR

enum RunnerState {
    INIT,
    WAITING,
    RUNNING,
    COMPLETE
};

class SparkTestRunner {

private:
    int _state;

public:
    SparkTestRunner() : _state(INIT) {

    }

    void begin();

    bool isStarted() {
        return _state>=RUNNING;
    }

    void start() {
        if (!isStarted())
            setState(RUNNING);
    }

    const char* nameForState(RunnerState state) {
        switch (state) {
            case INIT: return "init";
            case WAITING: return "waiting";
            case RUNNING: return "running";
            case COMPLETE: return "complete";
            default:
                return "";
        }
    }

    int testStatusColor();

    void updateLEDStatus() {
        int rgb = testStatusColor();
        RGB.control(true);
        //RGB.color(rgb);
        LED_SetSignalingColor(rgb);
        LED_On(LED_RGB);
    }

    RunnerState state() const { return (RunnerState)_state; }
    void setState(RunnerState newState) {
        if (newState!=_state) {
            _state = newState;
            const char* stateName = nameForState((RunnerState)_state);
            if (isStarted())
                updateLEDStatus();
            #ifdef CLOUD_ENABLE
              Spark.publish("state", stateName);
            #endif
        }
    }

    void testDone() {
        updateLEDStatus();
        delay(500);
    }
};

SparkTestRunner _runner;



#define UNIT_TEST_SETUP() \
    void setup() { unit_test_setup(); }

#define UNIT_TEST_LOOP() \
    void loop() { unit_test_loop(); }

#define UNIT_TEST_APP() \
    UNIT_TEST_SETUP(); UNIT_TEST_LOOP();


/*
Copyright (c) 2014 Matt Paine

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
THE SOFTWARE IS PROVIDED "AS IS", WITHOUT WARRANTY OF ANY KIND, EXPRESS OR
IMPLIED, INCLUDING BUT NOT LIMITED TO THE WARRANTIES OF MERCHANTABILITY,
FITNESS FOR A PARTICULAR PURPOSE AND NONINFRINGEMENT. IN NO EVENT SHALL THE
AUTHORS OR COPYRIGHT HOLDERS BE LIABLE FOR ANY CLAIM, DAMAGES OR OTHER
LIABILITY, WHETHER IN AN ACTION OF CONTRACT, TORT OR OTHERWISE, ARISING FROM,
OUT OF OR IN CONNECTION WITH THE SOFTWARE OR THE USE OR OTHER DEALINGS IN THE
SOFTWARE.
*/

/*
Copyright (c) 2009-2013 Matthew Murdoch

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
THE SOFTWARE IS PROVIDED "AS IS", WITHOUT WARRANTY OF ANY KIND, EXPRESS OR
IMPLIED, INCLUDING BUT NOT LIMITED TO THE WARRANTIES OF MERCHANTABILITY,
FITNESS FOR A PARTICULAR PURPOSE AND NONINFRINGEMENT. IN NO EVENT SHALL THE
AUTHORS OR COPYRIGHT HOLDERS BE LIABLE FOR ANY CLAIM, DAMAGES OR OTHER
LIABILITY, WHETHER IN AN ACTION OF CONTRACT, TORT OR OTHERWISE, ARISING FROM,
OUT OF OR IN CONNECTION WITH THE SOFTWARE OR THE USE OR OTHER DEALINGS IN
THE SOFTWARE.
*/
#pragma once


/**
 * A fake stream which can be used in place of other streams
 * to inject bytes to be read and to record any bytes written.
 *
 * @author Matthew Murdoch
 */
class FakeStream : public Stream {
public:
    /**
     * Creates a fake stream. Until nextByte() is called all bytes
     * returned from read() or peek() will be -1 (end-of-stream).
     */
    FakeStream();

    /**
     * Destroys this fake stream.
     */
    virtual ~FakeStream();

    /**
     * Writes a byte to this stream. The byte is recorded by appending
     * it to the internal store and can be observed by calling bytesWritten().
     *
     * @param val the byte to write
     * @return the number of bytes written (always 1)
     */
    size_t write(uint8_t val);

    /**
     * Flushes this stream. Does nothing in this implementation to avoid conflicts (false negative tests).
     */
    void flush();

    /**
     * Reset the FakeStream so that it can be reused across tests.
     * When called, 'bytesWritten' becomes empty  ("").
     */
    void reset();

    /**
     * The bytes written by calling write(uint8_t).
     *
     * @return the bytes written
     */
    const String& bytesWritten();

    /**
     * Sets the next value to be read via read() or peek() to -1 (end-of-stream).
     */
    void setToEndOfStream();

    /**
     * Sets the value of the next byte to be read via read() or peek().
     *
     * @param b the byte value
     */
    void nextByte(byte b);

    /**
     * The number of bytes available to be read.
     *
     * @return the number of available bytes (always 1)
     */
    int available();

    /**
     * Reads a byte, removing it from the stream.
     *
     * @return the byte passed to nextByte() or -1 (end-of-stream) if
     *         nextByte() has not been called or setToEndOfStream() has been called
     */
    int read();

    /**
     * Reads a byte without removing it from the stream.
     *
     * @return the byte passed to nextByte() or -1 (end-of-stream) if
     *         nextByte() has not been called or setToEndOfStream() has been called
     */
    int peek();

private:
    String _bytesWritten;
    int _nextByte;
};





/*
Copyright (c) 2009-2013 Matthew Murdoch

Permission is hereby granted, free of charge, to any person obtaining a copy
of this software and associated documentation files (the "Software"), to deal
in the Software without restriction, including without limitation the rights
to use, copy, modify, merge, publish, distribute, sublicense, and/or sell
copies of the Software, and to permit persons to whom the Software is
furnished to do so, subject to the following conditions:

The above copyright notice and this permission notice shall be included in
all copies or substantial portions of the Software.

THE SOFTWARE IS PROVIDED "AS IS", WITHOUT WARRANTY OF ANY KIND, EXPRESS OR
IMPLIED, INCLUDING BUT NOT LIMITED TO THE WARRANTIES OF MERCHANTABILITY,
FITNESS FOR A PARTICULAR PURPOSE AND NONINFRINGEMENT. IN NO EVENT SHALL THE
AUTHORS OR COPYRIGHT HOLDERS BE LIABLE FOR ANY CLAIM, DAMAGES OR OTHER
LIABILITY, WHETHER IN AN ACTION OF CONTRACT, TORT OR OTHERWISE, ARISING FROM,
OUT OF OR IN CONNECTION WITH THE SOFTWARE OR THE USE OR OTHER DEALINGS IN
THE SOFTWARE.
*/

FakeStream::FakeStream() : _nextByte(-1) {
}

FakeStream::~FakeStream() {
}

size_t FakeStream::write(uint8_t val) {
    _bytesWritten += (char) val;

    return size_t(1);
}

void FakeStream::flush() {
    // does nothing to avoid conflicts (false negative tests)
    // for test purpose, use 'reset' function instead
}

void FakeStream::reset() {
    _bytesWritten="";
    setToEndOfStream();
}

const String& FakeStream::bytesWritten() {
    return _bytesWritten;
}

void FakeStream::setToEndOfStream() {
    _nextByte = -1;
}

void FakeStream::nextByte(byte b) {
    _nextByte = b;
}

int FakeStream::available()  {
    return 1;
}

int FakeStream::read() {
    int b = _nextByte;
        _nextByte = -1;
    return b;
}

int FakeStream::peek() {
    return _nextByte;
}





struct BufferNode {
  byte value;
  BufferNode *next;
};

/**
 * A fake stream which can be used in place of other streams to inject bytes to
 * be read and to record any bytes written.
 *
 * @author Matthew Paine
 **/
class FakeStreamBuffer : public FakeStream {
    public:
        /**
         * Creates a fake stream.
         **/
        FakeStreamBuffer();

        /**
         * Destroys this fake stream.
         **/
        virtual ~FakeStreamBuffer();

        /**
         * Reset the FakeStream so that it can be reused across tests.  When called,
         * 'bytesWritten' becomes empty  ("") and the buffer is reset.
         **/
        void reset();

        /**
         * Pushes an end of stream (-1) to the end of the buffer
         **/
        void setToEndOfStream();

        /**
         * Appends the current buffer of values to be read via read() or peek()
         *
         * @param b the byte value
         **/
        void nextByte(byte b);

        /**
         * Appends the current buffer of values to be read via read() or peek()
         *
         * @param b the byte value
         **/
        void nextBytes(const char *s);

        /**
         * The number of bytes available to be read.
         *
         * @return the number of available bytes
         **/
        int available();

        /**
         * Reads a byte, removing it from the stream.
         *
         * @return the next byte in the buffer, or -1 (end-of-stream) if the buffer
         *         is empty or setToEndOfStream() has been called
         **/
        int read();

        /**
         * Reads a byte without removing it from the stream.
         *
         * @return the next byte in the buffer, or -1 (end-of-stream) if the buffer
         *         is empty or setToEndOfStream() has been called
         **/
        int peek();

    private:
        BufferNode *_firstNode;
        BufferNode *_lastNode;

        BufferNode* _createNode (byte value);
        void _appendNode(BufferNode *node);
        void _pushByte(byte value);
        BufferNode* _popNode();
        byte _nextByte();
        int _getBufferSize();
        int _getBufferSize(byte stopAt);
        void _clearBuffer();
};


/*
Copyright (c) 2014 Matt Paine

Permission is hereby granted, free of charge, to any person obtaining a copy
of this software and associated documentation files (the "Software"), to deal
in the Software without restriction, including without limitation the rights
to use, copy, modify, merge, publish, distribute, sublicense, and/or sell
copies of the Software, and to permit persons to whom the Software is
furnished to do so, subject to the following conditions:

The above copyright notice and this permission notice shall be included in all
copies or substantial portions of the Software.

THE SOFTWARE IS PROVIDED "AS IS", WITHOUT WARRANTY OF ANY KIND, EXPRESS OR
IMPLIED, INCLUDING BUT NOT LIMITED TO THE WARRANTIES OF MERCHANTABILITY,
FITNESS FOR A PARTICULAR PURPOSE AND NONINFRINGEMENT. IN NO EVENT SHALL THE
AUTHORS OR COPYRIGHT HOLDERS BE LIABLE FOR ANY CLAIM, DAMAGES OR OTHER
LIABILITY, WHETHER IN AN ACTION OF CONTRACT, TORT OR OTHERWISE, ARISING FROM,
OUT OF OR IN CONNECTION WITH THE SOFTWARE OR THE USE OR OTHER DEALINGS IN THE
SOFTWARE.
*/

FakeStreamBuffer::FakeStreamBuffer() : _firstNode(NULL), _lastNode(NULL) {
}

FakeStreamBuffer::~FakeStreamBuffer() {
}

void FakeStreamBuffer::reset() {
    _clearBuffer();
    FakeStream::reset();
}

void FakeStreamBuffer::setToEndOfStream() {
    _pushByte(-1);
}

void FakeStreamBuffer::nextByte(byte b) {
    _pushByte(b);
}

void FakeStreamBuffer::nextBytes(const char *s) {
    int next = 0;
    while (s[next] != 0) {
        nextByte((byte)s[next]);
        next++;
    }
}

int FakeStreamBuffer::available()  {
    return _getBufferSize(-1);
}

int FakeStreamBuffer::read() {
    if (_firstNode != NULL) {
        int ret = (int)_nextByte();
        if (ret == 255) {
            ret = -1;
        }
        return ret;
    }
    return -1;
}

int FakeStreamBuffer::peek() {
  if (_firstNode != 0) {
    return _firstNode->value;
  }
  return -1;
}

BufferNode* FakeStreamBuffer::_createNode (byte value) {
    BufferNode *node = (BufferNode*)malloc(sizeof(BufferNode));
    node->value = value;
    node->next = NULL;
    return node;
}

void FakeStreamBuffer::_appendNode(BufferNode *node) {
    if (_firstNode == NULL) {
        // This is the only node!
        _firstNode = node;
        _lastNode = node;
    }
    else {
        _lastNode->next = node;
        _lastNode = node;
    }
}

void FakeStreamBuffer::_pushByte (byte value) {
    BufferNode *node = _createNode (value);
    _appendNode(node);
}

BufferNode* FakeStreamBuffer::_popNode() {
    BufferNode *node = _firstNode;
    if (node != NULL) {
        _firstNode = node->next;
    }
    return node;
}

byte FakeStreamBuffer::_nextByte() {
    byte ret = -1;
    BufferNode *node = _popNode();
    if (node != NULL) {
        ret = node->value;
        free(node);
    }
    return ret;
}

int FakeStreamBuffer::_getBufferSize () {
    return _getBufferSize(-1);
}
int FakeStreamBuffer::_getBufferSize (byte stopAt) {
    int count = 0;
    BufferNode *node = _firstNode;
    while (node != 0 && node->value != stopAt) {
        count++;
        node = node->next;
    }
    return count;
}

void FakeStreamBuffer::_clearBuffer() {
    BufferNode *node = _firstNode;
    BufferNode *nextNode;
    while (node != 0) {
        nextNode = node->next;
        free(node);
        node = nextNode;
    }
    _firstNode = NULL;
    _lastNode = NULL;
}


/*
Copyright (c) 2009-2013 Matthew Murdoch

Permission is hereby granted, free of charge, to any person obtaining a copy
of this software and associated documentation files (the "Software"), to deal
in the Software without restriction, including without limitation the rights
to use, copy, modify, merge, publish, distribute, sublicense, and/or sell
copies of the Software, and to permit persons to whom the Software is
furnished to do so, subject to the following conditions:

The above copyright notice and this permission notice shall be included in
all copies or substantial portions of the Software.

THE SOFTWARE IS PROVIDED "AS IS", WITHOUT WARRANTY OF ANY KIND, EXPRESS OR
IMPLIED, INCLUDING BUT NOT LIMITED TO THE WARRANTIES OF MERCHANTABILITY,
FITNESS FOR A PARTICULAR PURPOSE AND NONINFRINGEMENT. IN NO EVENT SHALL THE
AUTHORS OR COPYRIGHT HOLDERS BE LIABLE FOR ANY CLAIM, DAMAGES OR OTHER
LIABILITY, WHETHER IN AN ACTION OF CONTRACT, TORT OR OTHERWISE, ARISING FROM,
OUT OF OR IN CONNECTION WITH THE SOFTWARE OR THE USE OR OTHER DEALINGS IN
THE SOFTWARE.
*/
#pragma once




/**

  @file ArduinoUnit.h

*/

#include <stdint.h>

#if ARDUINO >= 100 && ARDUINO < 103
#undef F
#undef PSTR
#define PSTR(s) (__extension__({static const char __c[] PROGMEM = (s); &__c[0];}))

#define F(string_literal) (reinterpret_cast<const __FlashStringHelper *>(PSTR(string_literal)))

#endif

#if defined(__GNUC__) && (__GNUC__*100 + __GNUC_MINOR__ < 407)
// Workaround for http://gcc.gnu.org/bugzilla/show_bug.cgi?id=34734
//
#ifdef PROGMEM
#undef PROGMEM
#define PROGMEM __attribute__((section(".progmem.data")))
#endif
#endif

// Workaround for Arduino Due
#if defined(__arm__) && !defined(PROGMEM)
#define PROGMEM
#define PSTR(s) s
#define memcpy_P(a, b, c) memcpy(a, b, c)
#define strlen_P(a) strlen(a)
#endif

/** \brief This is defined to manage the API transition to 2.X */
#define ARDUINO_UNIT_MAJOR_VERSION 2

/** \brief This is defined to manage the API transition to 2.X */
#define ARDUINO_UNIT_MINOR_VERSION 0

//
// These define what you want for output from tests.
//

/**
\brief Verbosity mask for overall summary (default).

Verbosity mask for a 1-line summary of the form:

    test summary: P passed, F failed, and S skipped out of T test(s).

This summary happens once all the tests have been resolved (pass, fail or skip).
*/
#define  TEST_VERBOSITY_TESTS_SUMMARY     0x01

/**
\brief Verbosity mask for failed test summary (default).

Verbosity mask for a 1-line summary of a failed test of the form:

    test NAME failed.

This summary happens once the given test resolves (pass, fail, or skip).
*/
#define  TEST_VERBOSITY_TESTS_FAILED      0x02

/**
\brief Verbosity mask for passed test summary (default).

Verbosity mask for a 1-line summary of a passed test of the form:

    test NAME passed.

This summary happens once the given test resolves (pass, fail, or skip).
*/
#define  TEST_VERBOSITY_TESTS_PASSED      0x04


/**
\brief Verbosity mask for skipped test summary (default).

Verbosity mask for a 1-line summary of a skipped test of the form:

    test NAME skipped.

This summary happens once the given test resolves (pass, fail, or skip).
*/
#define  TEST_VERBOSITY_TESTS_SKIPPED     0x08


/**
\brief Verbosity mask for resolved (skip, pass, or fail) test summary (default).

Verbosity mask for a 1-line summary of a resolved test of the form:

    test NAME (passed|failed|skipped).

This summary happens once the given test resolves (pass, fail, or skip).
*/
#define  TEST_VERBOSITY_TESTS_ALL         0x0F

/**
\brief Verbosity mask for failed assertions (default).

Verbosity mask for a 1-line summary of failed assertions of the form:

    FILE:LINE:1 fail assert (NAME1=VALUE1) OP (NAME2=VALUE2)

*/
#define  TEST_VERBOSITY_ASSERTIONS_FAILED 0x10

/**
\brief Verbosity mask for passed assertions (default off).

Verbosity mask for a 1-line summary of passed assertions of the form:

    FILE:LINE:1 pass assert (NAME1=VALUE1) OP (NAME2=VALUE2)

*/
#define  TEST_VERBOSITY_ASSERTIONS_PASSED 0x20

/**
\brief Verbosity mask for all assertions (default fail).

Verbosity mask for a 1-line summary of failed assertions of the form:

    FILE:LINE:1 (pass|fail) assert (NAME1=VALUE1) OP (NAME2=VALUE2)

*/
#define  TEST_VERBOSITY_ASSERTIONS_ALL    0x30

/**
This is the default value for TEST_MAX_VERBOSITY, and Test::max_verbosity is this, so no output is globally suppressed.
*/
#define  TEST_VERBOSITY_ALL               0x3F

/**
Verbosity mask for no verbostiy.  The default value of Test::min_verbosity asks that failed assertions and test summaries be generated (TEST_VERBOSITY_TESTS_ALL|TEST_VERBOSITY_ASSERTIONS_FAILED).
*/
#define  TEST_VERBOSITY_NONE              0x00


#ifndef TEST_MAX_VERBOSITY
/**
Define what output code is included in the in the library (default TEST_VERBOSITY_ALL).

Clearing a mask in TEST_MAX_VERBOSITY eliminates the code related to that kind of output.  Change this only to save PROGMEM space.
*/
#define TEST_MAX_VERBOSITY TEST_VERBOSITY_ALL
#endif


/** \brief Check if given verbosity exists. (advanced)

    This is used to mask out code that would never be
    executed due to a cleared flag in TEST_MAX_VERBOSITY.
    It is used in, for example:

        #if TEST_VERBOSITY_EXISTS(TESTS_SKIPPED)
           maybe output something
        #endif

    This would only rarely be useful in custom assertions.
*/
#define TEST_VERBOSITY_EXISTS(OF) ((TEST_MAX_VERBOSITY & TEST_VERBOSITY_ ## OF) != 0)

/** \brief Check if given verbosity exists. (advanced)

    This is used to mask out code that would never be
    executed due to a cleared flag in TEST_MAX_VERBOSITY.
    It is used in, for example:

        #if TEST_VERBOSITY_EXISTS(TESTS_SKIPPED)
           maybe output something
        #endif

    This would only rarely be useful in custom assertions.
*/

/** \brief Check if given verbosity is allowed. (advanced)

    This would only rarely be useful in custom assertions.

*/
#define TEST_VERBOSITY_ALLOWED(OF) (TEST_VERBOSITY_EXISTS(OF) && ((Test::max_verbosity & TEST_VERBOSITY_ ## OF) != 0))

/** \brief Check if given verbosity is required. (advanced)

    This would only rarely be useful in custom assertions.

*/
#define TEST_VERBOSITY_REQUIRED(OF) (TEST_VERBOSITY_ALLOWED(OF) && ((Test::min_verbosity & TEST_VERBOSITY_ ## OF) != 0))

/** \brief Check if given verbosity is appropriate. (advanced)

    This would only rarely be useful in custom assertions.

*/
#define TEST_VERBOSITY(OF) (TEST_VERBOSITY_ALLOWED(OF) && (((Test::min_verbosity & TEST_VERBOSITY_ ## OF ) != 0) || (((Test::current != 0) && ((Test::current->verbosity & TEST_VERBOSITY_ ## OF) != 0)))))

/**
There are two convenience macros for extending this class and
implement a one-step test (test macro), or a multi-step test
(testing macro).

One shot (first loop()) test

    test(me_once)
    {
      int x=1,y=2;
      assertNotEqual(x,y);
    }


Continuous (every loop() until pass(), fail(), or skip()) test

    testing(me_often) {
      assertEqual(digitalRead(errorPin),LOW);
    }

Roll-your-own test:

    class MyTest : public Test {
    public:
      MyTest(const char *name) : Test(name) {} {
        // can set verbosity here.
      }
      void setup() {
        // can set verbosity here.
        // call call pass(), fail(), or skip()
        // can make assertions
      }
      void loop()  {
        // can set verbosity here.
        // call call pass(), fail(), or skip()
        // can make assertions
      }
    };

    void setup() {
      // all tests are included by default
      Test::exclude("*_skip");
      if (no_slow_tests) Test::exclude("*_slow");
      if (all_crypto_tests) {
        Test::include("crypto_*");
        Test::exclude("crypto_*_skip");
      }
    }

    void loop() {
      Test::run();
    }

Variables you might want to adjust:

    static Print* Test::out

 - the stream that is used for output
 - defaults to

       &Serial

 - This affects the output of all tests

    uint8_t verbosity

 - how much to report on output

 -- defaults to

       TEST_VERBOSITY_ASSERTIONS_FAILED|TEST_VERBOSITY_TESTS_ALL

 -- to keep code small, reporting code that is not set in

       TEST_MAX_VERBOSITY

    is removed, so setting verbosity bits outside this mask
    has no effect.  The default mask is to have all output
    available, and the only reason to change this is to save
    some code space.
*/
class Test
{
    friend class SparkTestRunner;

 private:
  // allows for both ram/progmem based names
  class TestString : public Printable {
  public:
    const uint32_t data;
    TestString(const char *_data);
    void read(void *destination, uint16_t offset, uint8_t length) const;
    uint16_t length() const;
    int8_t compare(const Test::TestString &to) const;
    size_t printTo(Print &p) const;
    bool matches(const char *pattern) const;
  };

 private:
  // linked list structure for active tests
  static Test* root;
  Test *next;

  // static statistics for tests
  static uint32_t passed;
  static uint32_t failed;
  static uint32_t skipped;
  static uint32_t count;

  void resolve();
  void remove();
  void insert();

 public:

  /** After the compile-time-mask TEST_MAX_VERBOSITY, this is a global
      run-time-mask of what output should be generated.
  */
  static uint8_t max_verbosity;

  /** After the compile-time-mask TEST_MAX_VERBOSITY, and the global
      (static) run-time-mask Test::max_verbosity of what output can be
      generated, this is a global (static) run-time-mask of what output
      should be generated. */
  static uint8_t min_verbosity;

  static inline uint16_t getCurrentPassed() { return passed; }
  static inline uint16_t getCurrentSkipped() { return skipped; }
  static inline uint16_t getCurrentFailed() { return failed; }
  static uint16_t getCurrentCount() { return count; }

  /** State of a test before a setup() call.  The exclude()
      function may move a test directly from UNSETUP to DONE_SKIP. */
  static const uint8_t UNSETUP;

  /** State of a test while actively in loop().  Tests are resolved
      by changing state one of the DONE_ states. */
  static const uint8_t LOOPING;

  /** State of a test that will be counted as skipped.  This can be
      done any time before resolving the test some other way, but
      should mean some small amount of steps to determine that no
      actual testing was done. */
  static const uint8_t DONE_SKIP;

  /** State of a passed test. */
  static const uint8_t DONE_PASS;

  /** State of a failed test. */
  static const uint8_t DONE_FAIL;

  /** /brief Output stream for all tests.
      The default value of this is
      ```
          Test::out = &Serial;
      ```
      This places the output on the main serial port.  The library
      does not set the baud rate, so you must do so in your setup().

      To redirect all output to some other stream, say the Serial3
      device of the arduino mega, use

          Serial3.begin(19200L);
          Test::out = &Serial3;

      in your setup().
  */
  static Print *out;

  /** The current state of this test.  It is one of:

           UNSETUP, LOOPING, DONE_PASS, DONE_FAIL, DONE_SKIP

  */
  uint8_t state;

  /** The current active test (=0 if none are active).  Asserts
      are allowed outside of tests, but just return if fail and
      potentially (according to min_verbosity and max_verbosity)
      print a message to the Test::out stream.
  */
  static Test* current;

  /** the name of this test */
  TestString name;

  /** Per-test verbosity defaults to TEST_VERBOSITY_TESTS_ALL|TEST_VERBOSITY_ASSERTS_FAILED, but note that the compile-time constant TEST_VERBOSITY_MAX and run-time global (static) values Test::max_verbosity and Test::min_verbosity also effect the verbosity of a test.  According to the following rules:

    output = false;
    if (TEST_MAX_VERBOSITY bit is set (output KIND exists)) {
      if (all-test Test::max_verbosity bit is set (output KIND allowed)) {
        if (all-test Test:min_verbosity bit is set (output KIND required)) {
          output = true;
        } else if (per-test Test::verbosity bit is set (output KIND use)) {
          output = true;
        }
      }
    }

    if (output) { OUTPUT to Test::out }
  */
  uint8_t verbosity;

  /** Set state to DONE_PASS.  This does not exit the code early.  But after
      the loop() terminates, the test will be resolved and removed from the
      list of active tests. */
  void pass();


  /** Set state to DONE_FAIL.  This does not exit the code early.  But after
      the loop() terminates, the test will be resolved and removed from the
      list of active tests. */
  void fail();


  /** Set state to DONE_SKIP.  This does not exit the code early.  But after
      the loop() terminates, the test will be resolved and removed from the
      list of active tests. */
  void skip();

  /** Setup a test.  This is an nop {} definition by default, but for some
      more general cases it will be called once from before continuously
      calling Test::loop().  You can skip(), pass(), fail(), set verbosities, or make assertions here.*/
  virtual void setup();

  /** Run a test.  Test::loop() will be called on each Test::run() until a pass(), fail() or skip(). */
  virtual void loop() = 0;

  /** include (use) currently excluded (skipped) tests that match some
  wildcard (*) pattern like,

      "dev_*", "my_main_test", "*_quick"

  Since all tests are included by default, this is not useful except
  after an exclude() call.

  This should be done inside your setup() function.
  */
  static void include(const char *pattern);

  /**
exclude (skip) currently included tests that match some
wildcard (*) pattern like,

      "my_broken_test", "*_skip", "*", "io_*", etc.

This should be done inside your setup() function.
  */
static void exclude(const char *pattern);

/**

Simple usage:

    void setup() {
      Serial.begin(9600);
    }

    void loop() {
      Test::run();
    }

Complex usage:

    void setup() {
      Test::exclude("*"); // exclude everything
      Test::include("io_*"); // but include io_* tests
      Test::exclude("io_*_lcd"); // except io_*_lcd tests
      Test::include("crypto_*_aes128"); // and use all crypto_*_aes128 tests
    }

void loop() {
  Test::run();
}
  */
  static void run();

  // Construct a test with a given name and verbosity level

  Test(const char *_name, uint8_t _verbosity = TEST_VERBOSITY_TESTS_ALL|TEST_VERBOSITY_ASSERTIONS_FAILED);

  virtual ~Test();

  template <typename T>
    static bool assertion(const char *file, uint16_t line, const char *lhss, const T& lhs, const char *ops, bool (*op)(const T& lhs, const T& rhs), const char *rhss, const T& rhs) {
    bool ok = op(lhs,rhs);
    bool output = false;

    if ((!ok) && (current != 0)) current->fail();

#if TEST_VERBOSITY_EXISTS(ASSERTIONS_PASSED)
    if (ok && TEST_VERBOSITY(ASSERTIONS_PASSED)) {
      output = true;
    }
#endif

#if TEST_VERBOSITY_EXISTS(ASSERTIONS_FAILED)
    if ((!ok) && TEST_VERBOSITY(ASSERTIONS_FAILED)) {
      output = true;
    }
#endif

#if TEST_VERBOSITY_EXISTS(ASSERTIONS_FAILED) || TEST_VERBOSITY_EXISTS(ASSERTIONS_PASSED)
    if (output) {
      out->print(F("Assertion "));
      out->print(ok ? F("passed") : F("failed"));
      out->print(F(": ("));
      out->print(lhss);
      out->print(F("="));
      out->print(lhs);
      out->print(F(") "));
      out->print(ops);
      out->print(F(" ("));
      out->print(rhss);
      out->print(F("="));
      out->print(rhs);
      out->print(F("), file "));
      out->print(file);
      out->print(F(", line "));
      out->print(line);
      out->println(".");
    }
#endif
    return ok;
  }
};

/** Class for creating a once-only test.  Test::run() on such a test
    calls Test::setup() once, and (if not already resolved from the
    setup(), calls Test::once() */
class TestOnce : public Test {
 public:
  TestOnce(const char *name);
  void loop();
  virtual void once() = 0;
};

/** Template binary operator== to assist with assertions */
template <typename T>
bool isEqual(const T& a, const T& b) { return a==b; }

/** Template binary operator!= to assist with assertions */
template <typename T>
bool isNotEqual(const T& a, const T& b) { return !(a==b); }

/** Template binary operator< to assist with assertions */
template <typename T>
bool isLess(const T& a, const T& b) { return a < b; }

/** Template binary operator> to assist with assertions */
template <typename T>
bool isMore(const T& a, const T& b) { return b < a; }

/** Template binary operator<= to assist with assertions */
template <typename T>
bool isLessOrEqual(const T& a, const T& b) { return !(b<a); }

/** Template binary operator>= to assist with assertions */
template <typename T>
bool isMoreOrEqual(const T& a, const T& b) { return !(a<b); }

/** Template specialization for asserting const char * types */
template <> bool isLess<const char*>(const char* const &a, const char* const &b);

/** Template specialization for asserting const char * types */
template <> bool isLessOrEqual<const char*>(const char* const &a, const char* const &b);

/** Template specialization for asserting const char * types */
template <> bool isEqual<const char*>(const char* const &a, const char* const &b);

/** Template specialization for asserting const char * types */
template <> bool isNotEqual<const char*>(const char* const &a, const char* const &b);

/** Template specialization for asserting const char * types */
template <> bool isMore<const char*>(const char* const &a, const char* const &b);

/** Template specialization for asserting const char * types */
template <> bool isMoreOrEqual<const char*>(const char* const &a, const char* const &b);


/** Create a test-once test, usually checked with assertXXXX.
    The test is assumed to pass unless failed or skipped. */
#define test(name) struct test_ ## name : TestOnce { test_ ## name() : TestOnce(F(#name)) {}; void once(); } test_ ## name ## _instance; void test_ ## name :: once()

#define test_f(fixture, name) struct test_ ## name : fixture { test_ ## name() : fixture(F(#name)) {}; void once(); } test_ ## name ## _instance; void test_ ## name :: once()


/** Create an extern reference to a test-once test defined elsewhere.

This is only necessary if you use assertTestXXXX when the test
is in another file (or defined after the assertion on it). */
#define externTest(name) struct test_ ## name : TestOnce { test_ ## name(); void once(); }; extern test_##name test_##name##_instance

/** Create an extern reference to a test-until-skip-pass-or-fail test
   defined elsewhere.

This is only necessary if you use assertTestXXXX when the test
is in another file (or defined after the assertion on it). */
#define testing(name) struct test_ ## name : Test { test_ ## name() : Test(F(#name)) {}; void loop(); } test_ ## name ## _instance; void test_ ## name :: loop()

/** Create an extern reference to a test-until-skip-pass-or-fail defined
elsewhere.  This is only necessary if you use assertTestXXXX when the test
is in another file (or defined after the assertion on it). */
#define externTesting(name) struct test_ ## name : Test { test_ ## name(); void loop(); }; extern test_##name test_##name##_instance

// helper define for the operators below
#define assertOp(arg1,op,op_name,arg2) if (!Test::assertion<typeof(arg2)>(F(__FILE__),__LINE__,F(#arg1),(arg1),F(op_name),op,F(#arg2),(arg2))) return;

/** macro generates optional output and calls fail() followed by a return if false. */
#define assertEqual(arg1,arg2)       assertOp(arg1,isEqual,"==",arg2)

/** macro generates optional output and calls fail() followed by a return if false. */
#define assertNotEqual(arg1,arg2)    assertOp(arg1,isNotEqual,"!=",arg2)

/** macro generates optional output and calls fail() followed by a return if false. */
#define assertLess(arg1,arg2)        assertOp(arg1,isLess,"<",arg2)

/** macro generates optional output and calls fail() followed by a return if false. */
#define assertMore(arg1,arg2)        assertOp(arg1,isMore,">",arg2)

/** macro generates optional output and calls fail() followed by a return if false. */
#define assertLessOrEqual(arg1,arg2) assertOp(arg1,isLessOrEqual,"<=",arg2)

/** macro generates optional output and calls fail() followed by a return if false. */
#define assertMoreOrEqual(arg1,arg2) assertOp(arg1,isMoreOrEqual,">=",arg2)

/** macro generates optional output and calls fail() followed by a return if false. */
#define assertTrue(arg) assertEqual(arg,true)

/** macro generates optional output and calls fail() followed by a return if false. */
#define assertFalse(arg) assertEqual(arg,false)

#define checkTestDone(name) (test_##name##_instance.state >= Test::DONE_SKIP)

/** check condition only */
#define checkTestNotDone(name) (test_##name##_instance.state < Test::DONE_SKIP)

/** check condition only */
#define checkTestPass(name) (test_##name##_instance.state == Test::DONE_PASS)

/** check condition only */
#define checkTestNotPass(name) (test_##name##_instance.state != Test::DONE_PASS)

/** check condition only */
#define checkTestFail(name) (test_##name##_instance.state == Test::DONE_FAIL)

/** check condition only */
#define checkTestNotFail(name) (test_##name##_instance.state != Test::DONE_FAIL)

/** check condition only */
#define checkTestSkip(name) (test_##name##_instance.state == Test::DONE_SKIP)

/** check condition only */
#define checkTestNotSkip(name) (test_##name##_instance.state != Test::DONE_SKIP)

/** macro generates optional output and calls fail() followed by a return if false. */
#define assertTestDone(name) assertMoreOrEqual(test_##name##_instance.state,Test::DONE_SKIP)
/** macro generates optional output and calls fail() followed by a return if false. */
#define assertTestNotDone(name) assertLess(test_##name##_instance.state,Test::DONE_SKIP)

/** macro generates optional output and calls fail() followed by a return if false. */
#define assertTestPass(name) assertEqual(test_##name##_instance.state,Test::DONE_PASS)

/** macro generates optional output and calls fail() followed by a return if false. */
#define assertTestNotPass(name) assertNotEqual(test_##name##_instance.state,Test::DONE_PASS)

/** macro generates optional output and calls fail() followed by a return if false. */
#define assertTestFail(name) assertEqual(test_##name##_instance.state,Test::DONE_FAIL)

/** macro generates optional output and calls fail() followed by a return if false. */
#define assertTestNotFail(name) assertNotEqual(test_##name##_instance.state,Test::DONE_FAIL)

/** macro generates optional output and calls fail() followed by a return if false. */
#define assertTestSkip(name) assertEqual(test_##name##_instance.state,Test::DONE_SKIP)

/** macro generates optional output and calls fail() followed by a return if false. */
#define assertTestNotSkip(name) assertNotEqual(test_##name##_instance.state,Test::DONE_SKIP)


const uint8_t Test::UNSETUP = 0;
const uint8_t Test::LOOPING = 1;
const uint8_t Test::DONE_SKIP = 2;
const uint8_t Test::DONE_PASS = 3;
const uint8_t Test::DONE_FAIL = 4;

Test::TestString::TestString(const char *_data) : data((uint32_t)_data) {}

void Test::TestString::read(void *destination, uint16_t offset, uint8_t length) const
{
    memcpy(destination,(char*)(data+offset),length);
}

uint16_t Test::TestString::length() const {
    return strlen((char*)(data));
}

int8_t Test::TestString::compare(const Test::TestString &to) const
{
  uint8_t a_buf[4],b_buf[4];
  uint16_t i=0;

  for (;;) {
    uint8_t j=(i%4);
    if (j == 0) {
      this->read(a_buf,i,4);
      to.read(b_buf,i,4);
    }
    if (a_buf[j] < b_buf[j]) return -1;
    if (a_buf[j] > b_buf[j]) return  1;
    if (a_buf[j] == 0) return 0;
    ++i;
  }
}

size_t Test::TestString::printTo(Print &p) const {
    return p.print((char*)data);
}

bool Test::TestString::matches(const char *pattern) const {
  uint8_t np = strlen(pattern);
  uint8_t ns = length();
  uint8_t nb = (np+2)/8+((np+2)%8 != 0);
  uint8_t k;
  uint8_t buffer[8];

  uint8_t buffer0[nb];
  uint8_t buffer1[nb];

  uint8_t *state0=buffer0;
  uint8_t *state1=buffer1;

  memset(state0,0,nb);
  state0[0]=1;
  for (k=1; pattern[k-1] == '*'; ++k) state0[k/8] |= (1 << (k%8));

  for (int i=0; i<=ns; ++i) {
    if ((i%sizeof(buffer)) == 0) {
      uint8_t n=sizeof(buffer);
      if (ns+1-i < n) n=ns+1-i;
      read(buffer,i,n);
    }
    uint8_t c=buffer[i%sizeof(buffer)];

    memset(state1,0,nb);
    for (int j=0; j<=np; ++j) {
      if (state0[j/8] & (1 << (j%8))) {
        if (pattern[j] == '*') {
          k=j;
          state1[k/8] |= (1 << (k%8));
          ++k;
          state1[k/8] |= (1 << (k%8));
        } else if (pattern[j] == c) {
          k=j+1;
          state1[k/8] |= (1 << (k%8));
          while (pattern[k] == '*') {
            ++k;
            state1[k/8] |= (1 << (k%8));
          }
        }
      }
    }

    uint8_t *tmp = state0;
    state0 = state1;
    state1 = tmp;
  }

  k=np+1;
  return (state0[k/8]&(1<<(k%8))) != 0;
}

Test* Test::root = 0;
Test* Test::current = 0;

uint32_t Test::count = 0;
uint32_t Test::passed = 0;
uint32_t Test::failed = 0;
uint32_t Test::skipped = 0;
uint8_t Test::max_verbosity = TEST_VERBOSITY_ALL;
uint8_t Test::min_verbosity = TEST_VERBOSITY_TESTS_SUMMARY;

Print* Test::out = &Serial;

void Test::resolve()
{
  bool pass = current->state==DONE_PASS;
  bool fail = current->state==DONE_FAIL;
  bool skip = current->state==DONE_SKIP;
  bool done = (pass || fail || skip);

  if (done) {
    if (pass) ++Test::passed;
    if (fail) ++Test::failed;
    if (skip) ++Test::skipped;

    _runner.testDone();

#if TEST_VERBOSITY_EXISTS(TESTS_SKIPPED) || TEST_VERBOSITY_EXISTS(TESTS_PASSED) || TEST_VERBOSITY_EXISTS(TESTS_FAILED)

    bool output = false;

    output = output || (skip && TEST_VERBOSITY(TESTS_SKIPPED));
    output = output || (pass && TEST_VERBOSITY(TESTS_PASSED));
    output = output || (fail && TEST_VERBOSITY(TESTS_FAILED));

    if (output) {
      out->print(F("Test "));
      out->print(name);
#if TEST_VERBOSITY_EXISTS(TESTS_SKIPPED)
      if (skip) out->println(F(" skipped."));
#endif

#if TEST_VERBOSITY_EXISTS(TESTS_PASSED)
      if (pass) out->println(F(" passed."));
#endif

#if TEST_VERBOSITY_EXISTS(TESTS_FAILED)
      if (fail) out->println(F(" failed."));
#endif
    }
#endif
  }
#if TEST_VERBOSITY_EXISTS(TESTS_SUMMARY)
  if (root == 0 && TEST_VERBOSITY(TESTS_SUMMARY)) {
    out->print(F("Test summary: "));
    out->print(passed);
    out->print(F(" passed, "));
    out->print(failed);
    out->print(F(" failed, and "));
    out->print(skipped);
    out->print(F(" skipped, out of "));
    out->print(count);
    out->println(F(" test(s)."));
  }
#endif
}

void Test::remove()
{
  for (Test **p = &root; *p != 0; p=&((*p)->next)) {
    if (*p == this) {
      *p = (*p)->next;
      break;
    }
  }
}

Test::Test(const char *_name, uint8_t _verbosity)
  : name(_name), verbosity(_verbosity)
{
  insert();
}

void Test::insert()
{
  state = UNSETUP;
  { // keep list sorted
    Test **p = &Test::root;
    while ((*p) != 0) {
      if (name.compare((*p)->name) <= 0) break;
      p=&((*p)->next);
    }
    next=(*p);
    (*p)=this;
  }
  ++Test::count;
}

void Test::pass() { state = DONE_PASS; }
void Test::fail() { state = DONE_FAIL; }
void Test::skip() { state = DONE_SKIP; }

void Test::setup() {};

void Test::run()
{
  _runner.setState(root ? RUNNING : COMPLETE);

  for (Test **p = &root; (*p) != 0; ) {
    current = *p;

    if (current->state == LOOPING) {
      current->loop();
    } else if (current->state == UNSETUP) {
      current->setup();
      if (current->state == UNSETUP) {
        current->state = LOOPING;
      }
    }

    if (current->state != LOOPING) {
      (*p)=((*p)->next);
      current->resolve();
    } else {
      p=&((*p)->next);
    }
    break;  // allow main loop to execute
  }
}

Test::~Test()
{
  remove();
}

void Test::include(const char *pattern)
{
  for (Test *p = root; p != 0; p=p->next) {
    if (p->state == DONE_SKIP && p->name.matches(pattern)) {
      p->state = UNSETUP;
    }
  }
}

void Test::exclude(const char *pattern)
{
  for (Test *p = root; p != 0; p=p->next) {
    if (p->state == UNSETUP && p->name.matches(pattern)) {
      p->state = DONE_SKIP;
    }
  }
}

TestOnce::TestOnce(const char *name) : Test(name) {}

void TestOnce::loop()
{
  once();
  if (state == LOOPING) state = DONE_PASS;
}

template <>
bool isLess<const char*>(const char* const &a, const char* const &b)
{
  return (strcmp(a,b) < 0);
}

template <>
bool isLessOrEqual<const char*>(const char* const &a, const char* const &b)
{
  return (strcmp(a,b) <= 0);
}

template <>
bool isEqual<const char*>(const char* const &a, const char* const &b)
{
  return (strcmp(a,b) == 0);
}

template <>
bool isNotEqual<const char*>(const char* const &a, const char* const &b)
{
  return (strcmp(a,b) != 0);
}

template <>
bool isMoreOrEqual<const char*>(const char* const &a, const char* const &b)
{
  return (strcmp(a,b) >= 0);
}

template <>
bool isMore<const char*>(const char* const &a, const char* const &b)
{
  return (strcmp(a,b) > 0);
}

/**
 * A convenience method to setup serial.
 */
void unit_test_setup()
{
    Serial.begin(9600);
    _runner.begin();
}

bool requestStart = false;
bool _enterDFU = false;

bool isStartRequested(bool runImmediately) {
    if (runImmediately || requestStart)
        return true;
    if (Serial.available()) {
        char c = Serial.read();
        if (c=='t') {
            return true;
        }
    }

    return false;
}

/*
 * A convenience method to run tests as part of the main loop after a character
 * is received over serial.
 **/
void unit_test_loop(bool runImmediately=false)
{
    if (_enterDFU)
        System.bootloader();

    if (!_runner.isStarted() && isStartRequested(runImmediately)) {
        Serial.println("Running tests");
        _runner.start();
    }

    if (_runner.isStarted()) {
        Test::run();
    }
}

int SparkTestRunner::testStatusColor() {
    if (Test::failed>0)
        return RGB_COLOR_RED;
    else if (Test::skipped>0)
        return RGB_COLOR_ORANGE;
    else
        return RGB_COLOR_GREEN;
}

int testCmd(String arg) {
    int result = 0;
    if (arg.equals("start")) {
        requestStart = true;
    }
    else if (arg.startsWith("exclude=")) {
        String pattern = arg.substring(8);
        Test::exclude(pattern.c_str());
    }
    else if (arg.startsWith("include=")) {
        String pattern = arg.substring(8);
        Test::include(pattern.c_str());
    }
    else if (arg.equals("enterDFU")) {
        _enterDFU = true;
    }
    else
        result = -1;
    return result;
}

void SparkTestRunner::begin() {
  #ifdef CLOUD_ENABLE
    Spark.variable("passed", &Test::passed, INT);
    Spark.variable("failed", &Test::failed, INT);
    Spark.variable("skipped", &Test::skipped, INT);
    Spark.variable("count", &Test::count, INT);
    Spark.variable("state", &_state, INT);
    Spark.function("cmd", testCmd);
    setState(WAITING);
  #endif
}
